Timzhao0205/PhD_Career_Portfolio/02_Startup/07_Frontier_Ideas_Interactive_2026-07/outputs/20_p4/P4_REPORT.md

# P4 scoring report (2026-07-28)

All 65 frozen longlist ideas were scored independently by the main Fable
5/xhigh agent against the 100-point rubric with hard gates G1-G7. Inputs:
frozen longlist records, the EVIDENCE files (facts and cited sources only —
historical analyst gate opinions treated as non-binding), the source atlas,
and the stage-10 refresh (R10-001..R10-079). Every score above 3 carries cited
source IDs. Weighted points equal score x weight / 5 and reconcile to totals
within 0.25 (one authoring slip on P3R2-D-18 was caught by the arithmetic
self-check and corrected to 66.7 before assembly).

## Calibration

Anchors: dual-leg, primary-evidenced demand with genuine whitespace and strong
founder transfer lands ~72-82 (D-02, C-01, D-10, C-05). Real-but-contested or
single-leg theses land ~55-67. Totals below ~55 almost always coincide with a
gate failure. The pilot's three fresh scores (C-09 73.7 / A-16 53.8 / F-15
47.9) were not reused; full-pass rescoring produced 72.0, 52.0, and 47.0 —
within calibration drift of the anchors.

## Distribution

- 65 scored: max 81.9 (D-02), min 44.4 (A-03), median ~62.7.
- Dispositions: 41 advance, 3 advance-with-repair (A-10, C-13, F-01 — G6
  counterparty restructuring off BIS Entity-Listed named buyers), 17
  eliminate on G1, 4 eliminate on G7.

## Gate failures (21 ideas)

G1 (demand) failures: A-03 (its own pre-declared kill condition met — Texas RE
guidance shows model-based PRC-029 compliance), A-11 (no buyer evidence; SEMI
E17 revision absent), A-16 (mid-supply-chain TIM, no buyer instrument), B-06,
B-14, B-22 (each failed its own binding pre-promotion condition after direct
search), D-11 (demand citations mis-typed; incumbent CO2 roadmap negative),
D-20 (leading thermal-battery architecture needs no liquid metal), E-02 (no
OEM agreement; AIM Act anchor litigated and relaxed), F-04 (externalization
thesis untested; CN leg failed its own conditional), F-05 (EPA funds new
equipment, not repowers; CARB tailwind reversing), F-11 (process substitution
with zero product demand), F-15 (bundled EPC procurement; SOE in-house
preference), F-17 (demand contingent on undated regulation; named buyer
Entity-Listed), F-22 (Guoli already occupies the CN second-source position),
G-01 (CEPC excluded from the 15th FYP — anchor trigger negated; binding
multi-tender condition unmet), G-02 (component pain inferred; no CNNC
follow-on tender).

G7 (timing) failures: C-02 (Delta ships the buffer function now — kill trigger
effectively tripped), C-03 (funded SST rivals occupy the window; the named
certification instrument does not cover the problem), D-08 (EtO NESHAP repeal
proposed; incumbents filling capacity before 2030), E-11 (ASE/TSMC in-house
thermal solutions ramp 2026; laser-relocation workarounds).

## Lane comparison

Strongest lanes: L03 (D-02 81.9, D-01 72.9 — conductor volume scales
independently of fusion success), L02/L08 datacenter-DC cluster (C-01 80.5,
E-14 75.5, G-03 67.8, A-02 64.8), L14 metrology/ops slice (C-05 78.3, F-19
64.6) outperforming L14 hardware bets, L12 defense photonics (D-10 78.7, C-13
74.2), L06 instrumentation (A-10 74.2, F-01 73.2). Weakest: CN-only ideas
whose own promotion conditions failed (B-06, B-14, F-15, F-17), and heavy-
capex power hardware without buyer instruments (C-03, C-12 54.9 survives
gates but ranks last-but-one among candidates). The refresh moved real ranks:
CEPC's exclusion eliminated G-01 and deflated F-09's CN leg; the H2Hubs
turbulence (2 hubs terminated, 5 restored ~$5B) reduced but did not eliminate
the hydrogen ideas (C-22 71.4, F-23 63.4, C-07 61.6).

## Survivor cut

Selection rule: exactly 30 — all gate-clean ideas ranked by total_100; G1/G7
eliminations excluded regardless of total. The cut fell at 62.7 (P3R2-F-10 in;
P3R2-C-07 out at 61.6, then C-21 60.4, F-06 59.5, A-13 59.5, F-02 59.4, A-21
58.7, D-07 58.4, F-03 58.3, F-07 58.2, F-20 57.7, C-19 56.0, F-12 56.0, F-09
55.2, C-12 54.9). Near-miss preservation: C-07's electrowinning fallback,
F-20's fold-into-C-09 path, and C-19's pairing with C-08 are recorded for
P5/P7 reconsideration if survivors fail red-team. Three survivors carry a
mandatory P5 repair focus: A-10 and C-13 must re-point CN legs off
Entity-Listed counterparties; F-01 must restructure its HK golden-reference
licensing scheme (strict-liability 50% Affiliates Rule).
