Timzhao0205/PhD_Career_Portfolio/02_Startup/07_Frontier_Ideas_Interactive_2026-07/outputs/70_audit/FINAL/PORTFOLIO/00_EXECUTIVE.md

# Executive synthesis — Folder 06 rerun, final 24 and top 10

## Recommendation

Fund the ten Tier-1 decisive experiments now ($3.47M total, every one
executable by 2028, every one carrying a written kill rule), hold the six
Tier-2 experiments as sequenced follow-ons ($2.08M), and treat the eight
Tier-3 ideas as tracked options ($2.75M) exercised only on their named
triggers. The portfolio's structural bet is consistent across lanes:
**neutral measurement, qualification, protection, and control layers for
infrastructure classes that are being built out faster than their
evidence layers** — REBCO conductors, 800 VDC datacenters, liquid
cooling, directed energy, HVDC transmission, superhot geothermal,
leading-edge etch, pulsed power, and electrolysis. No idea requires a
science breakthrough; every one requires disciplined instrumentation,
integration, and certification — the founder's stack.

## Tiers

**Tier 1 — fund the experiment now (ranks 1-8 plus C-09, C-22; the ten
deep dives).** P3R2-D-02 tape metrology ($120k), P3R2-C-01 800 VDC
protection ($350k), P3R2-C-05 cooling conformance ($150k), P3R2-D-10 CBC
phase control ($250k), P3R2-E-14 DC protection/HIL ($300k), P3R2-A-14
300 °C electronics ($850k, staged with a $250k first gate), P3R2-D-01
quench protection ($250k), P3R2-A-10 ion-energy control ($450k),
P3R2-C-09 pulsed-power modules ($500k, staged), P3R2-C-22 electrolyzer
bankability benches ($250k). Deep dives D01-D10 carry full plans,
scenario analyses, and dated kill gates.

**Tier 2 — sequence second ($2.08M).** C-13 GaN pump drivers ($180k),
F-01 solid-state RF matching ($250k), A-05 NEG coating ($250k), C-08
transient-qualified PCHEs ($600k), G-03 DC acceptance instrumentation
($300k), E-04 cryogenic interconnect ($500k). Each is fundable on its
own evidence; they sit behind Tier 1 for portfolio-concentration
reasons (C-13 overlaps D-10's buyer set; F-01 overlaps A-10's chamber
ecosystem; the rest carry heavier hardware risk per dollar of early
information).

**Tier 3 — tracked options ($2.75M).** D-09 FLASH dosimetry, A-22 PFAS
plasma destruction, C-04 PFAS-free two-phase loop, D-19 flywheel
buffers, F-16 plasma surface treatment (CN-primary), F-19 coolant
health, F-23 electrolyzer envelope controllers, D-16 space Brayton.
Each has a named exercise trigger in 04_ROADMAP.md; none should burn
capital before its trigger fires.

## Uncertainty, stated plainly

- **Repair-verdict ideas.** A-10, C-13, and F-01 carry stage-30 repair
  verdicts: their original CN structures were compliance-blocked
  (Entity List/VEU). All three are carried with restructured, gated CN
  chapters and US-primary base cases. Their cards say so; no repaired
  leg is presented as unconditional.
- **Confidence distribution.** Seven ideas carry high P4 confidence,
  fifteen medium, two low (F-23, D-16 — both Tier 3, both option-priced).
- **Residual risk.** Sixteen ideas sit at medium residual risk, eight at
  high — all eight high-residual ideas are Tier 2/3 except none in
  Tier 1; the deep-dived ten are uniformly medium.
- **Two constraints unsatisfiable by construction** (recorded in
  outputs/40_select/PORTFOLIO_CHECKS.json, restated here rather than
  hidden): no sub-$100k first experiment exists in the frozen pool
  (minimum $120k), and only 14 China beachheads / 13 dual-market
  structures were achievable against an 18-CN-beachhead aspiration,
  because CN-heavy candidates failed their own binding evidence gates
  at P4. The portfolio buys real dual-market exposure where it is
  deliverable and refuses to fabricate it where it is not.
- **Schedule-shaped risks.** D-10's design-win window (2026-2028) runs
  ahead of the 2030 launch convention and is handled as pre-company
  work; C-22 and F-23 are levered to hydrogen FID trajectories; D-01
  and D-02 are levered to the SPARC-to-ARC conversion.

## Resource allocation

Total decisive-experiment exposure across all 24: **$8.30M**, of which
Tier 1 is $3.47M. Recommended sequencing: start the four cheapest
highest-information Tier-1 experiments in 2026-2027 (D-02 $120k, C-05
$150k, C-22 $250k, D-10 $250k — combined $770k buys four kill verdicts),
run the remaining six Tier-1 gates through 2027-2028, and release Tier-2
capital only as Tier-1 verdicts land. Staged experiments (A-14, C-09)
gate internally so worst-case exposure is the first stage, not the
headline. Every experiment's pass and kill thresholds are tabulated in
04_ROADMAP.md; every card in 01_IDEA_CARDS.md names its kill condition.

## What would change this recommendation

A Tier-1 kill-gate failure removes that idea without substitution (the
final 24 and top 10 are frozen identities; any forced change returns to
Stage 40 per the route contract). External events with standing
portfolio effect: an OCP full-methodology release (C-05 scenario B), a
CFS-published protection standard (D-01 scenario B), JBCS awards with no
subsystem carve-out (D-10 scenario B), integrated IEDF-inference
releases (A-10 scenario B), and hydrogen FID collapse (C-22/F-23
scenario D). Each is an observable, dated public event tracked in the
roadmap's monitoring calendar.
