Timzhao0205/PhD_Career_Portfolio/03_Investments_and_Finance/03_Investments_and_Finance_Folder_Info.md

# 03_Investments_and_Finance

Learning track for markets, company analysis, and paper-trading simulation. Strictly
educational: no real transactions, no brokerage connections, no investment execution.

- `01_Market_Learning_Lab_2026-07/` — reading-first curriculum + research lab
  (Huawei 计算 case). Start: its `00_README_START_HERE.md`.
- `02_Ascend_Benchmark_Mission_2026-07/` — autonomous Claude Code mission producing the
  filing-verified ANSWER KEY (reports + Excel + benchmark paper portfolio) for the
  self-test. Run: `RUN_BENCHMARK.ps1`. Do the blind attempt before opening 30_/40_.
