Timzhao0205/PhD_Career_Portfolio/03_Investments_and_Finance/01_Market_Learning_Lab_2026-07/01_Market_Learning_Lab_2026-07_Folder_Info.md

# 01_Market_Learning_Lab_2026-07

Self-contained learning lab: markets curriculum + live research case (Huawei 计算 /
Ascend supply chain) + paper portfolio + calibration tracking. Paper-only, not financial
advice. Start with `00_README_START_HERE.md`. Reading-first for now; Claude Code missions
are pre-specified in `CLAUDE.md` for when compute work begins.
