Timzhao0205/PhD_Career_Portfolio/02_Startup/06_Frontier_Idea_Research_2026-07/30_SCREENING/SELECTION.md

# P5 final selection

All 24 concepts pass the literal hard gates. Conditional experiments, held candidates, and killed replacements receive no quota credit.

| Rank | Idea | Concept | Lane | Role | Archetype | US | China | Score | Experiment |
|---:|---|---|---|---|---|:---:|:---:|---:|---:|
| 1 | `P3R2-D-02` | Reel-to-reel contactless REBCO tape quality metrology (Hall-array critical-current mapping + delamination screening) sold to tape vendors and magnet builders as certified acceptance instrumentation. | L03 | diagnostic_test | industrial | Y | Y | 65.6 | $120,000 |
| 2 | `P3R2-C-22` | Electrolyzer stack degradation-emulation and bankability test systems: programmable ripple/intermittency benches that turn stack warranties into measurable engineering | L11 | diagnostic_test | industrial | Y | Y | 64.6 | $250,000 |
| 3 | `P3R2-D-01` | Merchant quench-detection-and-protection subsystem for REBCO/HTS magnets: co-wound distributed fiber-optic sensing plus sub-millisecond active energy extraction, sold with a qualification dossier to fusion companies and national labs. | L03 | scientific_system | scientific_big_physics | Y | N | 62.8 | $250,000 |
| 4 | `P3R2-F-01` | Solid-state microsecond impedance-matching engines (switched SiC/PIN capacitor arrays replacing motorized vacuum-capacitor matchboxes) for pulsed and tailored-waveform RF plasma tools | L06 | process_output | industrial | Y | Y | 59.8 | $250,000 |
| 5 | `P3R2-C-01` | 800-VDC rack power-path protection: integrated solid-state breaker + precharge/inrush control + insulation monitoring + hot-swap sequencing unit for AI racks and power sidecars | L02 | infrastructure | infrastructure_utility_transport | Y | Y | 59.6 | $48,000 |
| 6 | `P5-USSCI2-S01` | Qualified diamond transmission-dynode membrane and integration cartridge for hybrid MCP-PMTs used in EIC-class photon detectors | L13 | process_output | scientific_big_physics | Y | N | 58.2 | $94,000 |
| 7 | `P3R2-E-14` | Multi-terminal DC fault-discrimination protection relay plus vendor-neutral hardware-in-the-loop qualification platform for MVDC datacenter distribution and HVDC converter stations - the 'SEL of DC grids.' | L08 | infrastructure | infrastructure_utility_transport | Y | N | 56.4 | $300,000 |
| 8 | `P5R2-CN-01` | Retrofit X-ray computed-laminography kit for advanced-packaging failure analysis | L06 | diagnostic_test | industrial | Y | Y | 55.6 | $120,000 |
| 9 | `P3R2-A-14` | 300C-class mixed-signal instrumentation electronics platform (SiC/SOI) for superhot geothermal, downhole, and turbine environments | L15 | process_output | industrial | Y | N | 54.6 | $850,000 |
| 10 | `P3R2-C-13` | Precision GaN pump-driver and laser-power modules: nanosecond-class programmable current drive as a merchant subsystem for industrial and defense-adjacent laser OEMs | L12 | process_output | industrial | Y | Y | 54.2 | $72,000 |
| 11 | `P3R2-C-08` | Thermal-shock-tolerant printed-circuit heat exchangers (PCHE): merchant diffusion-bonded recuperators for sCO2 power, heat pumps, and hydrogen precooling | L04 | process_output | industrial | Y | Y | 51.6 | $65,000 |
| 12 | `P3R2-B-01` | Sealed negative-pressure (subatmospheric) water/low-GWP two-phase cold-plate loop for >2 kW/chip Chinese AI racks - leak-safe by physics (air leaks in, coolant never leaks out), PFAS-free by design | L14 | infrastructure | infrastructure_utility_transport | N | Y | 51.0 | $55,000 |
| 13 | `P3R2-E-04` | High-density cryogenic interconnect loader with co-packaged 4K readout front-end (superconducting flex harness + cryo-CMOS multiplexing + cryo-LNA), breaking the 256-channel-per-loader wall for quantum computers. | L13 | scientific_system | scientific_big_physics | Y | N | 51.0 | $60,000 |
| 14 | `P5R2-CN-03` | Field-deployable industrial high-temperature heat-pump commissioning and measurement-and-verification island | L04 | diagnostic_test | industrial | N | Y | 50.0 | $120,000 |
| 15 | `P3R2-F-02` | Superconducting-magnet electrical balance-of-plant platform: standardized precision drive-and-dump skids (10 ppm-class high-current DC converters + energy-extraction/dump units + current leads + busbars) | L03 | scientific_system | scientific_big_physics | Y | Y | 49.4 | $400,000 |
| 16 | `P3R2-C-04` | PFAS-free pumped two-phase direct-to-chip cooling loop: hermetic, fluid-agnostic evaporator/condenser subsystem co-qualified with low-GWP non-PFAS working fluids | L14 | infrastructure | infrastructure_utility_transport | Y | Y | 49.0 | $400,000 |
| 17 | `P3R2-F-12` | Classification-certified DC power and protection stacks for battery-electric and battery-swap inland/coastal vessels (CCS Rules-native string protection, insulation monitoring, containerized-pack power interface) | L10 | infrastructure | infrastructure_utility_transport | N | Y | 47.6 | $75,000 |
| 18 | `P3R2-G-01` | Closed-loop UHV chamber conditioning and acceptance-certification systems for China's big-science vacuum supply chain: instrumented vacuum-firing/bakeout stations with measured hydrogen-outgassing endpoints, integrated rate-of-rise/leak/RGA acceptance metrology, and tamper-evident per-chamber certification - sold as equipment plus recurring calibration to the China-registered fabricators who alone may bid HEPS/CEPC-class chamber tenders. | L07 | process_output | industrial | N | Y | 47.6 | $300,000 |
| 19 | `P3R2-A-10` | Vendor-neutral ion-energy-distribution metrology + tailored-waveform bias control retrofit for plasma etch chambers | L06 | process_output | industrial | Y | Y | 47.4 | $450,000 |
| 20 | `P3R2-G-03` | DC-conversion acceptance and commissioning instrumentation: a portable measurement island (swept-impedance bus-stability analyzer, IT-network insulation/ground-fault characterization, hot-swap/inrush transient capture) plus standardized acceptance protocols and signed dossiers, for facilities converting legacy UPS power rooms to 240V/336V/+-400V/800VDC and for vendors qualifying DC shelves - the measurement layer of the DC transition, not another in-path power product. | L02 | diagnostic_test | infrastructure_utility_transport | Y | Y | 47.0 | $38,000 |
| 21 | `P3R2-D-12` | Electrohydrodynamically-pumped two-phase cold plates: field-driven, no-moving-parts per-chip flow control for 3-5 kW AI packages, with a non-PFAS working-fluid plan. | L14 | infrastructure | infrastructure_utility_transport | Y | Y | 46.8 | $180,000 |
| 22 | `P3R2-F-23` | PEM electrolyzer 'protective operating envelope' controllers with warranty-grade black-box logging: embedded plant hardware that shapes current/OCV stress and produces bankable degradation evidence | L11 | process_output | industrial | Y | Y | 44.2 | $45,000 |
| 23 | `P3R2-F-06` | Precision wideband DC current/voltage sensing platform (optical and zero-flux hybrid) for HVDC converter stations, electrolyzer plants, and magnet systems | L08 | infrastructure | infrastructure_utility_transport | Y | N | 42.4 | $35,000 |
| 24 | `P3R2-F-03` | High-speed permanent-magnet turbo-generator + power-converter 'electrical cartridge' (0.3-20 MW) for waste-heat sCO2 and geothermal/ORC power blocks | L04 | process_output | industrial | Y | Y | 37.2 | $68,000 |

## Constraint readback

- Lanes: 12 distinct; maximum 3 per lane.
- Archetypes: industrial 12; scientific/big-physics 4; infrastructure/utility/transport 8.
- Geography: US 20; China 18; dual 14.
- Decisive experiments below $100,000: 11.
- Top 10 are the first 10 rows by adjudicated score; score uncertainty is retained in every downstream report.
