Timzhao0205/PhD_Career_Portfolio/02_Startup/06_Frontier_Idea_Research_2026-07/40_DEEP_DIVES/DD_P3R2_C_22.md

# P3R2-C-22 — Electrolyzer degradation-emulation and bankability test systems

<!-- SOURCE_IDS: L11-001 L11-002 L11-003 L11-004 L11-021 L11-032 L11-046 L11-047 L11-048 L11-049 L11-050 L11-051 L11-005 L11-006 P3R2-C-22-S03 P3R2-C-22-S04 P3R2-C-22-S01 P3R2-C-22-S02 L11-007 L11-008 -->

**Frozen portfolio position:** rank 2, score 64.6/100, medium confidence; G1, G4, and G6 remain marginal rather than fully de-risked. The precompany thesis is testable by 2029 and compatible with a 2030 launch, but no signed access agreement, purchase order, or paid evaluation is assumed here.

## Investment thesis

Build the independent instrument that tells an electrolyzer buyer which electrical operating history caused which loss mode—and whether a warranty deserves to be financed. The initial product is a 50–500 kW test system that can synthesize rectifier ripple, renewable-generation profiles, starts, stops, ramps, and open-circuit rest; measure voltage, impedance, temperature, pressure, flow, gas quality, and cell imbalance; and convert those observations into a mechanism-aware degradation dossier. The long-run product is not merely the power cabinet. It is a permissioned, cross-campaign evidence base linking imposed stress, diagnostic signatures, field behavior, and warranty outcomes.

This is attractive because the scientific problem is real while the industry’s demand outlook is contradictory. Peer-reviewed work shows intermittent operation and open-circuit intervals can produce non-monotonic and eventually pronounced degradation, while ripple changes resistance and energy consumption even when mean hydrogen output is similar ([L11-001](https://iopscience.iop.org/article/10.1149/1945-7111/ae1cf1), [L11-021](https://pmc.ncbi.nlm.nih.gov/articles/PMC8877858/)). Long-duration studies can now decompose voltage decay among membrane, catalyst-layer, porous-transport-layer, and contact-resistance contributions ([L11-003](https://iopscience.iop.org/article/10.1149/1945-7111/add184)). Yet a 2024 government laboratory publication still described accelerated-stress methods as proposed protocols and broad stack-qualification guidance, not a settled commercial bankability standard ([P3R2-C-22-S01](https://publications.jrc.ec.europa.eu/repository/handle/JRC133726)).

The investment case is therefore a hedge on sector volatility. Expansion creates more commissioning and acceptance work. Consolidation makes survivors more sensitive to warranty reserves, failed projects, and credible life prediction. That hedge is not perfect: fewer projects also mean fewer budgets. The opportunity is best viewed as a high-value test-and-measurement niche, not as a bet that every announced hydrogen project will be built.

## Exact buyers, job to be done, and current demand proof

The first U.S. buyers are stack-OEM warranty and reliability teams; hydrogen-hub developers and engineering contractors preparing factory- or site-acceptance plans; and lender, insurer, or owner technical advisers who must decide whether a stack’s duty cycle is consistent with its guarantee. The job is specific: translate a proposed power profile into a reproducible stress program, identify the dominant degradation signatures, rank competing stacks under that profile, and document uncertainty before a large asset is commissioned.

Current category demand is substantial but exact product demand is still marginally proven. The U.S. Department of Energy awarded up to $2.2 billion of federal cost share to two named regional hydrogen hubs in late 2024 ([L11-032](https://www.energy.gov/articles/biden-harris-administration-announces-awards-22-billion-two-regional-clean-hydrogen-hubs)). A 2026 funding-status review reported that five of the original seven hubs remained preserved, while two had been cancelled; that reduction is important disconfirming evidence, not a footnote ([P3R2-C-22-S03](https://decarbonfuse.com/posts/doe-restores-1-2b-for-dac-hubs-and-5-hydrogen-projects)). Plug Power reported $187 million of 2025 electrolyzer revenue, an approximately $8 billion sales funnel, more than 300 MW of cumulative shipments, and named multi-megawatt deployments ([L11-046](https://www.ir.plugpower.com/press-releases/news-details/2026/Plug-Power-Reports-Q4-and-Full-Year-2025-Results-with-Strong-Sales-Growth-and-Margin-Expansion/default.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)). These sources prove stacks, projects, and warranty exposure; they do not prove that an independent degradation-emulation bench has already been purchased.

China’s first buyers are large electrolyzer OEM reliability groups, engineering-and-procurement contractors running multi-vendor tenders, project-owner acceptance laboratories, and independent test laboratories serving those actors. The exact job is to compare stacks under the project’s actual curtailment and ramp profile, reproduce poor-load behavior, and turn acceptance criteria into auditable test evidence. A case study of Sinopec’s Kuqa project reported only about 20% of rated electrolyzer capacity in 2023 and attributed underperformance partly to insufficient power and low-load electrolyzer inefficiency ([L11-049](https://www.woodmac.com/news/opinion/hydrogen-case-study-sinopec-kuqa-project/)). A China Energy Construction framework qualified 14 suppliers and contemplated 125 sets; the publicly disclosed Songyuan tender alone covered 64 sets won across six suppliers ([L11-051](https://h2.solarbe.com/news/20241105/4113.html)). Contract reporting also names LONGi Hydrogen, CSSC Peric Hydrogen, and Sungrow Hydrogen in active commercial supply ([L11-050](https://finance.sina.com.cn/roll/2025-03-05/doc-inenqpat1980896.shtml)). A 2026 policy report reaffirmed a national 2030 renewable-hydrogen target of two million tonnes ([P3R2-C-22-S04](https://www.stcn.com/article/detail/3980005.html)). Again, this proves buyer-side testing pain and timing, not a committed order for this product.

## Product boundary

The company should not manufacture electrolyzer stacks, build entire hydrogen plants, certify assets by fiat, or promise that a 90-day test predicts twenty years of life. Version one is a PEM-focused merchant test platform with four tightly bounded layers:

1. A bidirectional or dissipative programmable DC power stage that reproduces specified ripple spectra, ramps, dropouts, rest periods, and renewable profiles while preserving traceable voltage and current measurements.
2. A safety and balance-of-plant module for water, gas separation, cooling, pressure, purge, ventilation, and emergency shutdown, sized initially for commercial short stacks.
3. Synchronized diagnostics: cell-voltage channels, impedance or perturbation measurements, temperatures, pressures, flow, gas purity/crossover, and energy efficiency.
4. A protocol and evidence layer that registers the stress recipe, detects degradation signatures, carries uncertainty forward, and produces a warranty/acceptance dossier.

The boundary matters because Greenlight Innovation already offers general electrolyzer test stations up to 4 MW, 30,000 A, and more than 1,000 V, including standard process measurements and optional electrochemical diagnostics ([P3R2-C-22-S02](https://www.greenlightinnovation.com/products/electrolyser/electrolyser-testing)). Programmable power and data acquisition alone are not whitespace. The defensible wedge must be a validated library of duty-cycle stressors, held-out prediction, project-specific emulation, and a buyer-readable qualification record. Generic laboratory research features should be bought or integrated rather than rebuilt.

## Physics and build path

The underlying physics is tractable enough to instrument but too heterogeneous for a single empirical “aging multiplier.” Ripple changes instantaneous current, thermal load, and electrochemical overpotential; its amplitude and frequency can shift resistance growth and energy loss ([L11-021](https://pmc.ncbi.nlm.nih.gov/articles/PMC8877858/)). Open-circuit intervals and restart transients change electrode potentials and can accelerate catalyst or support damage; the intermittent-operation evidence shows early apparent improvement followed by degradation, warning against extrapolating from a short initial window ([L11-001](https://iopscience.iop.org/article/10.1149/1945-7111/ae1cf1)). Membrane, catalyst, porous transport, and interface losses can all appear as increasing cell voltage, so the system must combine time-series behavior with impedance and post-test inspection rather than fit one degradation slope ([L11-002](https://www.sciencedirect.com/science/article/abs/pii/S0016236125036452), [L11-003](https://iopscience.iop.org/article/10.1149/1945-7111/add184)). A recent review provides a map of intermittency-specific mechanisms and mitigation strategies, but a review does not eliminate the need for stack-specific calibration ([L11-004](https://www.sciencedirect.com/science/article/pii/S1364032125008433)).

The build sequence is: validate waveforms and metrology on a passive/electronic load; commission a 1–5 kW stack loop; reproduce published ripple and open-circuit signatures; move to two 50 kW commercial short stacks; then test whether a model trained on one segment predicts a blinded segment and preserves the stacks’ life ranking. Hardware integration is conventional high-power test engineering. The scientific difficulty is domain transfer across catalyst loading, membrane, compression, water quality, operating pressure, and manufacturing variation.

The platform can later address other electrochemical systems, but that is option value, not beachhead evidence. Peer-reviewed CO and carbon-dioxide electrolysis studies demonstrate rapidly changing catalysts, high current densities, and different product-selectivity failure modes ([L11-005](https://www.nature.com/articles/s41467-024-49095-2), [L11-006](https://www.nature.com/articles/s41467-024-45538-y), [L11-007](https://www.nature.com/articles/s41467-026-69506-w), [L11-008](https://www.nature.com/articles/s41467-019-11599-7)). They show why a programmable electrochemical-test architecture may expand, but they do not validate the initial water-electrolyzer market.

## Named incumbents, bear case, and the explicit 10× test

Greenlight is the direct merchant incumbent. Plug Power, Nel, and thyssenkrupp nucera represent the in-house-lab response: an OEM may prefer to retain qualification data and improve its own benches. Nel’s year-end 2025 backlog was down 18% year on year even though quarterly order intake recovered sharply ([L11-047](https://nelhydrogen.com/press-release/nel-asa-fourth-quarter-2025-financial-results/)). Thyssenkrupp nucera’s backlog fell from €1.1 billion to €0.6 billion and its green-hydrogen order intake was only €26 million for the year ([L11-048](https://www.thyssenkrupp-nucera.com/thyssenkrupp-nucera-returns-to-profit-in-2024-2025-despite-decline-in-sales/)). Contraction may heighten scrutiny per surviving order, but it also gives incumbents fewer reasons to share data and fewer external programs to fund.

The strongest bear case is that the company becomes an expensive custom test integrator. Greenlight can add stress-profile libraries and analytics to installed hardware. OEMs can keep proprietary field failures inside warranty teams. Financiers may accept conventional performance guarantees rather than fund a new prediction method. The cross-OEM dataset—the intended moat—may never form because confidentiality incentives are stronger than pooling benefits. U.S.–China operational separation may further fragment data.

The 10× claim must therefore be tested as predictive decision speed, not waveform speed. **Pass:** a pre-registered 90-day campaign produces at least a tenfold reduction in time to a buyer-useful life-ranking decision relative to the available long-duration baseline; classifies at least 80% of held-out degradation-signature windows correctly; preserves the direction and rank of degradation across both short stacks; and predicts held-out voltage-decay rate within ±20%, with an uncertainty interval that actually covers the observation. **Kill:** rankings reverse, the model learns stack identity rather than stress response, a mechanism appears only under acceleration, or prediction intervals are too wide to change a warranty or acceptance decision. “Twenty years in 90 days” should not be used until multi-year field correlation exists.

## Decisive experiment, budget, and pass/kill rules

The frozen decisive experiment remains a **$250,000, 2027, 90-day campaign** on two commercial 50 kW short stacks. A reasonable planning allocation is $90,000 for stacks and fixtures; $70,000 for programmable power, load, and switching modifications; $35,000 for water, gas, cooling, ventilation, and safety; $25,000 for impedance and synchronized instrumentation; and $30,000 for facility, consumables, calibration, and contingency. These are planning assumptions, not supplier quotations.

Pre-register four regimes: clean steady DC; controlled ripple at multiple frequencies and amplitudes; repeated open-circuit rest/restart; and a representative renewable-profile replay. Randomize or counterbalance regimes where the hardware allows. Retain blinded time windows and at least one stress sequence from model fitting. Measure cell voltages, efficiency, impedance features, pressure/flow, crossover or gas-quality proxies, and post-test physical or chemical evidence through a partner laboratory.

Technical pass requires reproducible imposed waveforms; no safety excursion; statistically separable signatures for at least three stress regimes; the 10× prediction thresholds above; and a credible causal mapping consistent with the published mechanism literature. Commercial pass requires at least two independent buyer classes to review the dossier and one to define a paid next-step scope by the end of 2028. This is a future threshold, not a claim of present access. Kill the company thesis if the technical thresholds fail twice, if users value only generic bench capacity, or if every prospective buyer refuses to provide even anonymized outcome labels under a workable data agreement.

## Bottom-up niche arithmetic

No accepted source provides a reliable market price for this exact product, so the arithmetic must expose assumptions. For the U.S., begin with five preserved hubs. Assume two major electrolyzer packages per hub, two independent qualification points per package—pre-delivery and commissioning—and an average $250,000 campaign. That is **5 × 2 × 2 × $250,000 = $5 million** of potential campaign work across the principal build wave. Add eight OEM, engineering, lender-adviser, or laboratory accounts averaging one $250,000 campaign per year for five years: **8 × 1 × $250,000 × 5 = $10 million**. If six of those accounts buy a $1 million bench and $100,000 annual protocol/software support, hardware contributes $6 million and five-year support contributes $3 million. The directional U.S. 2030–2034 niche is therefore about **$24 million**, before discounting for competition and project cancellations.

For China, anchor unit volume to the 125-set procurement framework and the disclosed 64-set tender, without assuming every set needs a separate campaign. Assume ten multi-vendor project or OEM programs per year, two campaign decisions per program, a lower average campaign value of $175,000, and five years: **10 × 2 × $175,000 × 5 = $17.5 million**. Assume eight locally supported bench sales at $800,000 plus $75,000 annual support for an average of three years: $6.4 million hardware plus $1.8 million support. That yields about **$25.7 million**.

Combined, the explicit scenario is roughly **$50 million over five years**, or approximately $10 million annualized, with a plausible range of $25–80 million as campaign count, pricing, and localization vary. This is a credible specialist-instrument company, not proof of a billion-dollar category. Upside requires the protocol/data layer to become recurring and accepted across many owners; downside is a project-services business with lumpy revenue.

## U.S. route

In 2026–2027, operate through a university or independent electrochemistry laboratory that already has ventilation, water treatment, gas handling, and trained operators. Publish the protocol and negative results while retaining implementation know-how in control, calibration, uncertainty, and reporting. In 2028, seek two separately scoped pilots: one with an OEM or engineering contractor focused on warranty engineering, and one with an owner/lender technical adviser focused on acceptance decisions. Data rights must be negotiated at the feature and anonymization level; “shared dataset” cannot mean exposing a customer’s identifiable failure history.

In 2029, the go/no-go threshold is one paid campaign or formal paid evaluation path, a written test specification from a second buyer class, and evidence that an independent dossier changes an acceptance or warranty decision. A 2030 launch should sell campaigns first and capital equipment second, avoiding a field-service organization before protocols stabilize. The five preserved hub programs and live OEM shipments provide a route to named accounts, but outreach and facility access remain work to earn, not assets already held.

## China route

The China route should be operationally separate: locally incorporated sales and service, a localized bill of materials, local calibration and safety documentation, and customer data stored and governed under the applicable China rules. The first offer is a project-profile qualification campaign delivered with a qualified local laboratory, followed by a domestically supported bench. The target account is not “the hydrogen market” in general; it is the reliability leader at an OEM, the acceptance-test owner inside an engineering contractor, or the laboratory responsible for comparing suppliers in a multi-vendor program.

The 2030 production target, the Kuqa low-utilization evidence, and the 64-set tender demonstrate timing and a concrete comparison problem. They do not establish willingness to accept a foreign evidence model. By 2028 the company must show that a locally produced report can enter an owner’s acceptance workflow. Kill the China route if three well-qualified target organizations insist on fully internal benches and will not purchase an independent campaign, or if data separation destroys the model’s usefulness. Do not make cross-border pooling a prerequisite for the local product to work.

## Safety and compliance

The bench combines high DC power, hydrogen, oxygen, pressure, water, heat, and potentially caustic electrolyte. Safety architecture must include independently wired emergency shutdown, hydrogen detection, forced ventilation, purge sequencing, leak and crossover monitoring, pressure relief, fail-closed valves, isolation and lockout, DC arc-flash analysis, insulation monitoring, overtemperature protection, and a defined safe state after loss of control power. Software interlocks supplement rather than replace hardwired protection. Hazard analysis must cover unintended hydrogen–oxygen mixing, blocked outlets, water starvation, cell reversal, sensor drift, cooling loss, and energization during maintenance.

U.S. deployments require facility-specific electrical and hazardous-location review, pressure-component review, fire-code coordination, calibrated instrumentation traceability, and an independent listing or field evaluation where applicable. China deployments require the corresponding national electrical, pressure, measurement, environmental, and laboratory-accreditation path, with Chinese-language manuals and local emergency procedures. The product must never present its own report as statutory certification. Claims should state the tested configuration, calibration chain, protocol version, uncertainty, deviations, and limits of inference.

## Milestones, 2030 launch, and 2030–2034 triggers

**2026:** reproduce one published ripple result and one intermittent/open-circuit result at 1–5 kW; complete hazard analysis; interview at least 20 named U.S. and China buyer-side roles; define data-rights templates. **2027:** build and run the frozen 50 kW, two-stack, 90-day experiment; publish the pre-registered method and correlation limits. **2028:** conduct two external beta campaigns under separate buyer use cases; demonstrate blinded prediction and produce the first acceptance-style dossier. **2029:** require paid scope from at least one buyer class in each pursued route, plus one repeatable facility deployment and a credible manufacturing/service budget. These are milestones, not claims that engagements already exist.

Launch in 2030 only if three triggers overlap: U.S. hub or industrial projects reach equipment acceptance and commissioning; China’s next build wave creates repeated multi-vendor comparison or underperformance remediation; and warranty pressure makes independent evidence worth paying for. From 2030–2034, expand from PEM short stacks to larger stacks and then other electrolyzer types only after mechanism-specific validation. A weak project market is survivable if the installed base purchases diagnosis and warranty work; it is not survivable if both new builds and installed-base spending disappear.

## Risks, kill rules, and evidence durability

The primary risks are acceleration non-equivalence; stack-to-stack confounding; insufficient field labels; customer refusal to share data; Greenlight feature expansion; OEM internalization; hydrogen-project cancellation; custom-engineering creep; facility and safety cost; and fragmented U.S.–China data governance. Kill by end-2029 if no buyer will pay for a defined evaluation, no independent party will permit a blinded comparison, or the report does not change a real acceptance/warranty decision. Kill by end-2033 if neither route yields bench sales or recurring paid campaigns. Narrow to a laboratory tool if predictive bankability fails but the instrument itself sells; do not describe that fallback as the original thesis succeeding.

The mechanism evidence in peer-reviewed electrochemistry is comparatively durable: ripple, intermittent-operation, and component-level degradation will remain relevant even as vendors change. The proposed-protocol gap is moderately durable but should be refreshed as standards mature. Funding status, OEM backlogs, tender counts, named projects, vendor features, prices, data rules, and the 2030 policy target are refresh-sensitive. Refresh them before each financing decision and again in 2029; do not carry 2026 market figures into launch planning unchanged.

## Verdict

**Advance as a precompany validation program, not yet as an assumed venture.** The idea earns its frozen high rank because it joins controllable high-power instrumentation to a real, scientifically difficult warranty problem in both the U.S. and China. It also has a useful downside product: a rigorous stress-emulation bench. But the score of 64.6 and marginal G1/G4/G6 status are appropriate. Greenlight occupies the hardware layer, category spending is not product-specific purchasing, and the moat depends on held-out predictive validity plus permissioned data that customers may withhold. The 2027 experiment is decisive: if it produces a tenfold faster, accurate decision and buyers define a paid follow-on, proceed toward a 2030 launch. If prediction or paid data access fails, kill the bankability-platform thesis rather than polishing the cabinet.
