Timzhao0205/PhD_Career_Portfolio/02_Startup/06_Frontier_Idea_Research_2026-07/40_DEEP_DIVES/DD_P3R2_F_01.md

# P3R2-F-01 - Solid-state microsecond RF impedance-matching engine

<!-- SOURCE_IDS: L06-001 L06-002 L06-003 L06-009 L01-012 L06-039 L06-042 L06-043 L06-044 L06-048 L06-054 L06-051 L06-004 L06-005 P3R2-F-01-S04 P3R2-F-01-S01 P3R2-F-01-S03 P3R2-F-01-S02 L06-006 L06-007 -->

**Frozen position:** rank 4 of 24; score 59.8/100; confidence medium; TRL 4; US and China beachheads. G2, G3, G4, and G5 pass; G1, G6, and G7 pass only marginally. The frozen concept is a solid-state, pulse-synchronous impedance-matching engine for RF plasma tools. This report does not upgrade that score, infer customer commitments, or broaden the frozen gates.

## Investment thesis

Pulsed plasma tools ask an impedance-matching network to solve a dynamic problem with hardware designed around mechanical motion. As plasma conditions change within and between pulses, the load seen by the RF source changes; a slow match leaves reflected energy, unsettled power delivery, and less control over the waveform delivered to the process. Recent peer-reviewed work still treats matching models and real-time assistance as active problems in semiconductor plasma etch ([L06-001](https://pubs.aip.org/avs/jvb/article/42/2/022212/3277858/Modeling-and-control-of-L-type-network-impedance), [L06-002](https://pubs.aip.org/aip/jap/article/137/3/033301/3331468/Impedance-matching-assistance-based-on-frequency), [L06-003](https://www.mdpi.com/2079-9292/10/17/2074)). Tailored-voltage-waveform research makes the timing problem more important, because the desired process input is itself changing rapidly rather than remaining a steady sinusoid ([L01-012](https://pubs.aip.org/avs/jva/article/37/2/021303/247270/Experimental-demonstration-of-multifrequency), [L06-009](https://pubs.aip.org/aip/pop/article/31/3/033508/3279954/Voltage-waveform-tailoring-for-high-aspect-ratio)).

The proposed wedge is deliberately narrow: a 13.56 MHz, 5 kW switched-capacitor matching module that can move among prequalified impedance states in less than 10 microseconds, synchronize those states to the pulse recipe, and report forward power, reflected power, switch health, and excursions. The nearest primary-source incumbent benchmark in the evidence pack is Comet's Synertia matching network. Comet specifies standard or customized capacitor designs and tuning below 500 milliseconds depending on preset points, at up to 15 kW across a broad frequency range ([P3R2-F-01-S03](https://pct.comet.tech/en/products/synertia_rf_power_delivery_platform/synertia_rf_matching_network)). That is unusually strong evidence that a current commercial product remains capacitor-mechanical rather than a merchant solid-state microsecond matcher.

The opportunity is not established merely by dividing 500 milliseconds by 10 microseconds. Electrical settling speed has value only if it reduces reflected energy, preserves waveform fidelity, and improves or stabilizes a process result without creating arcing, harmonics, or premature failure. The company thesis is therefore conditional: a component supplier can earn a defensible socket if it proves pulse-by-pulse electrical benefit, vacuum-capacitor-class operating integrity at the initial point, and a design-in path through one RF-generator or tool vendor before incumbents internalize the same function.

## Exact buyers, painful job, and demand evidence

The first US buyer is not a fab procurement office buying an anonymous box. It is an RF-generator vendor, matching-network platform owner, or plasma-tool OEM that already controls generator interfaces and qualification. Advanced Energy's Q4 2025 transcript reports a large semiconductor segment and says newer RF/plasma-power platforms had broad customer acceptance while remaining in early pilot or production stages ([L06-039](https://www.fool.com/earnings/call-transcripts/2026/02/10/advanced-energy-aeis-q4-2025-earnings-transcript/)). That proves a current, revenue-bearing category and active platform refresh. It does not say that Advanced Energy, a tool OEM, or a fab has requested this startup's sub-10-microsecond module. G1 stays pass-marginal for exactly that reason.

The exact buyer job is to keep delivered RF power close to the commanded pulse trajectory when chamber impedance moves faster than a motorized network can follow. The buyer must also avoid an integration penalty: the new matcher cannot contaminate the spectrum, destabilize the plasma, increase arc events, impair endpoint repeatability, or require a service model worse than today's matchbox. A generator vendor could value a qualified daughter module or co-developed reference design; a tool OEM could value a recipe-synchronous subsystem; a fab is more likely to influence specifications and validation than to be the first direct buyer.

China has a separate category-demand case. Hengyunchang's IPO-related disclosures describe substantial investment in semiconductor RF-power-system industrialization and very concentrated sales to named domestic equipment companies ([L06-042](https://www.cls.cn/detail/2060122), [L06-043](https://www.cls.cn/detail/2272598)). Injet's 2024 results identify its semiconductor and electronic-materials activity as a growth contributor ([L06-044](https://news.qq.com/rain/a/20250425A0341L00)). AMEC reported approximately RMB 9.065 billion of 2024 revenue, including about RMB 7.277 billion from etch equipment, alongside unusually high R&D spending ([L06-048](https://www.stcn.com/article/detail/1673114.html)). These records establish scaled domestic tool and RF-subsystem activity. They do not establish a purchase order, paid evaluation, or license for the proposed matcher.

The localization backdrop is directionally favorable but must not be mistaken for product demand. A Yicai account describes low domestic share in semiconductor RF power, dominant foreign incumbents, and domestic suppliers entering verification or production ([L06-054](https://www.yicai.com/news/102170278.html)); TrendForce reports rising domestic adoption in semiconductor equipment categories ([L06-051](https://www.trendforce.com/news/2026/01/12/news-chinas-domestic-chip-equipment-adoption-beats-2025-target-at-35-led-by-naura-amec/)). The official 2026-2030 plan identifies integrated circuits and supply-chain self-reliance as priority work ([P3R2-F-01-S04](https://www.news.cn/politics/20260313/085af5de5a4b4268aa7d87d90817df2f/c.html)). These sources support a dated market trigger, not willingness to buy foreign-origin switching IP.

## Product boundary and business model

V1 is a single-frequency, single-power-class module, not the frozen long-term family's full 400 kHz-60 MHz envelope. It contains the switched reactive network, voltage/current and directional-power sensing, isolated gate drive, an FPGA-class state estimator and scheduler, a safe-state controller, thermal management, health telemetry, and a documented generator interface. The module may use SiC and PIN switching elements in different branches according to loss, voltage, and speed. It is sold first as evaluation hardware plus nonrecurring integration engineering, then as a qualified production subsystem with calibration and reliability reporting.

The company does not build the RF generator, chamber, vacuum system, process recipe, or plasma diagnostic. It does not promise wafer-level process improvement before a controlled chamber study. It does not claim that the 13.56 MHz prototype proves 60 MHz voltage handling, Q, or lifetime. It also does not treat a matching model as proprietary physics: control-oriented L-network analysis and dual-frequency circuits are in the peer-reviewed record ([L06-001](https://pubs.aip.org/avs/jvb/article/42/2/022212/3277858/Modeling-and-control-of-L-type-network-impedance), [L06-003](https://www.mdpi.com/2079-9292/10/17/2074)). Defensibility must come from a measured safe operating envelope, switch-stack design, pulse-state compiler, arc-resistant transitions, calibration, reliability data, and qualification history.

The preferred commercial path is component design-in, not a direct fab retrofit. Evaluation units and integration NRE can fund learning, but recurring economics require module shipments. A licensing path may eventually fit a clean China counterparty, yet it cannot depend on routing controlled technology or know-how through an intermediary. Customer concentration is unavoidable: the same platform owner that can provide access can also absorb the function.

## Physics and build path

An L- or pi-type network transforms a changing complex plasma impedance toward the RF source's target load. A motorized vacuum capacitor moves continuously but slowly. A solid-state bank selects among discrete capacitance or inductance states, so the design problem is to cover the required Smith-chart region with enough resolution while limiting conduction loss, switching transient energy, device stress, and parasitic coupling. The controller estimates the present load from calibrated RF measurements, chooses a safe transition sequence, and makes that transition at a permitted point in the pulse recipe. A table-based first product is more credible than unconstrained online optimization.

The laboratory path has five stages. First, characterize individual switch branches under representative RF voltage and current, including off-state capacitance, Q, heating, and fault energy. Second, assemble a low-power network and verify that commanded states reproduce the expected impedance map. Third, raise the system to 13.56 MHz and 5 kW on a programmable plasma-load emulator, measuring rematch time, reflected energy, insertion loss, harmonics, and thermal equilibrium. Fourth, run pulse recipes with deliberate load steps and compare against a motorized benchmark. Fifth, after signed access exists, repeat the test on a chamber and evaluate a declared process metric.

Chamber integration is broader than the match network. Electrostatic-chuck studies document the coupled electrical, thermal, dielectric, and plasma environment around wafer processing ([L06-004](https://www.jos.ac.cn/article/doi/10.1088/1674-4926/36/8/084004), [L06-005](https://pubs.aip.org/aip/jap/article-pdf/doi/10.1063/1.3006441/15032353/094902_1_online.pdf), [L06-006](http://www.jstage.jst.go.jp/article/pfr/2/0/2_0_044/_article), [L06-007](https://doi.org/10.1109/tsm.2023.3301024)). Those papers do not validate solid-state matching. They are reminders that a faster electrical subsystem can still fail commercially if it worsens wafer temperature uniformity, chuck behavior, discharge stability, or chamber qualification.

The hardest scale-up risks are honest. Semiconductor devices and package parasitics may destroy Q or voltage margin; state changes can inject spectral artifacts or produce a temporary dangerous mismatch; arc sensing and shutdown may be too slow; thermal cycling may shift calibration; and a useful impedance range may require so many devices that cost and loss erase the benefit. The 60 MHz family endpoint is a separate physics-and-packaging program, not a milestone that should be inferred from v1.

## Incumbents, bear case, and the explicit 10x test

The closest incumbent benchmark is Comet, while Advanced Energy, MKS, and other RF-platform owners possess the stronger strategic position: installed interfaces, generator knowledge, field service, process data, patents, and qualification relationships. China's Hengyunchang and Injet are moving up the RF-power stack. An incumbent can respond with a hybrid fast-trim branch, a limited solid-state option, tighter frequency control, or an acquisition. It does not need to reproduce the startup's entire vision to close the socket.

The strongest bear case is that motor speed is not the binding process constraint. Existing preset switching, frequency tuning, generator control, and recipe design may already keep reflected energy within an acceptable range. A 10-microsecond matcher could improve a beautiful oscilloscope trace without raising yield, throughput, uniformity, or uptime. Tool OEMs may refuse a standalone module because the match and generator must be co-qualified. Even technical success can therefore end as a small IP sale rather than a durable merchant platform.

The explicit 10x test has two layers. On the bench, pass requires closed-loop rematch in no more than 10 microseconds after a preregistered load step, at least 10,000 times faster than a measured 100-millisecond motorized baseline, while reducing integrated reflected energy by at least 10 times. It must hold across a preregistered impedance envelope, not one favorable point. Total RF insertion loss must remain at or below 2%, no switching event may cross the declared arc or overvoltage limit, and out-of-band energy must remain within the OEM-agreed mask. On the chamber, the startup must show at least a 10x reduction in pulse-to-pulse electrical settling error or a pre-agreed material process benefit. If the electrical advantage does not translate into a buyer-valued endpoint, the commercial 10x claim fails regardless of speed.

## Decisive experiment, budget, and pass/kill rules

The frozen first experiment is a 13.56 MHz, 5 kW switched-capacitor matcher tested against a motorized network, with a $250,000 budget. A planning allocation is $45,000 for high-voltage switching devices and passive components; $32,000 for RF fixtures, shielding, cooling, and enclosure; $38,000 for sensing, FPGA control, and isolation; $45,000 for a programmable load emulator and protection hardware; $30,000 for RF test-instrument access and calibration; $25,000 for independent safety and EMC work; $15,000 for accelerated switching and thermal-cycling fixtures; and $20,000 contingency. These are assumptions, not quotes.

Pass the technical thesis only if the module meets the complete bench 10x test, survives at least 10 million accelerated state transitions without parameter drift outside the preregistered band, and fails safely under open, short, mistimed-pulse, cooling-loss, and sensor-fault injections. Advance to a chamber evaluation only after the arc-energy, harmonic, and safe-state results pass independent review. The later product gate remains the frozen one-billion-switch-event target; the first experiment does not pretend to complete it.

Kill or sharply narrow the idea if insertion loss exceeds 2%; the required impedance coverage cannot be achieved without unsafe device stress; switching creates unacceptable harmonic or arc behavior; repeated calibration cannot hold across temperature; the reflected-energy benefit is below 10x; or a motorized/hybrid incumbent solution performs within 20% of the startup on the buyer's actual recipe. Commercially, kill the merchant-module thesis if no generator or tool vendor will sign a paid, endpoint-defined evaluation by end-2029. No such access, agreement, or order is claimed here.

## Bottom-up niche arithmetic

Use design wins and annual module flow, not a top-down semiconductor-equipment TAM. Assume one US platform program and one or two legally clean China programs reach production by 2034. At 40-150 modules per program per year, that is 80-450 annual modules. At an assumed production selling price of $25,000-$60,000 per module, annual hardware revenue at that stage is roughly $2 million-$27 million. Three evaluation and integration programs at $250,000-$750,000 each add $0.75 million-$2.25 million of nonrecurring revenue before volume production.

A five-year installed base of 300-1,500 modules, with calibration, spares, and software support equal to 6-12% of hardware revenue, could create a focused subsystem company. Gross margin is unknowable until switch losses, cooling, yield, warranty reserves, and channel share are measured. The upper case also assumes a platform owner does not demand most of the economics. These ranges support a high-end niche, not a billion-dollar claim. Expansion to more frequencies, powers, and plasma applications is upside earned after qualification. The frozen $3 million-$8 million v1 capital range is plausible only if paid evaluations offset part of the qualification program; it is not covered by the $250,000 experiment.

## US route

The US route is a co-development sale to one RF-generator or tool platform, with a chamber lab as validation partner. In 2026, freeze the 13.56 MHz/5 kW envelope, obtain incumbent benchmark hardware, complete freedom-to-operate and safety reviews, and secure only interviews and written test requirements. In 2027, run the decisive bench experiment. In 2028, require a paid evaluation with signed access, data rights, process endpoints, and responsibility for arc events. In 2029, deliver cross-recipe reliability evidence and a one-billion-transition test plan, then freeze an OEM-integrable module.

The launch trigger is a design-in agreement or funded qualification program, not general platform growth. The best route may be selling to an incumbent rather than competing with its entire platform. That lowers channel cost but increases customer concentration and bargaining risk. If no platform owner defines a paid endpoint by end-2029, the US route fails even if the prototype is fast.

## China route

The China route must be commercially and legally separate. Current category evidence supports AMEC and domestic RF-supply-chain activity, but two frozen named buyer examples have severe official restrictions. BIS's December 2024 action applies Entity List controls and a presumption-of-denial posture to named semiconductor-equipment organizations ([P3R2-F-01-S01](https://www.govinfo.gov/content/pkg/FR-2024-12-05/html/2024-28267.htm)). A later legal summary describes expansion of ownership-based controls and strict-liability exposure ([P3R2-F-01-S02](https://www.sidley.com/en/insights/newsupdates/2025/10/us-commerce-department-bureau-of-industry-and-security-adopts-50-percent-rule-for-export-controls)). Restricted-party, beneficial-ownership, end-use, technology-classification, and reexport screening must therefore occur before technical disclosure, shipment, evaluation, or license.

No offshore entity, reseller, localization label, or mature-node scope is treated as a safe harbor. The route proceeds only through counsel-cleared counterparties and independently lawful technology. The earliest commercial step is a paid evaluation with a clean domestic RF vendor or tool OEM, local service responsibility, agreed data segregation, and no transfer beyond the licensed evaluation scope. If counsel cannot approve the product, end user, ownership chain, and technical-data package, the China route is killed rather than routed around the constraint. Official self-reliance policy can increase demand for a domestic solution while decreasing demand for a foreign licensor; both possibilities must remain in the model.

## Safety, compliance, and quality

The bench and product combine kilowatt RF power, high RF voltage, stored reactive energy, fast switching, cooling, and a conductive enclosure. Required controls include interlocked covers, bleeder verification, grounded and shielded fixtures, arc and overcurrent detection, safe-state logic independent of the main controller, emergency power removal, cooling-flow and temperature trips, RF exposure surveys, guarded connectors, two-person high-power procedures, and fault-injection records. The module must fail to a documented benign state when sensing, timing, communications, or cooling is lost.

Qualification data must preserve component lots, firmware and table versions, calibration state, thermal history, waveform captures, fault logs, and raw forward/reflected measurements. Each release needs a declared impedance envelope and derating curve. Recipe data remains customer-confidential and segregated. Export-control classifications and restricted-party status are refresh items, not one-time certificates. No safety or compliance approval is inferred from a successful laboratory result.

## 2026-2029 plan, 2030 launch, and 2030-2034 window

**2026:** narrow v1, build switch-branch coupons, benchmark the motorized network, map patents, and obtain a written legal classification before any China engagement. **2027:** complete the $250,000 load-emulator experiment and publish a bounded performance and fault envelope. **2028:** undertake up to two paid evaluations only after counterparties sign access and data terms; one strong program is better than two informal demonstrations. **2029:** complete chamber endpoint testing, accelerated lifetime work, manufacturing design, and the one-billion-transition qualification plan. Require at least one funded design-in route.

**2030 launch:** release only the qualified 13.56 MHz module, integration kit, telemetry interface, and calibration service. Do not launch the full frequency family on the strength of v1. **2030-2034:** add power or frequency variants one at a time, tied to named platform programs. Refresh incumbent roadmaps, Comet specifications, RF-platform revenue, China localization programs, and trade-control status every six months. The company-level deadline remains end-2033: without an OEM design-in or a paid evaluation converting to a production order, stop the merchant-module program.

## Risk register and kill hierarchy

The first kill risk is physics at power: inadequate Q, voltage margin, impedance coverage, or thermal stability. Second is plasma integration: fast transitions cause arcs, spectrum problems, or no process benefit. Third is incumbent absorption: a platform owner ships a good-enough solid-state or hybrid function before qualification. Fourth is buyer structure: no OEM accepts a merchant module or paid evaluation. Fifth is concentration: one design-in captures the company without attractive margins. Sixth is China compliance: a useful counterpart or transaction cannot be cleared. Seventh is schedule: qualification extends beyond the 2030-2034 socket.

The hierarchy matters. A policy tailwind cannot rescue failed RF physics; a fast bench cannot rescue zero process value; and process value cannot rescue an illegal or unreachable transaction. At each stage, capital should be released only after the preceding kill condition is retired.

## Durable evidence versus refresh-sensitive evidence

The durable core is the peer-reviewed record: plasma matching remains a modeled and experimentally investigated control problem; dual-frequency and multifrequency networks are technically real; and tailored waveform work connects rapid RF behavior to advanced etch questions ([L06-001](https://pubs.aip.org/avs/jvb/article/42/2/022212/3277858/Modeling-and-control-of-L-type-network-impedance), [L06-002](https://pubs.aip.org/aip/jap/article/137/3/033301/3331468/Impedance-matching-assistance-based-on-frequency), [L06-003](https://www.mdpi.com/2079-9292/10/17/2074), [L01-012](https://pubs.aip.org/avs/jva/article/37/2/021303/247270/Experimental-demonstration-of-multifrequency), [L06-009](https://pubs.aip.org/aip/pop/article/31/3/033508/3279954/Voltage-waveform-tailoring-for-high-aspect-ratio)). The electrostatic-chuck literature is durable chamber-context evidence, but it does not prove a buyer or the matcher design.

Refresh-sensitive evidence includes Comet's current specification, platform revenues and product ramps, domestic supplier results, equipment-localization rates, policy implementation, buyer lists, restricted-party status, ownership rules, prices, and qualification schedules. Primary company and official records should be archived and rechecked before every gate. Trade reporting is corroboration, not a substitute for a buyer-defined evaluation. No signed access, purchase order, production award, or current legal clearance is claimed.

## Verdict

**Advance the $250,000 precompany experiment; do not yet finance a broad product family.** P3R2-F-01 deserves its top-ten position because it combines an active technical problem, a direct incumbent specification showing slow capacitor-based matching, a bench-measurable edge, and real RF-platform activity in both US and China. It remains a 59.8/100, medium-confidence idea because exact purchase demand is absent, incumbent absorption is plausible, the full frequency envelope is unproved, and the China route is materially narrowed by compliance.

The next decision is crisp: at 13.56 MHz and 5 kW, demonstrate no more than 10-microsecond rematch, at least 10x lower reflected energy, acceptable loss and spectral behavior, safe faults, and repeatable operation across the declared impedance envelope. Then obtain a paid, endpoint-defined OEM evaluation. If the electrical result does not translate into a buyer-valued chamber endpoint, if no platform owner funds qualification by end-2029, or if a lawful China counterparty cannot be cleared, kill the corresponding route rather than preserving the narrative.
