Timzhao0205/PhD_Career_Portfolio/02_Startup/06_Frontier_Idea_Research_2026-07/50_GEOGRAPHY/GEOGRAPHY_BRIEF.md

# Geography brief: United States and China

**Evidence cutoff:** 14 July 2026  
**Portfolio:** frozen P5 final 24  
**Use:** precompany validation from 2026-2029, a conditional 2030 launch, and trigger monitoring through 2034

## Decision frame

The portfolio contains **21 United States beachheads, 18 China beachheads, and 15 dual-market ideas**. The asymmetry is intentional. Six ideas are United States only: `P3R2-D-01`, `P5-USSCI2-S01`, `P3R2-E-14`, `P3R2-A-14`, `P3R2-E-04`, and `P3R2-F-06`. Three are China only: `P3R2-B-01`, `P3R2-F-12`, and `P3R2-G-01`. Every other idea has a separate route in both primary markets; “dual” does not mean one product, entity, data room, or qualification dossier can automatically serve both.

This is a route-to-validation brief, not a forecast of revenue or a claim that access has been secured. No signed pilot, purchase order, tender eligibility, laboratory access, or data right is assumed. Cross-border control and ownership statements are operating hypotheses that require refreshed specialist review before transactions; they are not legal conclusions.

The demand anchors are institutional rather than top-down market estimates. In the United States these include federal laboratories and competitive solicitations, equipment OEMs, power-project developers, industrial operators, hyperscalers, commissioning firms, and regulated infrastructure owners. In China they include ministry programs, public research institutes, industrial OEMs, eligible tendering fabricators, classification bodies, commercial datacenter operators, shipyards, and project integrators. Examples in the accepted ledger include the [U.S. fusion-program selections](https://www.energy.gov/articles/us-department-energy-announces-selectees-107-million-fusion-innovation-research-engine), a [Brookhaven hybrid MCP-PMT request for information](https://sam.gov/opp/c4efe4e23fad4659885b0591235e2714/view), [advanced-packaging X-ray procurement in Guangzhou](https://chinabidding.mofcom.gov.cn/bidDetail/bidding/bulletin/202602/ff8080819a82040b019c98b9dc8a140c.html), and a [HEPS vacuum-chamber tender](https://www.ccnta.cn/article/7832.html).

## United States operating model

The United States route is strongest where a company can enter through an open benchmark, paid evaluation, federal R&D subcontract, or OEM qualification before it must carry full system liability. Scientific hardware should begin with a laboratory or tube/magnet/quantum-system integrator and a narrow interface-controlled deliverable. The BNL dynode RFI, [NIST X-ray system acquisition](https://sam.gov/workspace/contract/opp/96effae327354fae8e9363b8b2a98541/view), [DOE quantum-center continuation](https://www.energy.gov/articles/energy-department-announces-625-million-advance-next-phase-national-quantum-information), and [FORGE geothermal R&D route](https://www.energy.gov/hgeo/geothermal/forge-rd) show distinct procurement paths; they do not prove that a startup will be selected.

For datacenter and industrial power hardware, the first buyer is more likely an OEM, rack/power-sidecar designer, cooling integrator, or commissioning specialist than the hyperscaler itself. Qualification must therefore be packaged as interface specifications, traceable test data, failure-mode evidence, and an installable reference design. The [Project Deschutes CDU specification](https://arpa-e.energy.gov/sites/default/files/2026-01/Day1_06b_Google_Kabbani.pdf) is useful as a buyer-generated performance boundary, while [IEC 62477-1](https://webstore.iec.ch/en/publication/28936) is a baseline safety reference for converter equipment. Product-specific certification plans still need confirmation with the actual integrator and test laboratory.

For grid and hydrogen ideas, project timing and bankability matter more than an impressive isolated prototype. The route runs through developer/OEM test programs, hardware-in-the-loop evidence, protection studies, and warranty-recognized data. The [Southern Spirit HVDC project](https://patternenergy.com/projects/southern-spirit-transmission/) provides a dated project anchor, and the [hydrogen-hub award record](https://www.energy.gov/articles/biden-harris-administration-announces-awards-22-billion-two-regional-clean-hydrogen-hubs) identifies prospective asset networks. Neither source guarantees a merchant sensing, controller, relay, or degradation-bench socket.

## China operating model

China is not a generic direct-sales extension. The credible routes are: sell to a qualified local OEM; license or jointly develop with a thermal, laser, semiconductor-equipment, ship-power, or vacuum-system integrator; or sell calibrated equipment and recurring verification to a China-registered fabricator that can bid. Direct pursuit of sensitive public infrastructure and direct hyperscaler selling are false routes where the P5 record says access is structurally weak.

Qualification is institution-specific. Datacenter thermal and power products need local system integration and evidence aligned with the evolving [GB 40879 datacenter-efficiency standard](https://std.samr.gov.cn/gb/search/gbDetailed?id=2E4DD4D8E2E84A4BE06397BE0A0AE354), [T/CIEP 0263-2025 liquid-cooling specification](https://www.ndls.org.cn/standard/detail/f4af7d31f9d7cfe71b0a742752250077), and the official [AI-energy action plan](https://www.nea.gov.cn/20260508/4dae97ca01d348e4871bb8654be34b3a/c.html). Marine power must enter through shipyard/integrator design and China Classification Society review; the accepted evidence includes the [2025 battery-powered-ship rules](https://www.ccs.org.cn/ccswz/articleDetail?id=202601060114611630&columnId=201900002000000398) and [pure-battery inspection rules](https://www.ccs.org.cn/ccswz/articleDetail?id=202503061077276480&columnId=202007070926126287). Industrial heat-pump metrology should align with the [national heat-pump action plan](https://www.gov.cn/zhengce/zhengceku/202504/P020250402477391648460.pdf) and [2026-2028 actual-load-efficiency program](https://www.miit.gov.cn/xwfb/xwfbh/bxwfbh/art/2026/art_4e9257192fe743ca84c33ffc78e94e0c.html).

Local data control is also a commercial issue: fab recipes, laser waveforms, datacenter power sequences, warranty logs, and facility acceptance records may remain on the customer site. The precompany product should be designed for on-premise analysis, exportable summary metrics, separated model-update packages, and customer-controlled raw data. The China moat cannot rest on a transferable recipe alone; calibration traceability, reference artifacts, sequence libraries, field service, and continuously updated qualification dossiers are safer starting points.

## Idea-by-idea primary-market route matrix

| Rank / idea | United States route | China route | Qualification, 2030 entry, and 2030-2034 trigger |
|---|---|---|---|
| **1 · `P3R2-D-02` REBCO tape metrology** | Tape vendors and fusion/accelerator magnet builders; enter as a neutral acceptance instrument, not a tape producer. | Tape vendors, magnet institutes, and integrators around the demonstrated HTS supply chain; [ASIPP’s 35.1 T result](https://english.cas.cn/newsroom/cas_media/202509/t20250929_1059028.shtml) is an application anchor. | Blind-correlate reel scans with transport critical-current and delamination tests. Launch only with a repeatable cross-vendor dossier. Trigger: serial magnet/tape qualification; kill if vendors’ in-house QC is accepted as sufficient. |
| **2 · `P3R2-C-22` electrolyzer degradation bench** | Electrolyzer OEMs, hub developers, test labs, and warranty/bankability teams. | Electrolyzer OEMs, energy-project integrators, and independent test institutes; tender activity establishes systems demand, not a bench order. | Run accelerated ripple/OCV campaigns on commercial short stacks and require paid campaigns. The technical basis includes documented [ripple-linked degradation](https://pmc.ncbi.nlm.nih.gov/articles/PMC8877858/). Trigger: warranty disputes and intermittent operation; kill by end-2033 if neither market pays. |
| **3 · `P3R2-D-01` HTS quench protection** | Fusion companies, national laboratories, university magnet labs, and magnet builders; co-wound sensing plus qualified energy extraction is the deliverable. | **False beachhead:** no selection-grade China buyer/access and subsystem-qualification path. Do not infer a market from magnet activity alone. | Controlled quenches must demonstrate warning time and false-trigger performance, followed by magnet-builder qualification. Trigger: pilot magnet builds; kill if no-insulation designs remove the need or an open design becomes standard. |
| **4 · `P3R2-F-01` microsecond plasma matcher** | RF generator and chamber OEM design-in, with process-tool labs as validation sites; avoid unsupported direct-fab retrofit assumptions. | Domestic RF-power and etch-tool OEMs are the route; filings from [Injet](https://news.qq.com/rain/a/20250425A0341L00) and [AMEC](https://www.stcn.com/article/detail/1673114.html) show a local equipment base. | Demonstrate sub-10-microsecond rematch, reflected-power reduction, and lifetime. Trigger: pulsed/tailored waveforms; kill if incumbent generators integrate equivalent matching before a merchant design win. |
| **5 · `P3R2-C-01` 800-VDC rack protection** | OCP ecosystem suppliers, rack/power-sidecar OEMs, and lab-qualified module integrators. | Local power OEMs and datacenter integrators; the [Delta-Alibaba power collaboration](https://www.delta-china.com.cn/zh-cn/news/19212) is an integration-route signal. | First falsify the merchant socket through paid evaluation or written interface requirements. Then qualify interruption, precharge, insulation monitoring, hot swap, and thermal limits. Refresh component controls and certification scope in 2029. |
| **6 · `P5-USSCI2-S01` diamond transmission dynode** | BNL detector R&D, tube makers, and qualified thin-film/membrane processors. The public RFI is the direct demand anchor. | **False beachhead:** no China procurement or qualified integration route in P5. Base ePIC procurement is also explicitly not a beachhead. | Require repeatable transmission yield, bake/charge stability, timing, and seal-compatible cartridge integration. Launch only for a funded post-freeze detector or paid tube-maker program; kill at end-2029 without one. |
| **7 · `P3R2-E-14` multi-terminal DC relay/HIL platform** | HVDC developers, converter OEMs, protection labs, and MVDC datacenter demonstrators. | **False beachhead:** observed state-grid awards show demand but not an accessible vendor-neutral relay socket; do not count them. | Publish an open four-terminal HIL benchmark and sub-millisecond relay results. Trigger: genuinely multi-terminal projects; kill/defer if projects remain point-to-point or OEMs refuse third-party protection through 2034. |
| **8 · `P5R2-CN-01` computed-laminography retrofit** | Packaging failure-analysis labs, inspection-system service partners, and public metrology labs; position as a retrofit to existing 2D X-ray cabinets. | Substrate/packaging plants and inspection integrators; exact anchors include [Guangzhou procurement](https://chinabidding.mofcom.gov.cn/bidDetail/bidding/bulletin/202602/ff8080819a82040b019c98b9dc8a140c.html), [Wuxi procurement](https://en.chinabidding.mofcom.gov.cn/bidDetail/bidding/bulletin/202603/ff8080819a82040b019ce651241065d5.html), and [JCET’s Lingang project](https://www.sse.com.cn/disclosure/listedinfo/announcement/c/new/2026-06-25/600584_20260625_27YK.pdf). | Blind seeded-defect trials against sectioning or trusted CT must prove detection and calibration. Enter in the post-install yield-learning cycle, not as a claim to win the original cabinet order. |
| **9 · `P3R2-A-14` 300°C instrumentation** | DOE geothermal programs, tool OEMs, downhole service companies, and high-temperature test facilities; [SUPERHOT](https://arpa-e.energy.gov/programs-and-initiatives/view-all-programs/superhot) and FORGE are precompany channels. | **False beachhead:** no P5 buyer/qualification route. | Independently witness 1,000-hour operation, drift, and package cycling before an OEM field trial. Trigger: superhot wells and harsh turbine/tool deployments; otherwise the product remains program-funded and narrow. |
| **10 · `P3R2-C-13` precision GaN laser driver** | Commercial laser OEM evaluation; any defense-adjacent line must remain operationally and technically separated. | Commercial industrial-laser OEMs only, through a locally supported module and customer-site testing. No defense-adjacent China use is part of the thesis. | A paid make-versus-buy evaluation precedes hardware scale-up. Qualify pulse fidelity, protection, thermal behavior, and lifetime. Trigger: OEM willingness to outsource; kill the standalone module if both sides remain vertically integrated. |
| **11 · `P3R2-C-08` shock-tolerant PCHE** | sCO2, geothermal, industrial-heat, and thermal-storage developers plus qualified diffusion-bonding fabricators. | Steel/waste-heat, heat-pump, hydrogen-precooling, and sCO2 integrators; nuclear-qualified work is not a cross-border route. | Require a buyer-identified incumbent limit, coupon/bond qualification, thermal-cycling evidence, and buyer cost sharing. Trigger: merchant 10-MW-class orders by end-2033; schedule slip or institute verticalization kills the wedge. |
| **12 · `P3R2-B-01` subatmospheric two-phase cooling** | **False beachhead:** the selected thesis is China-specific and has no validated United States merchant wedge. | License or jointly develop with a Chinese thermal vendor or ODM; direct hyperscaler sales are explicitly unrealistic. | First obtain a paid leak-direction/architecture requirement from the integrator, then prove negative-pressure control and serviceability. Trigger: >2 kW/chip rack qualification; kill if local incumbents internalize the architecture. |
| **13 · `P3R2-E-04` cryogenic interconnect loader** | Quantum-system builders, dilution-refrigerator suppliers, national labs, and cryogenic-control integrators; [Fermilab’s control-platform partnership](https://news.fnal.gov/2025/11/energy-department-announces-partnership-with-fermilab-and-qblox-to-manufacture-foundational-quantum-control-platform-for-u-s-research-a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) shows the integrator pattern. | **False beachhead:** no P5 buyer, data-access, or qualification route. | Secure a post-2029 external-I/O architecture slot before building. Qualify heat load, channel density, crosstalk, cycling, and 4 K electronics. Kill if on-chip multiplexing or optical links erase the loader socket. |
| **14 · `P5R2-CN-03` industrial heat-pump M&V island** | **Not countable in this round.** A high-temperature field-validation project is useful technical context, but no current US merchant buyer for this island was established; do not use a future paid engagement to backfill the beachhead. | Industrial park/project owners, heat-pump OEMs, test institutes, and commissioning contractors. A [170°C steam heat-pump acceptance](https://giec.cas.cn/kxyj2016/kyjz2016/202411/t20241127_7447072.html) shows third-party measured parameters are decision-relevant. | Prove traceable heat balance and detection of blinded 5% degradation on a partner loop. Trigger: 2030 industrialization and actual-load evaluation; no facility access is assumed. |
| **15 · `P3R2-F-02` magnet drive-and-dump skid** | Fusion firms, national labs, accelerator/magnet builders, and research-magnet integrators. | Sell to eligible magnet/power-system fabricators and institutes; exact power-system tenders exist at [ASIPP](https://ipp.cas.cn/ztbxx/zhbxx/202508/P020250822374368143234.pdf). | Validate stability and clean extraction on an HTS coil, then qualify interfaces and fault cases with a builder. Trigger: serial magnet systems; research magnets hedge fusion delay beyond 2034. |
| **16 · `P3R2-C-04` PFAS-free pumped two-phase loop** | Hyperscaler/OEM thermal labs, CDU and cold-plate integrators, and fluid suppliers. The [AIM Act HFC guidance](https://www.epa.gov/climate-hfcs-reduction/frequent-questions-phasedown-hydrofluorocarbons) is a refresh point, not a product approval. | Thermal OEMs and commercial datacenter integrators, with localized hardware and qualification against current efficiency/liquid-cooling requirements. | Run 1,000-hour sealed-loop tests with at least two candidate fluids. Trigger: qualified non-PFAS fluid availability; kill in 2031 if no fluid reaches datacenter-scale qualification. No “100% liquid-cooling mandate” is assumed. |
| **17 · `P3R2-F-12` class-certified vessel DC stack** | **False beachhead:** no United States vessel buyer/class route supports this selected configuration. | Shipyards, non-bundled integrators, battery-swap operators, and China Classification Society are the route; the [Jining 6006 vessel](https://www.catl.com/en/news/6592.html) is an operating-system anchor. | Before a build, obtain a standalone RFQ and written classification boundary for string protection, insulation monitoring, and pack interface. Kill if the battery supplier bundles the full stack or class offers no merchant boundary. |
| **18 · `P3R2-G-01` UHV conditioning/certification** | **False beachhead:** the product is deliberately China supply-chain specific and no United States tender cadence was validated. | Sell stations and recurring calibration to China-registered chamber fabricators eligible for HEPS/CEPC-class work, not directly as an ineligible tender bidder. | Demonstrate endpoint-controlled bakeout, rate-of-rise agreement, and cycle-time reduction. Before promotion require two additional chamber-class tenders beyond the anchor; kill/defer on facility schedule slip or local absorption of the full bench. |
| **19 · `P3R2-A-10` IEDF metrology/bias retrofit** | RF-power OEMs, chamber OEMs, and process-development labs; customer-site recipe data should remain segregated. | Domestic etch-tool and RF-power OEMs, using on-premise calibration and limited exported metrics. | Hold programmed ion-energy peaks through pressure/chemistry drift and correlate with etch profile. Trigger: tailored-waveform adoption; kill/narrow if OEM interfaces stay closed or generator vendors integrate good-enough inference by 2030. |
| **20 · `P3R2-G-03` DC commissioning island** | Commercial datacenter operators, electrical integrators, commissioning firms, and DC-shelf vendors; sell a method/dossier layer, not another in-path converter. | Licensed commercial operator/integrator route only. State-grid-facing work is a **false beachhead**; localize sequence libraries and on-site data handling. | The binding 2029 gate is a paid commissioning or frame-agreement socket. Qualify bus impedance, insulation, inrush, hot swap, and the signed customer dossier format. Vendor self-certification is the kill risk. |
| **21 · `P3R2-D-12` EHD two-phase cold plate** | Cooling OEM labs, hyperscaler thermal teams, and DOE-backed test environments; DOE’s [COOLERCHIPS awards](https://www.energy.gov/articles/doe-announces-40-million-more-efficient-cooling-data-centers) show a validation channel. | Datacenter thermal integrators and component OEMs, aligned with current liquid-cooling and efficiency requirements. | Demonstrate flow modulation, 1,000-hour electrode stability, and superiority to mechanical pumping. The fluid must be dielectric, non-PFAS, and low-GWP; parity or no qualifying fluid kills the idea. |
| **22 · `P3R2-F-23` electrolyzer protective-envelope controller** | Electrolyzer OEMs, plant owners, hub developers, warranty teams, and project finance reviewers. | Electrolyzer OEMs, energy-project integrators, and plant owners; local raw logs may need to remain on site. | Before hardware, secure three-party agreement on command authority, warranty recognition, and data rights. Trigger: financed intermittent plants; kill/retarget if hydrogen project decisions remain depressed or warranty parties reject external logs. |
| **23 · `P3R2-F-06` wideband DC sensing** | HVDC developers, converter-station OEMs, electrolyzer rectifier integrators, and magnet-power builders. Southern Spirit is the timing anchor; FERC/NERC’s [protection-setting rule](https://www.federalregister.gov/documents/2025/07/29/2025-14304/reliability-standards-for-frequency-and-voltage-protection-settings-and-ride-through-for) is a compliance refresh point. | **False beachhead:** observed domestic grid awards do not establish an unbundled merchant sensor socket. | Obtain an unbundled evaluation interface before a high-current prototype. Trigger: wideband fault/protection requirements; kill/narrow if converter OEMs retain vertically bundled sensors. |
| **24 · `P3R2-F-03` turbo-generator electrical cartridge** | Geothermal, waste-heat, and sCO2 developers plus turbine/ORC OEMs; [Fervo project financing](https://fervoenergy.com/fervo-energy-secures-421-million-in-non-recourse-project-financing-for-cape-station/) and the [STEP pilot](https://www.swri.org/newsroom/press-releases/step-demo-pilot-plant-achieves-full-operational-conditions-phase-1-of-testing) are timing anchors. | Commercial waste-heat/sCO2 project integrators and turbomachinery OEMs; the [Guizhou commercial unit](https://news.cctv.cn/2025/12/21/ARTIOIKxHHqUSt3APo8IVLjd251221.shtml) anchors a real installation, not an available cartridge socket. | First obtain an OEM RFQ/interface and evidence that in-house generators are a bottleneck. Launch only with a merchant socket; kill if integrators keep the electrical train internal. |

## 2026-2034 engagement and launch sequence

**Second half 2026:** build institution maps by idea, identify the actual qualification owner, and request only non-confidential interface and acceptance information. Track open solicitations, public test plans, standards revisions, and named commissioning providers. For each dual-market idea, maintain separate U.S. and China buyer hypotheses, bills of material, raw-data rules, and claims matrices.

**2027:** run the bounded technical tests already frozen in P5. The low-cost commercial-gate ideas should lead with RFQs, paid evaluations, make-versus-buy interviews, or dossier requirements. Scientific and industrial hardware should use university, national-lab, OEM, rental-equipment, or integrator benches only after written test scope and data ownership are established. A test result is not procurement engagement unless a buyer or integrator participates in a defined evaluation.

**2028:** convert surviving prototypes into qualification artifacts: calibration chains, environmental and lifetime data, fault trees, interface-control documents, service procedures, and customer-specific acceptance templates. In China, verify local tender eligibility and decide whether the route is equipment sale, license, joint development, or recurring calibration. In the United States, identify whether the buyer is a federal prime/subcontract route, an OEM design-in, a project developer, or an independent commissioning firm.

**2029 hard gates:** eleven ideas already have a credible procurement-engagement path in P5, but none may be treated as secured. Require documentary evidence appropriate to the idea: paid evaluation, funded qualification task, buyer-approved interface, class boundary, frame-agreement pathway, or named project inclusion. Re-run incumbent, schedule, standards, ownership, export-control, and component-availability checks. Kill or narrow any false merchant socket rather than carrying it into the 2030 portfolio.

**2030 launch:** launch only the surviving narrow product and only in the market where qualification is complete. A dual-market label does not require simultaneous launch. Serviceable early configurations are calibration equipment, test benches, retrofit kits, qualified modules, and documented subsystems—not full plants, fabs, vessels, grids, or datacenters.

**2030-2034:** monitor the triggers recorded in the matrix: serial HTS magnet builds; post-freeze detector funding; multi-terminal DC projects; advanced-packaging yield learning; industrial heat-pump acceptance; qualified non-PFAS fluids; marine class boundaries; recurring chamber tenders; paid third-party DC commissioning; financed hydrogen plants; and merchant sCO2/geothermal OEM sockets. A slip is not automatically failure, but repeated absence of the named buyer action is.

## Optional secondary routes supported by the selection

Secondary treatment is deliberately compact and follows only the frozen `secondary_markets` fields.

- **Japan:** optional follow-on for REBCO metrology and magnet power systems, electrolyzer testing/controllers, laser drivers, cooling loops, marine DC stacks, UHV conditioning, plasma metrology, DC commissioning, and turbo-generator cartridges. The accepted record includes a [Furukawa–fusion magnet partnership](https://www.furukawaelectric.com/en/release/2023/kenkai_20230112.html), but no idea should be promoted without a Japan-specific buyer and qualification owner.
- **South Korea:** optional follow-on for REBCO/magnet systems, electrolyzer benches, plasma matching/metrology, cooling, marine power, UHV conditioning, DC commissioning/sensing, and turbo-generator cartridges. A [KEPCO superconducting-cable operating route](https://www.electimes.com/news/articleView.html?idxno=212735) supports adjacency, not a procurement claim for this portfolio.
- **Taiwan:** optional follow-on only for subatmospheric/pumped/EHD cooling, plasma metrology, and DC commissioning. The route should be through the relevant ODM, semiconductor-tool, thermal, or power-integration supply chain; no direct operator access is assumed.

## Refresh-sensitive risks

1. **Public-program and project dates:** re-check fusion, detector, HVDC, geothermal, heat-pump, hydrogen, CEPC/HEPS, advanced-packaging, and sCO2 schedules at least quarterly from 2028.
2. **Standards and acceptance ownership:** refresh IEC, GB, liquid-cooling, ship-class, environmental-fluid, and grid-protection requirements before design freeze; determine which document is mandatory, contractual, or merely informative for the named buyer.
3. **Incumbent integration:** repeat make-versus-buy work for plasma matching, laser drivers, PCHEs, cooling, DC protection, wideband sensing, and turbo-generator cartridges. The merchant socket can disappear faster than the physics changes.
4. **Data and site access:** obtain written scope for fab recipes, detector interfaces, magnet faults, heat balances, warranty logs, and commissioning records. Until then, all proposed partner tests remain uncommitted.
5. **Cross-border separation:** re-screen ownership, end use, components, technical-data movement, and customer restrictions before every China/U.S. transfer. Commercial laser, semiconductor, grid, and ship-power lines need especially conservative separation.
6. **False beachheads:** do not silently convert adjacent activity into market entry. U.S. activity does not validate the three China-only ideas; China projects do not validate the six U.S.-only ideas; state-grid awards, base-ePIC procurement, direct Chinese hyperscaler sales, and ineligible direct big-science tendering remain explicitly excluded routes.
