Timzhao0205/PhD_Career_Portfolio/03_Investments_and_Finance/01_Market_Learning_Lab_2026-07/01_CURRICULUM/_about.md

# 01_CURRICULUM

The study track. `LEARNING_ROADMAP.md` = staged plan with deliverables.
`RESOURCES.md` = vetted reading/data list. `AI_PLAYBOOK.md` = how to use Claude/ChatGPT
here without getting burned by hallucinated numbers.
