Timzhao0205/PhD_Career_Portfolio/03_Investments_and_Finance/01_Market_Learning_Lab_2026-07/05_STATE/_about.md

# 05_STATE

Session state. Append one line to `PROGRESS_LOG.md` per work session
([ISO date] stage= files_touched= predictions_open=). Park unresolved research
questions in `OPEN_QUESTIONS.md` instead of chasing them mid-session.
