Timzhao0205/PhD_Career_Portfolio/03_Investments_and_Finance/01_Market_Learning_Lab_2026-07/05_STATE/OPEN_QUESTIONS.md

# OPEN_QUESTIONS

- Q1: Exact origin of the "70B RMB computing this year / 200B next year" claim — which
  outlet/analyst first published it, and what scope (chips only? servers? ecosystem)?
- Q2: Which supply-chain names disclose Huawei-linked revenue in their OWN filings
  (customer concentration tables, 互动易 replies)? Needed to upgrade tier C→B→A.
- Q3: Huawei in-house HBM on Ascend 950PR — who supplies what (CXMT? in-house fab?),
  and what does that do to prior HBM-supplier theses?
- Q4: SMIC advanced-node capacity allocated to Ascend in 2026 — any load-bearing number
  from Tier ≤2 sources, or is everything estimate-grade?
