Timzhao0205/PhD_Career_Portfolio/03_Investments_and_Finance/01_Market_Learning_Lab_2026-07/90_SOURCES/_about.md

# 90_SOURCES

`SOURCE_STANDARDS.md` = binding tier definitions (finance flavor).
`sources.json` = ledger; cite as [S###] everywhere. Seeded S001-S016 on 2026-07-05.
