Timzhao0205/PhD_Career_Portfolio/01_PhD_Research/09_PAP06_Career_Portfolio_Synthesis_2026-07/pilot/B12_lit_search/attempt-1/PAPER_LEDGER.csv

# PILOT SAMPLE — NOT FINAL — B12_lit_search PILOT attempt-1 — PAPER_LEDGER.csv (8 rows | 2 per topic stream)
paper_id | doi | title | authors | year | venue | publisher | publication_type | peer_review_status | publisher_url | topic_stream | relevance | evidence_status | access_status | correction_status | retraction_status | notes
P0001 | 10.1088/1741-4326/ac8aad | Long term operation of the radiation-hard Hall probes system and the path toward a high performance hybrid magnetic field sensor | A. Quercia; A. Pironti; I. Bolshakova; R. Holyaka; I. Duran; A. Murari; JET Contributors | 2022 | Nuclear Fusion, vol. 62, no. 10, art. 106032 | IOP Publishing (on behalf of IAEA) | journal_article | verified | https://iopscience.iop.org/article/10.1088/1741-4326/ac8aad | hybrid_diagnostics | Reports long-term radiation-hard Hall-probe operation and a proposed Hall+coil hybrid sensor architecture; topically relevant to B10's hybrid-diagnostic framing (context only, no B10 inference adopted) | accepted_core | publisher landing page opened directly (open access) | none found — no correction notice on IOPscience landing page at access time | none found — no retraction/expression-of-concern banner on landing page at access time | Peer review verified via IOP Publishing Nuclear Fusion standard editorial process (received/revised/accepted dates shown on landing page); JET Contributors co-authorship consistent with a JET collaboration research article. Accessed 2026-07-28.
P0002 | 10.1088/1361-6668/ae26d7 | Physics-guided quench detection framework for HTS coils based on augmentation of artificial quench data: a comprehensive benchmarking investigation on 75 different machine learning and dimensionality reduction techniques | Yahao Wu; Wenjuan Song; Mohammad Yazdani-Asrami | 2025 | Superconductor Science and Technology, vol. 38, no. 12, art. 125023 | IOP Publishing Ltd | journal_article | verified | https://iopscience.iop.org/article/10.1088/1361-6668/ae26d7 | hts_quench_current | Machine-learning-based quench-detection benchmarking for HTS coils; relevant background for the hts_quench_current stream (context only) | accepted_core | publisher landing page opened directly (open access) | none found — no correction notice visible | none found — no retraction/expression-of-concern banner visible | Landing page states single-anonymous peer review with one revision. Accessed 2026-07-28.
P0003 | 10.1088/1741-4326/adb599 | Sensor fusion and magnetic drift estimation in magnetic measurements using Kalman filter for long-duration plasma operations | Jaewook Kim; Jayhyun Kim; Y.-c. Ghim; Jun-Gyo Bak | 2025 | Nuclear Fusion, vol. 65, no. 4, art. 046008 | IOP Publishing Ltd on behalf of the IAEA | journal_article | verified | https://iopscience.iop.org/article/10.1088/1741-4326/adb599 | hybrid_diagnostics | Kalman-filter based Hall+coil sensor fusion and drift estimation for long-duration plasma operations; directly topical to hybrid_diagnostics bandwidth/drift-fusion questions framed (not adopted) from B10 | accepted_core | publisher landing page opened directly (open access) | none found | none found | Landing page lists received 24 Oct 2024, revised 13 Jan 2025, accepted 13 Feb 2025 — standard Nuclear Fusion peer-review timeline. Accessed 2026-07-28.
P0004 | 10.1088/1361-6587/ae6c59 | Antimony Hall sensors with W-Ti diffusion barriers for long-pulse operations in ITER and DEMO | I. Duran; S. Entler; M. Vilemova; M. Ivanek; P. Sladek; J. Reboun; P. Turjanica; M. Simonovsky; L. Stepan; O. Bares; Y. Ma | 2026 | Plasma Physics and Controlled Fusion, vol. 68, no. 6 (ECPD 2025 themed issue) | IOP Publishing | journal_article | verified | https://iopscience.iop.org/article/10.1088/1361-6587/ae6c59 | hall_metrology | Hall-sensor material/diffusion-barrier engineering for long-pulse radiation environments; relevant to hall_metrology radiation-effects/traceability sub-topics (context only) | accepted_core | publisher landing page opened directly (open access) | none found | none found | Published as a regular peer-reviewed journal paper (single-anonymous review, 1 revision, per landing page) within a themed issue tied to the ECPD 2025 conference; this is a journal article, not conference proceedings — classified journal_article accordingly. Accessed 2026-07-28.
P0005 | 10.3390/mi14112045 | Power Electronics Revolutionized: A Comprehensive Analysis of Emerging Wide and Ultrawide Bandgap Devices | S. M. Sajjad Hossain Rafin; Roni Ahmed; Md Asadul Haque; Md Kamal Hossain; Md Asikul Haque; Osama A. Mohammed | 2023 | Micromachines, vol. 14, issue 11, art. 2045 | MDPI | review_article | verified | https://doi.org/10.3390/mi14112045 (resolves to https://www.mdpi.com/2072-666X/14/11/2045) | power_conversion | Comprehensive review of WBG (SiC/GaN/ultrawide-bandgap) power device technology; directly topical to power_conversion stream (context only) | accepted_core | verified via PubMed Central open-access mirror PMC10673564; direct mdpi.com publisher page returned HTTP 403 on repeated WebFetch attempts this session — noted as a limitation, not concealed | none found — no correction notice visible on PMC record | none found — no retraction/expression-of-concern banner visible on PMC record | Micromachines is an MDPI peer-reviewed journal (named editors, standard review process); PMC record shows matching DOI/journal/publisher under CC-BY open-access license. mdpi.com direct access blocked by HTTP 403 for this WebFetch tool/session. Accessed 2026-07-28.
P0006 | 10.3390/mi12010065 | Review on Driving Circuits for Wide-Bandgap Semiconductor Switching Devices for Mid- to High-Power Applications | Chao-Tsung Ma; Zhen-Huang Gu | 2021 | Micromachines, vol. 12, issue 1, art. 65 | MDPI | review_article | verified | https://doi.org/10.3390/mi12010065 (resolves to https://www.mdpi.com/2072-666X/12/1/65) | power_conversion | Review of gate-drive circuit techniques for SiC/GaN WBG switching devices; directly topical to power_conversion stream (context only) | accepted_core | verified via PubMed Central open-access mirror PMC7826992; direct mdpi.com publisher page returned HTTP 403 on repeated WebFetch attempts this session — noted as a limitation, not concealed | none found | none found | Same access-limitation pattern as P0005 (mdpi.com blocked, PMC mirror used); PMC record matches DOI/journal/publisher. Accessed 2026-07-28.
P0007 | 10.1088/0953-2048/29/4/045007 | Self-protection mechanisms in no-insulation (RE)Ba2Cu3Ox high temperature superconductor pancake coils | Y. Wang; Wan Kan Chan; Justin Schwartz | 2016 | Superconductor Science and Technology, vol. 29, no. 4, art. 045007 | IOP Publishing Ltd | journal_article | verified | https://iopscience.iop.org/article/10.1088/0953-2048/29/4/045007 | hts_quench_current | Foundational/seminal study of no-insulation HTS coil self-protection and current redistribution during quench; seminal reference for hts_quench_current stream | accepted_core | publisher landing page opened directly | none found | none found | Landing page states single-anonymous review with 1 revision. Provides a seminal (2016) counterweight to the 2025 SST paper (P0002), matching the full-run diversity goal of pairing seminal and recent work, applied here at pilot scale. Accessed 2026-07-28.
P0008 | 10.5194/jsss-9-391-2020 | Traceably calibrated scanning Hall probe microscopy at room temperature | Manuela Gerken; Aurelie Solignac; Davood Momeni Pakdehi; Alessandra Manzin; Thomas Weimann; Klaus Pierz; Sibylle Sievers; Hans Werner Schumacher | 2020 | Journal of Sensors and Sensor Systems (JSSS), vol. 9, issue 2, pp. 391-399 | Copernicus Publications | journal_article | verified | https://jsss.copernicus.org/articles/9/391/2020/ | hall_metrology | Traceable Hall-probe calibration methodology and uncertainty budget (sensitivity, offset, temperature dependence, noise); directly topical to hall_metrology traceability/uncertainty sub-topics (context only, not adopted from B10) | accepted_core | publisher landing page opened directly (open access) | none found | none found | Article explicitly labeled 'Regular research article' with a published 'Review statement': edited by Michael Kraft, reviewed by two anonymous referees — direct page-level evidence of peer review beyond DOI/brand alone. Accessed 2026-07-28.
