Timzhao0205/PhD_Career_Portfolio/01_PhD_Research/09_PAP06_Career_Portfolio_Synthesis_2026-07/pilot/B30_skills/attempt-1/SKILLS.csv

# PILOT SAMPLE — NOT FINAL — B30_skills PILOT attempt-1. Exactly FIVE skills spanning sensing and power domains (S1/S2 clearly sensing-side; S3/S4 clearly power-side; S5 shared). current_level vocabulary is exactly: current_demonstrated / literature_backed_near_transfer / missing / collaborator_or_vendor. Grounding rule: current skill levels rest ONLY on B10's demonstrated ledger (PHD_FACTS.json C01-C50) as corrected by B20's five founder-fit corrections (ALIGNMENT.md §9) and B25's sixth (POWER_SKILLS.md §3.6); literature prevalence is NEVER proof the user has a skill. Cxx = B10 claims; EVxx/Pxxxx/G-M-BT = B15 rows/papers/gaps/bridge tests; PB-x = B25 bridge ladder; FT-x = B10-cited corpus falsification tests; W1/W2 = B25 POWER.md §9 wedges; BR-A/BR-B = this pilot's BRIDGES.json. All time/cost figures are EST order-of-magnitude planning labels carried from cited records | not quotes.
skill | category | current_level | evidence | target_level | needed_for | acquisition_path | validation_artifact | time | cost | priority | owner
Hall readout-chain design and EMI-disciplined weak-signal bench measurement (current-spinning demodulation, instrumentation-amp chain design, bench DAQ, analysis scripting) | sensing | current_demonstrated | B10 C03 (686 mV raw offset collapsed to <=5 mV, >=130x suppression — on a resistor-ring EMULATOR, not the real die); C13 (bench-verified boards, firmware, analysis scripts, DMM-confirmed as-builts); C01 (in-plasma campaign execution, qualitative/voltage-domain only). Honest bounds: the ~109x anomaly (C04) is OPEN and by the project's own rule blocks all calibration work; C15 flags the 'absolute calibration' language in SPECS.md as aspirational, not achieved | current_demonstrated (extended scope: same discipline exercised under converter switching EMI via BR-B, and multi-channel synchronization — the C14 three-board vector-probe architecture is proposed-only today) | Opt2 Elements 1-2; P3R2-D-02 (core Hall-array sensing head); P3R2-A-10 (EMI-robust readout leg); BR-A Phase 1 and BR-B execution; W2 measurement-chain lane; G5 PhD gate context (C38) | Maintain and extend, no new training: (1) close C04 root-cause on the bench (PhD-critical, blocks S2); (2) exercise the discipline under switching EMI by executing BR-B; (3) multi-channel extension rides the PhD's own project-03 plan (C14), not a separate acquisition | C04 root-cause closure note in the lab notebook (NOTES.md-class dated entry); BR-B raw dataset with zero-current pickup-floor runs; the three-board injected delta-V gain/polarity/linearity/phase release test that C04's own checklist names (C04 refinement) | C04 closure: honestly not estimable until root-caused (open anomaly); BR-B exercise 3-6 bench-weeks EST (B25 PB-1) | $0 beyond the existing bench for C04 work; BR-B costs are carried on BR-B's own line ($8-25K EST) | 1 | founder
Traceable absolute calibration with GUM/Monte-Carlo uncertainty budgets and drift characterization (WP-C class: coil-constant triangulation, bipolar DC calibration, Allan-variance drift) | sensing | literature_backed_near_transfer | NOT demonstrated: B10 C06 is proposed-only; C15 records that no calibration run, coefficient, or report exists anywhere; no calibration of the real device has ever been attempted. Transfer path (this is what 'near transfer' means here, not possession): B15 EV01/P0008 supply the corpus's single traceable-budget method template; C06 supplies a fully specified corpus plan gated on C04; the adjacent bench base (C03/C13) IS demonstrated. Literature prevalence of calibration methodology is not proof of this user's skill — the level claims only that the documented path from the demonstrated base is short | current_demonstrated | Opt2 Element 1 (the credential every B25 wedge bets on — POWER_SKILLS §5); P3R2-D-02's decisive calibrated-Ic leg; W1 family (G-03 dossiers, C-05 method authority, D-09 NIST-traceability core, F-06 qualification layer); BR-B dossier phase; G5 PhD gate ('real-die absolute calibration achieved') | Execute WP-C after C04 closes (record EST ~19-29 bench-days to a submittable Tier-1 package, zero cleanroom steps — C06 refinement); first locate the deployed 2025 module (C45 gate I-4); then generalize the budget discipline to a current measurand via BR-B's PB-2-class dossier phase | WP-C Tier-1 calibration report with full GUM/Monte-Carlo budget and Allan drift record; BR-B acceptance dossier complete enough that a third party could re-execute the protocol (PB-2 success gate) | ~19-29 bench-days record EST (C06) once C04 closes, plus 2-3 bench-weeks EST for the BR-B dossier phase (B25 PB-2); calendar start gated by C04 and C45 | WP-C bench field-source build per the corpus plan (C06; no cleanroom); BR-B dossier increment $3-10K EST (B25 PB-2) | 1 | founder
Bench-scale WBG power-electronics test-bed operation and safe HV bench practice (double-pulse and continuous-PWM operation of SiC/GaN evaluation cells, interlocks, capacitor-discharge discipline, staged bus escalation) | power | missing | B10's demonstrated ledger contains no converter, gate-drive, magnetics, HV, or protection entry of any kind (B25 POWER_SKILLS §1 finding across all 31 rows); B25 PB-1's safety note states safe practice at elevated DC bus is itself a competence NOT evidenced in B10; B25 §3.6 explicitly refuses the startup corpus's contrary founder-profile assertions ('high-power-density power electronics') as unverified against ground truth; B20 correction 1 (no power-electronics in the ledger) applies | current_demonstrated at bench/low-voltage scale ONLY (48-100 V; 400 V-class only under qualified supervision) — explicitly NOT converter design competence and NOT OEM qualification; the B25 governing rule stands: magnetic-sensor expertise plus this skill still does not make the founder a converter designer | BR-B test bed (and any full-run PB-3/PB-4/PB-5 successor); bench-tier credibility for the W2 lane; enabling skill for every power-domain personal-evidence path in B25 §4(f) | TRAIN under supervision: partner power-electronics lab or supervised evaluation-board practice starting at 48-100 V (B25 §4(a) EST 1-2 years dedicated practice for bench converter COMPETENCE; the narrower test-bed-operation subset targeted here is the front slice of that path, not the whole of it); supervision is part of the design, not optional | Supervising engineer's sign-off on safe operation; BR-B commissioning log (interlock checklist, capacitor-discharge verification records, staged-escalation record, zero-current pickup runs) | First supervised test-bed competence: months-scale EST (front slice of B25 §4(a)); placed on PREP_PLAN days 31-180 | WBG evaluation cell and gate drive ~$1-3K EST plus fixtures/isolation ~$1-2K EST (B25 PB-1 cost breakdown); supervision obtained by partnership, not purchase | 3 | founder, under qualified supervision
Power-product safety certification and converter/protection product engineering (IEC 62477-1-class campaigns, NRTL UL 61010-class, fault-interruption/dump engineering, DFM) | power | collaborator_or_vendor | B25 §4(b)-(c): protection/interruption engineering is HIRE-only at company scale (EST 2-4 senior engineers, 12-24 months, multi-$M per corpus-dated venture records) and certification competence is organizational — acquired by building or joining an organization that has it, never an individual add-on; record-cited $150-300K and 6-9 months for a first NRTL family (ST01-C10 record via B25); not founder-trainable inside the PhD horizon (C38/C42); B20 corrections 1 and 5 bar any 'founder's core stack' assumption | collaborator_or_vendor (engaged): a named partner/design-house/hire relationship IF any W1/W2 productization step is ever taken — never a personal-skill target in this plan | Any full-product row (P3R2-C-01, ST01-C10, ST03-ID_10 class); eventual product-grade W1 dossier credibility; explicitly NOT needed for BR-A, BR-B, or any PhD outcome | PARTNER/HIRE at company scale only, and only if a B40-ranked direction justifies it; the pilot-horizon action is zero engagement spending plus the PB-6-class desk mapping of which certification regime binds which row (deferred to the full run) | No personal artifact exists or is claimed; the artifact would be a signed partner engagement or a hire — out of scope for the 365-day plan except as a day-181-365 decision memo | Record-cited 6-9 months for a first NRTL family once an organization exists (via B25 §4(c)); $0 time in this plan beyond the decision memo | Record-cited $150-300K for a first family (via B25 §4(c)); $0 committed in this plan | 5 | partner organization / future hire (not founder)
Estimator/identifiability methodology with pre-registered honesty tests (FT-02 discipline: freeze states and inflate covariance on non-identifiable scenarios; detection-statistics variants) | shared (sensing + power) | literature_backed_near_transfer | NOT demonstrated: no estimator code exists (C10 — the T0 package is a specification, not a deliverable); the corpus's formal basis (C23 Theorem-1, Fisher rank tests) is folder-08 pre-redteam (C40) and was produced by commissioned AI missions (C50 provenance caveat — it is not evidence of the researcher's personal skill). Transfer path: B15 EV10/P0003 Kalman-fusion literature class plus the corpus's own formal spec (C23/C31) plus the demonstrated analysis-scripting base (C13). The skill becomes personal only when BR-A Phase 0 is personally executed | current_demonstrated | Opt2 Element 3 (T0 package; FT-02 'gates every dollar after it' per C31/C48); BR-A both phases; W2 detection-statistics lane (P3R2-D-01, ST01-C11 false-trigger methodology); full-run PB-3-class successors; OPT3 reconstruction fallback (C47); CN-01's record shows the method class has merchant value in far domains | Execute BR-A Phase 0 (B15 BT-1 = B10 FT-02, verbatim, zero hardware) personally; then BR-A Phase 1 (bench coil-referenced gain recovery against the Fisher-predicted interval, FT-05/BT-3/PB-5 lineage); any publication-facing novelty claim additionally requires the FT-01 kill search first (B15 honesty rule) | FT-02 pass record (frozen states + inflated covariance on Theorem-1 scenarios, wrong-prior cross-check rerun); BR-A Phase 1 pre-registered analysis and gain-recovery report | Phase 0 desk-days-to-weeks EST; Phase 1 2-4 bench-weeks EST (B25 PB-5) | $0 desk (BR-A Phase 0); $1-5K EST bench increment (BR-A Phase 1, B25 PB-5) | 2 | founder
