Timzhao0205/PhD_Career_Portfolio/01_PhD_Research/09_PAP06_Career_Portfolio_Synthesis_2026-07/pilot/A30_verify/attempt-1/SOURCES.csv

# PILOT SAMPLE — NOT FINAL — A30_verify pilot attempt-1 web sources (opened unless limitation says otherwise)
claim_id | url | title | publisher | published_date | accessed_date | source_type | stage_file | confidence | limitation
C05-DIS-01 | https://cloud.google.com/blog/topics/systems/agile-data-centers-and-systems-to-enable-ai-innovations | Agile data centers and systems to enable AI innovations | Google Cloud Blog | 2025-10-13 | 2026-07-28 | official_company_blog_primary | COMPARE.md;COMPARE.json;VERDICT.md | high | Opened in full. Confirms Deschutes contribution to OCP, published spec + design collateral (links ocp-specification-deschutes-final-2025-09-05), and 7 named vendors demoing; does not itself state 2MW/3C/80PSI figures.
C05-DIS-02 | https://www.nidec.com/en/product/news/2025/news1203-01/ | Nidec Accelerates Liquid-Cooling Adoption for AI Generation Data Centers: Prototypes Project Deschutes CDU Based on Google OCP Specification | Nidec Corporation | 2025 (page date ambiguous; extraction displayed 2025-03-12 but URL pattern and SC25 content imply on/after 2025-11) | 2026-07-28 | manufacturer_press_release_primary | COMPARE.md;COMPARE.json;VERDICT.md | high | Opened in full. Confirms OCP-spec-compliant prototype, 2MW-class, 80 PSI, IEEE-519 ULHD VFD, low approach temperature, SC25 exhibit. Published date recorded as uncertain.
C05-DIS-03 | https://www.opencompute.org/documents/ocp-specification-deschutes-final-2025-09-05-pdf | Project Deschutes: Data Center Facilities Specification (final 2025-09-05) | Open Compute Project | 2025-09-05 | 2026-07-28 | standards_body_specification_primary | COMPARE.md;COMPARE.json | existence-only | NOT OPENED: opencompute.org returned HTTP 403 to fetch. Existence and identity verified via the direct hyperlink inside opened source C05-DIS-01 and search listing; content not read.
C05-DIS-04 | https://www.opencompute.org/wiki/Cooling_Environments/Cold_Plate | Cooling Environments / Cold Plate (OCP wiki; guideline and white-paper document listing) | Open Compute Project | unknown | 2026-07-28 | standards_body_wiki_primary | COMPARE.md;COMPARE.json | discovery-only | NOT OPENED: HTTP 403. Search-level listing showed guideline/requirements/white-paper titles (incl. Cold Plate Development and Qualification white paper; L2L CDU Test Methodology performance rating white paper). Used only as discovery evidence for the partially-verified OCP-standardization-status claim.
C05-DIS-05 | https://www.datacenterdynamics.com/en/news/companies-show-off-google-inspired-project-deschutes-cdus/ | Companies show off Google-inspired Project Deschutes CDUs | Data Center Dynamics | 2025 | 2026-07-28 | trade_press | COMPARE.md;COMPARE.json | discovery-only | NOT OPENED: HTTP 403. This is new06's own cited source P3R2-C-05-S02; only its headline/search summary (naming 8 vendors incl. Stulz) was visible. The 8th-vendor claim therefore remains trade/discovery-level.
