Timzhao0205/PhD_Career_Portfolio/01_PhD_Research/10_HSX_IP_and_arXiv_Screen_2026-08/state/MODEL_LOG.csv

run_id | stage | agent | requested_model | requested_effort | observed_model | observed_effort | status | start_utc | end_utc | duration_s | turns | input_tokens | output_tokens | web_queries | cost_usd | evidence | notes
HSXIP-20260805T071311Z | 00_scope | s00-scope | claude-sonnet-5 | medium | not_exposed | not_exposed | accepted |  | 2026-08-05T07:17:39Z | 179.9 | not_exposed | not_exposed | not_exposed | not_exposed | not_exposed | agent frontmatter + task-notification usage metadata | Gate PASS. Notification exposed subagent_tokens_total=68960 (no input/output split), tool_uses=25, duration_ms=179863. end_utc is acceptance time.
HSXIP-20260805T071311Z | 10_disclosure | s10-disclosure | claude-sonnet-5 | high | not_exposed | not_exposed | accepted |  | 2026-08-05T07:28:08Z | 565.5 | not_exposed | not_exposed | not_exposed | not_exposed | not_exposed | agent frontmatter + task-notification usage metadata | Gate PASS. Notification exposed subagent_tokens_total=68798 (no split), tool_uses=9, duration_ms=565529. end_utc is acceptance time.
HSXIP-20260805T071311Z | 20_prior_art | s20-prior-art | claude-sonnet-5 | xhigh | not_exposed | not_exposed | accepted |  | 2026-08-05T08:03:17Z | 2018.5 | not_exposed | not_exposed | not_exposed | not_exposed | not_exposed | agent frontmatter + task-notification usage metadata | Gate PASS. Notification exposed subagent_tokens_total=228381 (no split), tool_uses=72, duration_ms=2018507. Stage used six research forks; two compaction deviations documented in 20_SEARCH_LOG.md section 0. end_utc is acceptance time.
HSXIP-20260805T071311Z | 30_ip_screen | s30-ip-screen | fable | xhigh | not_exposed | not_exposed | accepted |  | 2026-08-05T08:13:38Z | 521.6 | not_exposed | not_exposed | not_exposed | not_exposed | not_exposed | agent frontmatter (model: fable) + task-notification usage metadata; no fallback notice observed | Official alias resolves to Claude Fable 5. Gate PASS. No Fable flag/refusal/substitution event; flag count 0. Notification exposed subagent_tokens_total=136124, tool_uses=13, duration_ms=521615. end_utc is acceptance time.
HSXIP-20260805T071311Z | 40_uhv | s40-uhv | fable | xhigh | not_exposed | not_exposed | accepted |  | 2026-08-05T08:24:48Z | 593.9 | not_exposed | not_exposed | not_exposed | not_exposed | not_exposed | agent frontmatter (model: fable) + task-notification usage metadata; output self-reports claude-fable-5 but self-report is not accepted as observed evidence | Official alias resolves to Claude Fable 5. Gate PASS. No Fable flag/refusal/substitution; flag count 0. Notification exposed subagent_tokens_total=151868, tool_uses=26, duration_ms=593887. Added verified source V40-A (OSTI 5515925). end_utc is acceptance time.
HSXIP-20260805T071311Z | 50_arxiv | s50-arxiv | claude-sonnet-5 | high | not_exposed | not_exposed | accepted |  | 2026-08-05T08:35:37Z | 554.7 | not_exposed | not_exposed | not_exposed | not_exposed | not_exposed | agent frontmatter + task-notification usage metadata | Gate PASS. Label HOLD_ARXIV_FOR_OTL (C3-scoped) with 3 release conditions. Notification exposed subagent_tokens_total=143718, tool_uses=38, duration_ms=554721. end_utc is acceptance time.
HSXIP-20260805T071311Z | 60_red_team | s60-red-team | fable | xhigh | not_exposed | not_exposed | accepted |  | 2026-08-05T08:44:22Z | 443.4 | not_exposed | not_exposed | not_exposed | not_exposed | not_exposed | agent frontmatter (model: fable) + task-notification usage metadata; output self-reports claude-fable-5 but self-report is not accepted as observed evidence | Official alias resolves to Claude Fable 5. Gate PASS. No Fable flag/refusal/substitution; flag count 0. Notification exposed subagent_tokens_total=153903, tool_uses=13, duration_ms=443424. end_utc is acceptance time.
HSXIP-20260805T071311Z | 70_final | s70-final | fable | xhigh | not_exposed | not_exposed | accepted |  | 2026-08-05T08:53:55Z | 484.6 | not_exposed | not_exposed | not_exposed | not_exposed | not_exposed | agent frontmatter (model: fable) + task-notification usage metadata; no fallback notice observed at any point | Official alias resolves to Claude Fable 5. Gate PASS. Decision label NO_PUBLICATION_SPECIFIC_FILING_CASE_IDENTIFIED. No Fable flag/refusal/substitution; cumulative run flag count 0. Notification exposed subagent_tokens_total=196279, tool_uses=25, duration_ms=484648. end_utc is acceptance time.
