Timzhao0205/PhD_Career_Portfolio/03_Investments_and_Finance/02_Ascend_Benchmark_Mission_2026-07/40_PHASE4_PORTFOLIO/BENCHMARK_PORTFOLIO_v2.csv

Educational benchmark for a paper-trading learning exercise. Simulated allocations | not investment advice or recommendations. | v2 (accuracy patch | 2026-07-07): constructed from SCORES_v2.csv after 19/19 critical reviews + 5 re-red-teams; v1 file unchanged for comparison.
name | ticker | amount_cny | weight_pct | thesis_1line | exit_trigger | review_date
华丰科技 Huafeng Technology | 688629 | 12000 | 12.0 | Rank-1 (2.70, unchanged and re-earned cell-by-cell): still the only filing-anchored high-materiality Huawei-linked exposure in the 19-name universe (top-1 customer 60.52% now filing-explicit at 152,973.27万) — held small because W6=0 (single-customer + customer-owned IP) and 216x ttm pricing | H1-2026 report (due 2026-08-31) shows OCF still negative OR top-1 customer >=65% OR a second source (002897/002025) discloses a filing-grade Huawei supernode connector mass order (REDTEAM_688629 C1/C2/C4) | 2026-09-01
神州数码 Digital China | 000034 | 8000 | 8.0 | Rank-2 (2.00, up from v1 rank 3 as 600839 fell): cleanest tier-A evidence in the set (神州鲲泰 Kunpeng+Ascend own-brand, 5.18% ceiling of revenue, +62% YoY) at the cheapest P/S (0.18x) among verified-link names; razor margins and erratic OCF cap it (W3=1) | H1-2026 神州鲲泰/own-brand line growth <20% YoY OR FY2026 consolidated OCF negative again OR own-brand segment share still <5% at FY2026 report | 2026-09-01
中际旭创 Innolight | 300308 | 8000 | 8.0 | Rank-3 (2.00): held NOT as an Ascend name (sleeve <=9.42% and falling) but as the book's only anti-correlated hedge — a policy detente that hurts every other position plausibly helps it; strongest W3 in the set; ceiling logic re-earned by FR with an independent top-5 bound | 1260H follow-through: any named top-5 customer re-sourcing action by 2026-12-31 OR inventory grows faster than revenue again in Q3-2026 report OR CPO-generation deployment with 300308 absent from disclosed engine supply (REDTEAM_300308 checks 2/3/4) | 2026-09-01
深南电路 Shennan Circuits | 002916 | 8000 | 8.0 | Rank-4 (2.00, up from v1 rank 7 — the patch's one durable upgrade): diversified genuinely-growing AI-server board business (W3=4, W6=4, top-5 only 18.42%) whose W4 was re-read under R0.5 — the priced narrative is its OWN tier-1 AI-server demand, not the tier-C Ascend rumor (REDTEAM_RESPONSES_v2 R0.5a); the Ascend-specific link itself stays tier C | FY2026 data-center segment growth turns negative OR a named non-domestic customer loss >5% of revenue OR the anonymized #1 customer (7.46% ceiling) is disclosed as non-AI-related (V_002916 §trail) | 2026-09-01
中芯国际 SMIC | 688981 | 6000 | 6.0 | Rank-5 (1.90): the structural bottleneck (tier-B: named 910C/7nm and 950PR/N+3 attributions) — smallest weight because exposure is NOT-ESTIMABLE by design, capex ~3x OCF, 247x ttm prices the scarcity, and the Hua Hong/Huali second-source buildout trims forward exclusivity (FR_688981) | FY2026 capex guidance cut >20% from the ~USD 8.1bn level OR utilization <80% for two consecutive quarters OR any tier<=2 report that Ascend fabrication is moving to Huawei-dedicated (SiCarrier-equipped) non-SMIC fabs | 2026-09-01
CASH 现金 (simulated) | CASH | 58000 | 58.0 | Per SCORING_RUBRIC construction rule: zero of 19 names clears the 3.0 bar after the patch's adversarial pass (max 2.70); 17 of 19 valuation flags are PRICED-FOR-PERFECTION; the patch DEMOTED more names than it upgraded (SCORING_NOTES_v2 §2), so the honest benchmark holds slightly MORE powder than v1 (58% vs 56%) | Redeploy only if a name's total crosses 3.0 on new tier<=B evidence (e.g., a company-confirmed Ascend order book) or the pricing regime breaks (chain-median P/E ttm halves) | 2026-09-01
