Timzhao0205/PhD_Career_Portfolio/01_PhD_Research/09/sources/phd/P/01/05_HSX_ChatGPT_Windows_App/outputs/cad/50B_SERVICE_KEEPOUTS_NFF.step

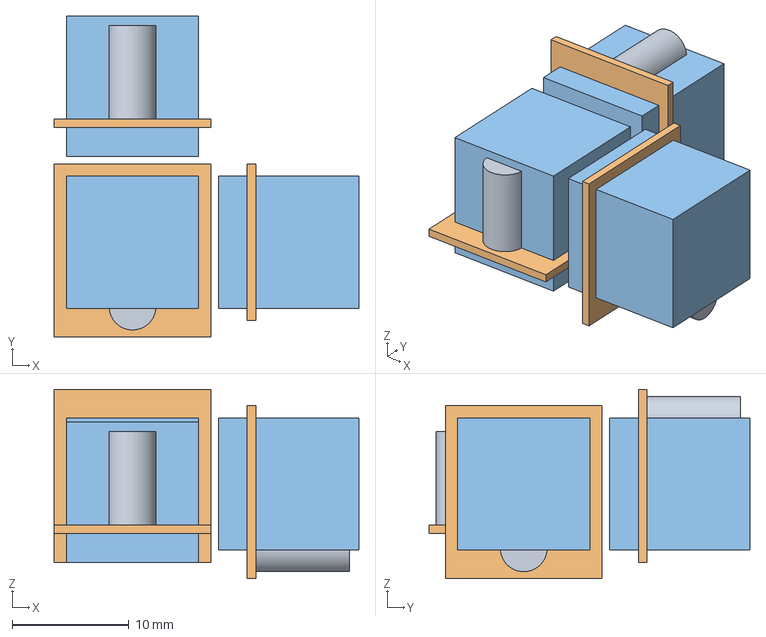
[picture p20: CAD file, 2026-07-13, last stored version]
01_PhD_Research/09/sources/phd/P/01/05_HSX_ChatGPT_Windows_App/outputs/cad/50B_SERVICE_KEEPOUTS_NFF.step
26.1 x 27.5 x 16.2 mm
