Timzhao0205/PhD_Career_Portfolio/01_PhD_Research/09/sources/phd/P/01/05_HSX_ChatGPT_Windows_App/outputs/cad/30D_KEEP_NFF.step

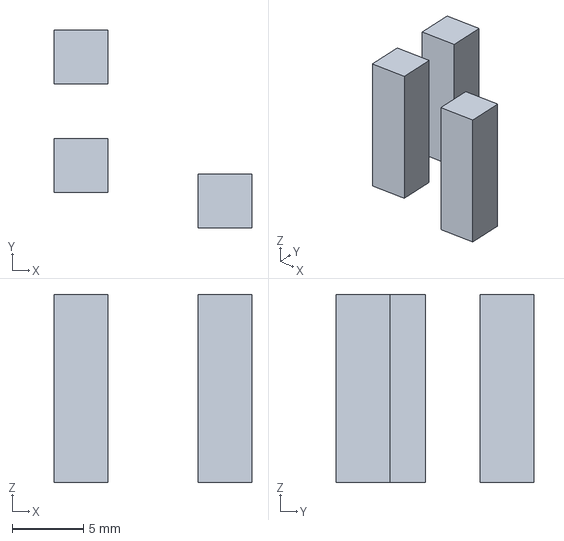
[picture p24: CAD file, 2026-07-13, last stored version]
01_PhD_Research/09/sources/phd/P/01/05_HSX_ChatGPT_Windows_App/outputs/cad/30D_KEEP_NFF.step
13.9 x 13.9 x 13.2 mm
