Timzhao0205/PhD_Career_Portfolio/01_PhD_Research/09/sources/phd/P/01/05_HSX_ChatGPT_Windows_App/outputs/cad/50B_COST_DOWN_NFF.step

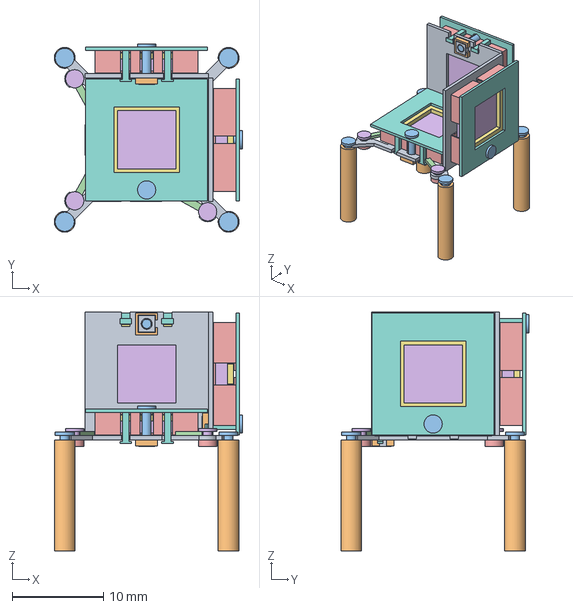
[picture p25: CAD file, 2026-07-13, last stored version]
01_PhD_Research/09/sources/phd/P/01/05_HSX_ChatGPT_Windows_App/outputs/cad/50B_COST_DOWN_NFF.step
20.7 x 20.7 x 26.2 mm
