Timzhao0205/PhD_Career_Portfolio/01_PhD_Research/09/sources/phd/P/01/05_HSX_ChatGPT_Windows_App/outputs/cad/30B_monolithic_core_ceramic_NOT_FOR_FABRICATION.stl

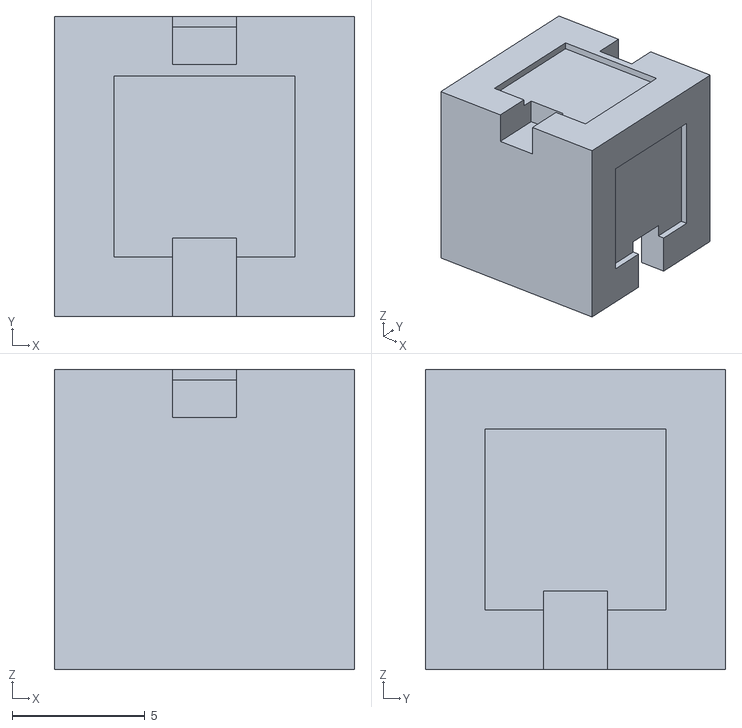
[picture p29: CAD file, 2026-07-13, last stored version]
01_PhD_Research/09/sources/phd/P/01/05_HSX_ChatGPT_Windows_App/outputs/cad/30B_monolithic_core_ceramic_NOT_FOR_FABRICATION.stl
11.3 x 11.3 x 11.3
