Timzhao0205/PhD_Career_Portfolio/03_Investments_and_Finance/01_Market_Learning_Lab_2026-07/20_JOURNAL/2026-07-05_W00_setup.md

# 2026-07-05 (W00) — Lab setup

Lab scaffolded from portfolio conventions. Seed case chosen: Huawei 计算 rumor
(70B this year / 200B next year) → traced in RB_01; supplier map drafted in RB_02
with evidence tiers. First calibration prediction opened (P001).

Next session: Stage 0 of LEARNING_ROADMAP.md — read "how a stock price forms" material,
then verify one tier-C watchlist row against the company's own filing (upgrade or drop it).
