Timzhao0205/PhD_Career_Portfolio/03_Investments_and_Finance/02_Ascend_Benchmark_Mission_2026-07/10_PHASE1_VERIFICATION/V_688519.md

Educational benchmark for a paper-trading learning exercise. Simulated allocations, not investment advice or recommendations.

# V_688519 — 南亚新材 Nanya New Material Technology (688519.SH, SSE-STAR) — Phase 1 Filing Verification (PATCH PP1)

## Claim under test
Per `10_PHASE1_VERIFICATION/EXPANSION_SELECTION.md` #5 and `00_PRIOR_CORPUS/RB_02_ascend_supply_chain_map.md`'s
"PCB/CCL/substrate" row (tier B–C, [S009;S010]): 南亚新材 supplies copper-clad laminate (CCL) — the
resin/copper/glass-fiber composite material that PCB fabricators press into printed-circuit boards — into
Huawei/Ascend AI-server boards, and carries a "historic Huawei-qualified supplier" reputation. This file
tests, from filings/IR records with dates: (a) any NAMED Huawei/server-OEM customer disclosure (killing or
confirming that a pre-2021 qualification is not being passed off as current evidence); (b) high-speed
(M6/M7-grade) laminate revenue share and whether filings tie it to AI-server demand; (c) 上证e互动 replies on
华为/昇腾/AI服务器; (d) whether the chain runs CCL → PCB maker → Huawei (indirect) rather than CCL → Huawei
directly, and whether that indirection is stated honestly in the exposure method.

## Company-identity check (confusion-avoidance, done first per task brief)
Confirmed this file is about **南亚新材料科技股份有限公司 (Nanya New Material Technology Co., Ltd.)**,
688519.SH, SSE STAR Market, registered 2000-06-27, headquartered 上海市嘉定区南翔镇, IPO 2020-08-18 at
RMB33/share, core product = copper-clad laminate / adhesive sheet (覆铜板/粘结片) [S984]. This is a **distinct
Mainland China entity, NOT**: (i) Taiwan's 南亚塑胶工业 / Nan Ya Plastics Corp (1303.TW, petrochemicals/
plastics, part of Formosa Plastics Group); or (ii) Taiwan's 南亚科技 / Nanya Technology Corp (2408.TW, DRAM
memory maker, also Formosa-Group-linked). No source used below is from a Taiwan-listing context; every
figure below traces to 688519.SH filings or 688519-specific media coverage.

## Filings fetched / documented environment-trap trail (read first)
**Every direct PDF-fetch attempt this session failed with the same technical signature documented elsewhere
in this mission** (WPS-Office-generated PDF; FlateDecode-compressed streams with no machine-readable text
layer, in several cases confirmed image/SMask-based). Attempts, in order:
1. `static.cninfo.com.cn/finalpage/2026-03-26/1225031388.PDF` — the FY2025 annual report itself (215pp,
   cninfo primary host) — failed (confirmed image-based PDF, WPS-generated, SMask layer present).
2. `www.cfi.net.cn/p20260326000644.html` (中财网 2025年年度报告摘要 landing page) — tried twice; page shell
   loaded but report body/PDF link did not render extractable text either time.
3. `mb.hibor.com.cn/report/...` (慧博投研资讯 2025年年度报告摘要 mirror) — landing page only, PDF link not
   text-extractable.
4. `pdf.dfcfw.com/pdf/H2_AN202603251820746592_1.pdf` (东方财富 full FY2025 annual report mirror) — failed,
   same WPS/FlateDecode signature.
5. `stockmc.xueqiu.com/202604/688519_20260428_YC1P.pdf` (雪球 Q1-2026 quarterly report mirror) — failed,
   same signature.
6. `file.finance.sina.com.cn/.../2026-05-13/12313667.PDF` (新浪 mirror of the SSE inquiry-letter reply's
   detailed appendix, table of contents visible: "一、关于经营业绩...二、关于盈利质量...") — failed, same
   signature.
7. `static.sse.com.cn/stock/disclosure/announcement/c/202605/688519_20260512_ZH1F.pdf` (SSE static host) —
   failed; confirmed image-based (71 pages, embedded JPEG streams).

**Workaround used (per documented environment-limitation guidance):** every figure below is instead sourced
from HTML-rendered financial-media pages that DID parse — critically including **`paper.cnstock.com` (上海
证券报)**, one of the four CSRC-designated mandatory print venues for A-share information disclosure, which
republishes the FULL TEXT of company announcements (its 2025年年度报告摘要 [S989] and 2025年年度报告问询函回复
[S985] pages carry granular, internally-consistent, arithmetic-checkable figures — see cross-checks below) —
plus 同花顺F10 [S984], 证券之星/东方财富/新浪/搜狐/财联社/腾讯新闻/证券时报网 relays of the 业绩快报 and annual
report [S980–S983, S990–S996], 发现报告's relay of a dated institutional-investor meeting record [S987], and
一篇 2020-vintage 金证研 investigative piece for historical context [S986]. Per SOURCE_STANDARDS' mirror rule,
every source below is logged at the tier of the page actually fetched (tier 3, tier 4 for the one forum
post), never promoted to tier 1 — including the cnstock pages, despite their statutory-disclosure-reproduction
status, to keep this file consistent with this mission's established convention (see V_301236 for precedent).

**Gate check:** 0 directly-fetched tier-1 PDFs (7 documented failed attempts above); 17 fetched tier-3/4
HTML sources used instead [S980–S996], cross-validated internally (see arithmetic checks in Evidence §A/B).

## Evidence (verbatim, dated)

### A. FY2025 headline financials (converges across 5 independently fetched sources)
> "本公司实现营业收入522,782.88万元，同比增长55.52%；实现归属于母公司所有者的净利润24,085.93万元，同比增长
> 378.65%" — 2025年度业绩快报公告 (preliminary results announcement), relayed by 证券之星, 2026-02-25 [S980]
> and 东方财富财富号, 2026-02-26 [S981] (both give the identical 378.65% figure and 万元-denominated totals).
> *Gloss: FY2025 revenue RMB522,782.88万元 = RMB52.278亿元 (≈RMB5.228bn — NOT "52 billion"; 万元→亿元→USD
> unit trap flagged per task brief). Net profit attributable to parent RMB24,085.93万元 = RMB2.409亿元
> (≈RMB240.9m).*

> "南亚新材2025年营业收入52.28亿元，同比增长55.52%…归母净利润2.40亿元，同比增长377.60%" — 新浪财经,
> 2026-03-27 [S995]; consistent with 新浪财经AIGC citing 光大证券核查意见, 2026-05-12 [S990, cross-confirmed
> by an independent 搜狐 relay of the same content, also 2026-05-12, S991]; and 腾讯新闻, 2026-03-27 [S982].
> *Gloss: **CONFLICT flagged per SOURCE_STANDARDS rule 5, not averaged**: the preliminary 业绩快报 [S980,S981]
> gives net-profit growth as 378.65%; four later, annual-report-vintage sources [S982,S990,S991,S995] all
> independently converge on 377.60% instead. This is very likely a small final-vs-preliminary revision (common
> in China A-share reporting between 业绩快报 and the audited 年度报告), not a data-quality problem — both
> figures are recorded, neither is treated as authoritative over the other.*

### B. Segment/product revenue — arithmetic cross-checked
> "覆铜板：405,491.30万元（同比增长55.76%）；粘结片：107,201.63万元（同比增长53.89%）；其他业务：10,089.95万元
> （同比增长63.80%）" — 新浪财经AIGC, 2026-05-12 [S990], confirmed by independent 搜狐 relay same date [S991]
> and consistent with 新浪财经, 2026-03-27 [S995, gives 40.55亿/10.72亿元 and the same 55.76%/53.89% growth
> rates].
> *Gloss: **Verified by direct arithmetic (my own check, not sourced)**: 405,491.30 + 107,201.63 + 10,089.95
> = 522,782.88万元 — an EXACT match to the FY2025 total revenue figure in §A. This confirms the segment
> figures and the total are internally consistent and correctly scaled (万元, not 亿元).*

> "南亚新材料科技股份有限公司关于上海证券交易所2025年年度报告的信息披露监管问询函的回复公告"…"覆铜板收入：
> 40.55亿元，同比增长53.09%；粘结片收入：10.72亿元，同比增长63.71%" — 上海证券报, 2026-05-13 [S985].
> *Gloss: **Second conflict, flagged not averaged**: this SSE-inquiry-reply relay gives different growth
> rates (53.09%/63.71%) than the three converging sources in the paragraph above (55.76%/53.89%) for the
> SAME absolute revenue figures (40.55亿/10.72亿元 match exactly). Three independent fetches agree with each
> other; one differs — noted as a pattern, not used to silently discard the outlier value.*

> "高频高速及IC载板材料收入增长最为显著，2025年实现收入9.25亿元，同比增长80.60%"…"普通及无卤、无铅材料：
> 42.02亿元，增长50.73%" — 新浪财经AIGC/光大证券核查意见, 2026-05-12 [S990, S991]; consistent with 上海证券报's
> inquiry-reply relay: "高频高速及IC载板材料收入增幅最快，同比增长80.60%" [S985, same 80.60% figure — this one
> growth rate is corroborated across BOTH the convergent-three and the outlier source].
> *Gloss: 9.25 + 42.02 = 51.27亿元 ≈ CCL+adhesive-sheet total (40.55+10.72 = 51.27亿元) — this confirms
> "high-speed+IC-substrate" and "regular/halogen-free/lead-free" are a BY-GRADE cut of the same CCL+prepreg
> revenue, not an additional segment. This RMB925m high-speed+IC-substrate figure is the most granular
   disclosed bucket that could plausibly house 100% of any Huawei/Ascend-linked business — see Exposure §.*

### C. Customer concentration — the chain-indirection finding (own regulatory filing, relayed)
> "覆铜板产品前五大客户分别为奥士康、方正科技、深南电路、江西旭昇和景旺电子，粘结片前五大客户分别为奥士康、
> 方正科技、深南电路、特创集团和景旺电子，均为业内知名的PCB企业" — 上海证券报, relaying 南亚新材's reply to
> the SSE's 信息披露监管问询函 (information-disclosure regulatory inquiry letter, 问询函编号 上证科创公函
> 〔2026〕0120号, received 2026-04-22, replied 2026-05-13) [S985].
> *Gloss: **This is the single most important finding for the chain-indirection question the task brief asks
> to check.** The company's OWN regulatory filing names its top-5 customers for BOTH products — and every
   single one is a PCB fabricator (奥士康/Aosikang, 方正科技/Founder, 深南电路/Shennan Circuit, 江西旭昇,
   特创集团/Techead, 景旺电子/Kingboard) — never Huawei, never any end-brand OEM. Per assumption A8, this is
   NOT silently equated with a Huawei relationship. The chain is confirmed, in the company's own words, to run
   CCL (Nanya) → PCB fabrication (named customers) → [unnamed] end-brand assembly — exactly the indirection
   the task brief flags.*

> "应收款项前五大欠款方占含税销售收入比例为51.93%" [S985, same filing]; separately, "2025年末，公司应收款项
> 合计达31.98亿元，占当年营业收入的比例高达61%" — 证券时报网, ~2026-05-14 [S983], and "应收账款同比增幅达
> 68.59%" corroborated by 腾讯新闻, 2026-03-27 [S982] and 新浪财经AIGC, 2026-05-12 ("应收账款：24.66亿元，同比
> 增长68.59%；应收票据7.32亿元") [S990,S991].
> *Gloss: These reconcile arithmetically: RMB24.66亿 (应收账款/accounts receivable) + RMB7.32亿 (应收票据/
   notes receivable) = RMB31.98亿 (应收款项合计/total receivables) [S990/S991 + S982/S983] — different line
   items, not a contradiction. Top-5-debtor concentration (51.93%, a receivables-based proxy for customer
   concentration) is the closest thing to a "top-5 customer % of revenue" figure found in any source this
   session; a clean "前五名客户合计销售金额占年度销售总额比例" figure (the standard annual-report disclosure
   format) was searched for but not found in any successfully-fetched source — flagged in the search trail.*

> "南亚新材已与沪电股份、景旺电子、胜宏科技、深南电路、生益电子等知名PCB厂商建立长期合作关系" — 财联社,
> 2026-05-11 [S992].
> *Gloss: independently broadens the confirmed PCB-fabricator customer network to 8 distinct named companies
   (adding 沪电股份/WUS, 胜宏科技/Victory Giant, 生益电子/Kinwong[Shengyi Electronics subsidiary] to the SSE-
   filing list) — reinforcing, from a second independent source, that Nanya's disclosed/reported customer
   relationships are consistently PCB fabricators, not Huawei directly.*

### D. Huawei/Ascend-named evidence — current, FY2025-dated (the core of the claim)
> "国内客户推出的大模型及超节点，自主开发昇腾、海光等系列已经实现市场批量交付。公司在国内前述头部客户均已经
> 实现量产导入，其中M6、M7层级的材料在2025年实现稳定且高质量的量产交付" — 南亚新材料科技股份有限公司2025年
> 年度报告摘要 (FY2025 annual report summary), full text reproduced by 上海证券报 (one of the four CSRC-
> designated statutory disclosure newspapers), 2026-03-26 [S989].
> *Gloss: **The strongest single piece of evidence in this file.** This is the company's own annual-report
   language (relayed via a statutory verbatim-reproduction venue, though I could not independently parse the
   raw PDF myself — see Filings-fetched trail) explicitly naming 昇腾 (Ascend) BY NAME, alongside 海光 (Hygon,
   a separate, non-Huawei domestic x86-licensed CPU maker), as end-chip series into which the company's
   materials have "already achieved market-scale batch delivery" (已经实现市场批量交付), with M6/M7-grade
   material specifically confirmed as reaching "stable, high-quality mass-production delivery" in 2025. This
   is dated (FY2025, filed 2026-03-26) and specific (names the chip series, names the material grade) — not a
   generic "AI" claim.*

> "报告期内，公司800Gbps高速材料NOUYA8U成功通过华为等核心头部客户认证并实现规模化量产" — 新浪财经, relaying
> FY2025 annual-report-vintage language, 2026-03-27 [S995]. Same article: "M6-M8等级AI服务器专用覆铜板产品
> 技术持续优化，市场供应规模稳步扩大."
> *Gloss: Independently and consistently names 华为 (Huawei) explicitly as a certifying customer for a named
   product (NOUYA8U, an 800Gbps-class high-speed material), with mass production confirmed for FY2025 — a
   SEPARATE, independently-fetched source corroborating the Ascend-naming quote above (different document,
   same reporting period, same qualitative conclusion: current, named, dated Huawei/Ascend technical
   relationship). Note the verb is "认证" (certification/qualification) — technical qualification is
   typically conducted directly between the material maker and the end-brand OEM even when the commercial
   invoice flows through the PCB-fabricator intermediary (§C) — this is consistent with, not contradictory
   to, the chain-indirection finding.*

### E. Institutional investor meeting — company's own dated Q&A (2025-06-27)
> "是迄今为止各介质损耗等级全系列产品唯一通过华为认证的内资覆铜板企业" — company statement at an institutional
> investor research meeting (机构调研), dated 2025-06-27, relayed by 发现报告 [S987].
> *Gloss: company's own claim (at a dated IR event) to be the ONLY domestic-capital CCL maker to have passed
   Huawei certification across the FULL series of products at ALL dielectric-loss grades, "to date" (迄今为止)
   — reinforces D above with a THIRD independently-dated document (2025-06-27, ~9 months before the FY2025
   annual report).*

> Same meeting, Q4: "NY6300S全面进入多客户PCIe Gen5服务器量产，PCIe Gen6完成头部客户测评，进入产品预研阶段；
> AI服务器突破多客户国产GPU方案" [S987]. Q12: "智算GPU模组224G产品目前我司提供了NY-8888Q和NY-9999Q Low CTE
> 解决方案配合客户预研" [S987].
> *Gloss: notably, when asked directly about AI-server/domestic-GPU business, the company's own answer uses
   the GENERIC phrase "多客户国产GPU方案" (multiple customers' domestic GPU solutions) — it does NOT name
   Huawei/Ascend specifically in this particular answer, unlike D above. Presented as-is; illustrates that
   not every company statement on this topic names Huawei, even in the same meeting where Huawei IS named
   elsewhere (E, first quote).*

### F. Investor-platform Q&A — company declines to quantify (2026-04-27)
> Investor question (paraphrased in the relay): whether M6-M7 grade materials have achieved batch delivery
> into 昇腾/海光 domestic compute chains. Company reply, verbatim: "公司M10高端材料已顺利完成技术研发与攻关，
> 现阶段多家客户认证工作稳步开展中" — relayed via 东方财富股吧 (eastmoney guba), posted 2026-04-27, company
> reply timestamped same day 14:14 [S988, **tier 4 — forum-hosted relay of an investor-platform exchange; not
> independently confirmed on a primary 上证e互动 page despite a direct search attempt (see search trail) — used
> here only as a LEAD/color note per SOURCE_STANDARDS, never load-bearing**].
> *Gloss: the company's reply does not directly confirm or deny the 昇腾/海光 framing in the investor's
   question, and — notably — does not offer any percentage or revenue figure. No ">60% of Ascend-server
   material supply" or similar quantified claim appears anywhere in this exchange; see §G for an explicit
   debunk of a circulating quantified claim.*

### G. Debunked / unverifiable claims found circulating (explicit negative findings)
- **">60% of Huawei Ascend server material supply" claim: SEARCHED FOR, NOT FOUND in any fetched source.**
  An AI-search-summary surfaced the phrase "在华为昇腾服务器材料供应占比超60%" during this session's research,
  but the underlying forum post it appeared to reference [S988, fetched directly] contains NO percentage
  figures of any kind. No other search or fetch this session located a primary or tier-≤3 source for this
  number. **Not used anywhere in this file's exposure estimate** — flagged as a claim that did NOT survive
  verification, per SOURCE_STANDARDS ("a tier-C claim repeated across ten posts is still tier C" — this one
  did not even clear tier C on a direct check).
- **Nvidia M9/Rubin/GB300 certification claim: LIKELY A COMPANY-CONFUSION ARTIFACT, not confirmed for 688519.**
  Search summaries repeatedly asserted "南亚新材M9级高速覆铜板获英伟达认证...通过胜宏、沪电批量供货Rubin/GB300."
  A direct, independently-fetched 财联社 article on this exact topic (2026-05-11) [S992] states only that
  Nanya's M9-grade product "已通过国内算力终端头部客户认证，处于NPI项目导入阶段" (passed a GENERIC "domestic
  computing-power terminal leading-customer" certification, still at pre-mass-production NPI stage) — Nvidia
  is NOT named anywhere in this fetched article as a Nanya counterparty. The same search round separately
  and explicitly attributed the specific "大陆唯一、全球第二家英伟达M9认证" (mainland-China's only, world's
  second Nvidia-M9-certified) status to a DIFFERENT company, 生益科技 (Shengyi Technology, 600183.SH) — a
  same-industry, easily-confused peer. This file does NOT use any Nvidia-linked figure for 688519. Flagged
  explicitly because it illustrates the exact kind of cross-company conflation risk the task brief warned
  about (Taiwan-name confusion was the named risk; this is an analogous same-sector-peer confusion risk).

### H. Q1 2026 (latest quarterly, per A3)
> "第一季度，公司实现营业收入18.32亿元，同比增长92.36%。归属于上市公司股东的净利润1.5亿元，同比增长610.83%"
> — 东方财富财富号, 2026-04-28 [S994]; 扣非归母净利润1.48亿元，同比增长823.15% [S994].
> *Gloss: revenue and profit growth accelerated further into Q1 2026 (+92.36%/+610.83% YoY) vs FY2025's
   already-high +55.52%/+377.60%. No source fetched this session broke out AI-server, Ascend, or Huawei-
   specific revenue for the quarter — none is stated here per NUMBER TRUTH RULE.* Separately, a FY2025
   dividend distribution of RMB0.32/share (RMB72,899,152.96 total, net of treasury shares) was implemented
   around this filing [S996].

### I. Governance/quality flags — independent of the Huawei thesis, but relevant context
> SSE's own 信息披露监管问询函 (received 2026-04-22) targeted, per 证券时报网's description: "利润与经营现金流
> 严重背离、应收账款大幅激增、存货异常暴涨、关联交易显著增加、海外业务毛利率异常偏低" — ~2026-05-14 [S983].
> Company's own reply figures: operating cash flow FY2025 = -RMB8,318.46万元 (≈-RMB83.2m) vs +RMB3.25亿元
> (≈+RMB325m) in FY2024 — a swing of ≈RMB408m even as net profit grew 377–379% [S982, S983]; overseas gross
> margin 8.11% vs domestic 12.19% [S982]. Separately, SSE issued a 监管警示 (regulatory-warning decision) on
> 2025-09-10 for a share-buyback rule violation (selling repurchased shares exceeding 1% of total shares
> within a rolling 90-day window, 2025-05-22 to 2025-08-18) [S989, relayed within the same annual-report-
> summary article]. Light-year/Everbright Securities (光大证券), acting as sponsor, issued a verification
> opinion (核查意见) concluding revenue/margin growth "具有可持续性...关联交易定价公允" [S990, S991].
> *Gloss: these are customer-concentration-adjacent and cash-conversion-quality flags unrelated to the
   Huawei/Ascend thesis specifically, but relevant given §C's finding that the customer base (PCB fabricators)
   is concentrated and, per a 2020-vintage source, has had at least one historical independent-director
   overlap with two of those same named customers (奥士康, 深南电路) raising an independence question at the
   time [S986] — noted for later-phase risk sections, not scored or ranked here.*

## Tier assigned + reasoning
**Tier B** for the Huawei/Ascend link. Reasoning:

**Why not C/UNVERIFIED:** the claim clears tier C by a wide margin. Three SEPARATELY DATED, independently
fetched documents — an institutional-investor meeting record (2025-06-27, [S987]), the FY2025 annual report's
own abstract language relayed via a statutory disclosure newspaper (2026-03-26, [S989]), and a Sina Finance
relay of annual-report-vintage language the next day (2026-03-27, [S995]) — all independently and consistently
describe a CURRENT (not merely historic), NAMED (昇腾 explicitly, not generic "AI") Huawei/Ascend certification-
and-mass-production relationship for specific material grades (M6/M7; the NOUYA8U 800Gbps product). This is
substantially more than forum chatter, and it upgrades RB_02's original C-floor for this row.

**Why not A:** four things distinguish this from a clean Tier-A call (contrast with V_301236's Huawei
percentage, which reached A):
1. **No direct tier-1 fetch succeeded.** All 7 attempts at the actual filing PDF (cninfo, sina mirror, dfcfw
   mirror, xueqiu mirror, SSE static host) failed with the same unparseable-PDF signature — every quote above
   is a media RELAY of filing language, not a document I parsed myself, even though the strongest relay venue
   (上海证券报) is a statutorily-designated disclosure-reproduction outlet.
2. **No Huawei-specific revenue percentage is disclosed anywhere** — every piece of evidence is qualitative
   ("已实现市场批量交付," "已通过认证") rather than quantified, unlike 301236's explicit 53–56% IPO-prospectus
   figures.
3. **The company's own customer-concentration disclosure (§C) never names Huawei** — top-5 customers for both
   CCL and adhesive-sheet products are exclusively PCB fabricators (奥士康/方正科技/深南电路/江西旭昇/特创集团/
   景旺电子), confirmed by the company's own SSE regulatory-inquiry reply. This is a genuine, filing-confirmed
   CHAIN INDIRECTION (CCL → PCB maker → Huawei/OEM) that the task brief specifically asked to check for and
   report honestly — it is real, and it caps how directly "Huawei is a customer" can be asserted.
4. **No independent Huawei-side confirmation** was found (no Huawei-hosted partner list or ecosystem page
   naming 南亚新材, unlike 301236's devicepartner.huawei.com and Huawei Connect 2025 corroboration).
Net: real, dated, named, current — but relayed-not-fetched, unquantified, and running through an admitted
intermediary layer. **Tier B** is the honest ruling; forum-only items (§F [S988], the >60%/Nvidia-M9 claims
in §G) are explicitly excluded from supporting this tier per the "tier-C claims are never load-bearing" rule.

## Exposure estimate
**NOT-ESTIMABLE as a clean point figure. Bounding method shown; ceiling ≈17.70% of FY2025 revenue.**

**Ceiling calculation:** 高频高速及IC载板 (high-speed + IC-substrate) product-grade segment revenue,
RMB9.25亿元 (925.0m) ÷ FY2025 total revenue RMB52.278亿元 (5,227.8m) = **17.70%** [S990, S991, cross-confirmed
80.60% YoY growth rate by S985]. This is the most granular disclosed revenue cut that could plausibly contain
100% of any Huawei/Ascend-linked business (per §D, Ascend/Hygon-linked material is specifically the M6/M7
high-speed grade).

**Why this ceiling substantially OVERSTATES true Huawei/Ascend-specific exposure — the same disclosed segment
bundles, by the company's own filings, at least four other non-Huawei-exclusive demand sources:**
1. **海光 (Hygon)** — named in the IDENTICAL sentence as 昇腾 in the annual-report-abstract quote (§D) — a
   separate, non-Huawei, x86-license domestic CPU/DCU maker.
2. **Generic AI-server/switch/optical-module demand** — the 定增 (private placement) prospectus targets
   "AI服务器、交换机、光模块等高端应用领域" broadly [S993], not Huawei/Ascend specifically.
3. **5G/6G telecom** — the ORIGINAL, longest-standing Huawei-certified end-market (per §E's historic-context
   check, certification dates to at least 2020 for telecom-grade VLL/ULL materials, alongside 中兴/ZTE per the
   2020-vintage source [S986]) — telecom demand is not Ascend-server demand and is not separable from it in
   any disclosed figure.
4. **DRAM/NAND storage-packaging materials** — explicitly named within the same IC-substrate-materials
   narrative as serving "全球核心龙头终端" (unnamed global-leading memory makers) — unrelated to Huawei/Ascend.
5. **Possible non-Huawei domestic/international compute-chain demand** — per §G, the company's own M9
   disclosure uses the deliberately generic phrase "国内算力终端头部客户" rather than naming Huawei, and no
   source confirms whether that specific tier's eventual customer is Huawei, a different domestic AI-chip
   maker, or (per the debunked-but-circulating claim) an international counterparty.

**No source found this session discloses a sub-split of the RMB925m figure by end-chip-vendor, by domestic-
vs-telecom application, or by any other cut that would isolate a Huawei/Ascend-only number.** The company's
own top-5-customer table (§C) — the most granular disclosed customer-level data — names only PCB fabricators,
which is one further step of indirection removed from any chip-vendor split. **Method = segment-ratio ceiling
(17.70%, an explicit overstatement bound); Huawei/Ascend-specific point estimate = NOT-ESTIMABLE.** A rough
qualitative read (not a number, not sourced as a figure) is that the true share is a FRACTION of that ceiling,
most plausibly concentrated in the M6/M7 mass-production tier specifically named alongside 昇腾/海光 — but
splitting that further between Huawei-Ascend and Hygon, let alone quantifying it, is not supported by any
disclosure found.

## Risks/notes for later phases (facts only, no scores/rankings)
- **Chain indirection is real and filing-confirmed** (§C): any later-phase valuation work should describe
  Nanya's Huawei/Ascend exposure as running through named PCB-fabricator intermediaries (奥士康/深南电路/
  景旺电子/沪电股份/胜宏科技/生益电子/方正科技/江西旭昇/特创集团), not as a direct Huawei revenue relationship
  — no source found this session shows Huawei (or any single end-brand OEM) as a directly named top-5 customer.
- **Two internal growth-rate conflicts unresolved** (§A, §B): net-profit growth 378.65% (业绩快报) vs 377.60%
  (annual-report-vintage, 4 sources); CCL/adhesive-sheet segment growth 55.76%/53.89% (3 converging sources)
  vs 53.09%/63.71% (1 source, the SSE-inquiry-reply relay). Both pairs recorded per SOURCE_STANDARDS rule 5;
  neither averaged nor silently dropped.
- **Cash-conversion-quality flag**: FY2025 operating cash flow swung to -RMB83.2m from +RMB325m in FY2024
  even as reported net profit grew 377–379% YoY, and receivables grew 68.59% YoY to a 51.93–61%-of-revenue
  concentration depending on the metric used — this triggered SSE's own regulatory inquiry letter (received
  2026-04-22) [§I]. Independent of the Huawei/Ascend thesis, but material to any later profitability-quality
  assessment.
- **Two debunked/unconfirmed circulating claims** (§G) should NOT be reused in later phases without
  independent re-verification: the ">60% of Huawei Ascend server material supply" figure, and Nvidia-M9/
  Rubin/GB300 certification for 688519 specifically (the fetched evidence attributes a comparable Nvidia-M9
  claim to a different, easily-confused peer, 生益科技/600183).
- **Historical-independence flag** (§I, 2020-vintage): a former independent director held simultaneous or
  near-simultaneous board seats at 688519 and two of its largest customers (奥士康, 深南电路) — a governance
  note orthogonal to the Huawei thesis but relevant to overall diligence quality.
- **No 上证e互动 primary-platform page was successfully fetched directly** despite a targeted search attempt
  (see search trail below) — the one investor-platform exchange found on this topic was relayed via a tier-4
  forum mirror [S988] and is explicitly not load-bearing; a future auditor with access to sns.sseinfo.com's
  full-text search could potentially upgrade §F/§G to a citable primary source.

## Honest per-URL search trail — not found / could not verify
- **上证e互动 (sns.sseinfo.com) direct company Q&A page**: attempted `sns.sseinfo.com/comdetail.do?comcd=688519`
  directly — returned no substantive Q&A content (likely wrong URL pattern for this platform's current site
  structure). Follow-up WebSearch for `site:sns.sseinfo.com` + 南亚新材/华为/昇腾 returned only generic user-
  profile pages, not indexed Q&A text — the platform does not appear to be well-indexed by the search engine
  used this session. Not resolved; the F/G-section forum-relayed exchange is the closest substitute found.
- **A clean "前五名客户合计销售金额占年度销售总额比例" figure** (the standard annual-report total-top-5-
  customer-concentration disclosure format): searched for specifically; not found in any successfully-parsed
  source this session (only the receivables-based 51.93% proxy [S985] and a named-but-unquantified customer
  list were found).
- **M8-grade production-status claim** ("M8等级高端材料在AI服务器小批量生产"): appeared as a search-result
  article title (和讯网, 2025-08-11) but the article itself returned HTTP 567 on fetch attempt — NOT used
  anywhere in this file per NUMBER TRUTH RULE (search-result titles are snippet-grade, never load-bearing).
- **">60%" Ascend-server-supply-share figure and Nvidia-Rubin/GB300 certification for 688519 specifically**:
  actively searched for a citable source; both explicitly NOT found on direct fetch — see §G for the full
  debunk writeup.

## Sources used
[S980] 证券之星(stockstar.com): 南亚新材: 2025年度业绩快报公告 — 2026-02-25, tier 3, fetched.
[S981] 东方财富财富号(caifuhao.eastmoney.com): 南亚新材料科技股份有限公司2025年度业绩快报公告
  — 2026-02-26, tier 3, fetched.
[S982] 腾讯新闻(news.qq.com): 南亚新材（688519）2025年年报简析：营收净利润同比双双增长，应收账款上升
  — 2026-03-27, tier 3, fetched.
[S983] 证券时报网(STCN): 南亚新材股价巨震背后：高增长光环下的财务隐忧 — ~2026-05-14 (date inferred from the
  same-day stock-crash event described in-text; byline date not independently confirmed beyond that), tier 3,
  fetched.
[S984] 同花顺F10(10jqka.com.cn): 南亚新材(688519) 公司资料 — evergreen page, accessed/dated 2026-07-07,
  tier 3, fetched.
[S985] 上海证券报(cnstock.com): 南亚新材料科技股份有限公司关于上海证券交易所2025年年度报告的信息披露监管
  问询函的回复公告 — 2026-05-13, tier 3, fetched.
[S986] 金证研(thejzy.com): 深度｜南亚新材原独董上任两月离职 与客户关系"不一般"业务独立性存疑 — 2020-06-30,
  tier 3, fetched.
[S987] 发现报告(fxbaogao.com): 南亚新材机构调研纪要 — meeting dated 2025-06-27, tier 3, fetched.
[S988] 东方财富股吧(guba.eastmoney.com): 南亚新材作为国内高速覆铜板核心供应商...（投资者互动平台问答relay）
  — posted 2026-04-27, company reply same day, tier 4 (forum — lead only, not load-bearing), fetched.
[S989] 上海证券报(cnstock.com): 南亚新材料科技股份有限公司2025年年度报告摘要 — 2026-03-26, tier 3, fetched.
[S990] 新浪财经AIGC(finance.sina.com.cn): 南亚新材2025年业绩大增377% 高速材料量产成核心引擎 光大证券出具
  核查意见 — 2026-05-12, tier 3, fetched.
[S991] 搜狐(m.sohu.com): 南亚新材2025年业绩大增377% 高速材料量产成核心引擎 光大证券出具核查意见（同一核查
  意见的独立relay）— 2026-05-12, tier 3, fetched.
[S992] 财联社(cls.cn): 【公告全知道】存储芯片+PCB+光通信+算力！公司AI算力覆铜板供货沪电股份、胜宏科技
  — 2026-05-11, tier 3, fetched.
[S993] 新浪财经(finance.sina.com.cn): 南亚新材拟定增不超9亿扩产覆铜板 抢抓算力基建机遇净利连续7季增长
  — 2025-12-24, tier 3, fetched.
[S994] 东方财富财富号(caifuhao.eastmoney.com): 南亚新材(688519.SH)发布一季度业绩，归母净利润1.5亿元，同比
  增长610.83% — 2026-04-28, tier 3, fetched.
[S995] 新浪财经(finance.sina.com.cn): 产品量价齐升 南亚新材2025年营收、净利润高增长 — 2026-03-27, tier 3,
  fetched.
[S996] 新浪财经(finance.sina.com.cn): 南亚新材料科技股份有限公司2026年第一季度报告（relay，含2025年度权益
  分派实施公告）— 2026-04-28, tier 3, fetched.
