Timzhao0205/PhD_Career_Portfolio/03_Investments_and_Finance/02_Ascend_Benchmark_Mission_2026-07/30_PHASE3_VALUATION_SCORING/FR_002916.md

Educational benchmark for a paper-trading learning exercise. Simulated allocations, not investment advice or recommendations.

# FR_002916 — 深南电路 Shennan Circuits — Final Review (critical-reviewer, 2026-07-07)

Inputs: V_002916.md, F_002916.md, VAL_002916.md, SCORES.csv row (total_v1=1.80, W 1/0/4/0/4/4),
SCORING_RUBRIC.md, SOURCE_STANDARDS.md. No REDTEAM_ file exists for this name. Fetch budget
used: 2/2 ([S1194] FY2025 annual-report HTML preview; [S1195] re-fetch of the S191 F10 page).

## 1. Evidence adjudication — RULING: CONFIRM tier C (headline Ascend-specific claim)

V_002916's two-tier split is correct and well-evidenced: generic-Huawei relationship = tier A
but historic and non-AI (2011 own-website award [S199]; 2020 base-station-PCB reply [S200];
IPO-era 16.5–29.1% Huawei share is snippet-only, correctly non-load-bearing [S203]); the
operative "current AI/Ascend systems" claim = tier C, resting solely on forum/self-media
repetition, with the one fetched specimen [S201] confirmed uncited on inspection. This review's
independent hunt for a W1-moving FY2025/2026 company statement found none: two zh-language
searches surfaced only Tier-4 echoes (a search-synthesis line "为昇腾芯片提供封装基板" traces to
caifuhao/zhihu columns, not to any filing or reply — classic echo-chain, correctly NOT counted
as independent corroboration in V), and a direct fetch of the FY2025 annual report (HTML preview,
[S1194]) shows no occurrence of 华为 or 昇腾 in the visible text — AI-server demand appears only
generically ("AI服务器及相关配套产品需求加速释放，订单同比显著增加，成为PCB业务增长的关键动力"),
unquantified, customer-anonymous. The company's own IR pattern (declines to confirm Nvidia/AMD,
declines an AI-share number, 2026-01/02/06 [S192]) is non-disclosure, not substantiation — V
treated it exactly that way. The exposure method does NOT assume the rumor: the 7.46% figure is
a customer-agnostic arithmetic ceiling on ANY single customer [S191], explicitly labeled "not a
Huawei-specific estimate." Cross-group consistency (read-only check): 002436 got the identical
anonymized-rank ceiling → NOT-ESTIMABLE treatment; 688519's filing names its top-5 (all PCB
fabs, 深南电路 itself among them, no Huawei) → segment-ratio ceiling, NOT-ESTIMABLE. No tiering
inconsistency across the A20 boards/substrate/laminate group. Not 0/UNVERIFIED: tier-C
assertions exist and the historic tier-A generic link is real; rubric "1 = tier C only" fits.

## 2. Figure verification (3 score-driving figures; 2 fetches spent)

| Figure | File | Source | Result |
|---|---|---|---|
| FY2025 top-5 customers = 18.42% (CNY 4.356bn); #1 = 7.46% (17.65亿); #2–5 = 3.08/2.93/2.52/2.43%; anonymized by rank; top-5 suppliers 30.08% | V/F/VAL (drives W2 ceiling, W6, PFP narrative) | [S191] basic.10jqka.com.cn/002916/operate.html, re-fetched 2026-07-07 [S1195] | CONFIRMED — all six percentages + 43.56亿/17.65亿 amounts match exactly; components sum to 18.42; 18.42%×23,647M=4,356M and 7.46%×23,647M=1,764M check. (Fetch summarizer mislabeled prior-year rows; FY2025 row unambiguous.) |
| FY2025 revenue CNY 23,646.98M / NP attrib. CNY 3,275.74M (+74.47%) | F/VAL (P/E, P/S denominators, W3) | [S475]+[S190] | CONFIRMED in-file — F's 8-point cross-validation matches AR-summary mirror to the yuan; [S1194] preview consistent (no contradiction); no fetch spent. |
| Price 412.10 / mktcap CNY 280,708.75M, 2026-07-07 close | VAL (W4 multiples) | [S642]+[S643] | CONFIRMED by arithmetic identity — 412.10×681,166,595 = 280,708,753,799.5 recomputed here; two independent vendors agree to the yuan; same-day quote, re-fetch not warranted within budget. |

## 3. Implied-expectations re-derivation

Independent re-derivation from VAL inputs: TTM NP = 3,275.7382 − 491 + 850 = CNY 3,634.74M →
P/E = 280,708.75/3,634.74 = **77.23x** (matches vendor rolling-P/E field independently); TTM
rev = 23,646.9771 − 4,783 + 6,596 = CNY 25,459.98M → P/S = **11.03x**; static P/E 85.69x —
all reproduce VAL exactly. Reverse check: at flat price, de-rating to even a premium-hardware
25x in 5 years needs ~25%/yr NP CAGR ((77.23/25)^(1/5)=1.253); to a market-ish 15x, ~39%/yr —
on a capital-intensive, net-debt name whose Q1-2026 FCF was deeply negative (OCF 247M vs capex
1,989M [S482]). **PFP flag: AGREE.** One dispute, scored in W4 below: VAL's clause "on tier-C
evidence" conflates the Ascend-specific attribution (tier C) with evidence of growth per se —
delivered growth is tier-1-verified and the FY2025 AR itself (tier-1 text, [S1194]) names
AI-server demand as the key PCB growth driver. The perfection priced is only PARTLY rumor-grade.

## 4. Rescore (v1 → v2)

| Cell | v1 | v2 | Justification (one line) |
|---|---|---|---|
| W1 | 1 | 1 | Confirmed: Ascend link tier C only (V_002916 §Tier; this review's hunt [S1194] + 2 searches found no 2025/26 filing/reply naming 华为/昇腾). |
| W2 | 0 | 0 | Confirmed NOT-ESTIMABLE (V_002916 §Exposure): 7.46% is a customer-agnostic direct-sales ceiling, not an estimate; indirect/EMS channels unbounded; rubric scores unsupported cells 0. |
| W3 | 4 | 4 | Confirmed (F_002916): rev +32%/+32%, GM 23.4→28.3%, OCF up 3 yrs = 5-anchor traits, but net DEBT all 3 yrs (widening, [S472]) and thin/negative FCF in capex cycle bar a 5. |
| W4 | 0 | 1 | UPGRADED: PFP confirmed (77.23x/11.03x re-derived, VAL_002916) but not "on tier-C evidence" — growth evidence is tier-1 (delivered +74.47% NP [S475]; AR names AI-server orders as key driver [S1194]); only Ascend attribution is tier C, already zero-scored in W1/W2 — 0 double-counts; rubric 1 = PFP. |
| W5 | 4 | 4 | Confirmed (F segment table; RB_02 read #2 "component makers (optics/PCB/cooling) get technical moats + content growth"): FC-BGA substrate ramp [S196] + 35.5%-GM AI-grade PCB earn >3; 13% commoditized PCBA leg + crowded domestic PCB field bar the 5-anchor. |
| W6 | 4 | 4 | Confirmed: diversification is disclosed-data-verified, now re-fetched (top-5 18.42%, #1 7.46% [S191, S1195]) and cuts FOR this cell even while cutting against W1/W2; policy common-mode with the China-AI complex is not low (Thailand hedge [S196]) → not 5; no concentration, no internalization precedent → not 3. |

**total_v2 = 1(.20)+0+4(.60)+1(.20)+4(.60)+4(.40) = 0.20+0+0.60+0.20+0.60+0.40 = 2.00** (v1 1.80).

## 5. Verdict

total_v2 = **2.00** (Δ = +0.20). Already in top 8 at v1 (rank 7), so no new top-8 entry.
**RE-REDTEAM: NO** (|2.00 − 1.80| = 0.20 < 0.5).

## New sources this review (ledgered in 90_BIBLIOGRAPHY/frags/fr_002916.json)

- [S1194] fxbaogao.com HTML preview of 深南电路 2025年年度报告 (full-AR text, preview scope),
  fetched 2026-07-07 — no 华为/昇腾 in visible text; AI-server-as-key-driver quote.
- [S1195] basic.10jqka.com.cn/002916/operate.html re-fetch 2026-07-07 — verification event for
  [S191]'s FY2025 customer/supplier concentration figures (exact match).
