Timzhao0205/PhD_Career_Portfolio/03_Investments_and_Finance/02_Ascend_Benchmark_Mission_2026-07/30_PHASE3_VALUATION_SCORING/FR_301236.md

Educational benchmark for a paper-trading learning exercise. Simulated allocations, not investment advice or recommendations.

# FR_301236 — 软通动力 iSoftStone (301236.SZ) — Critical Review (patch backstop), 2026-07-07

Inputs: V_301236.md, F_301236.md, VAL_301236.md, SCORES.csv row (post-redteam 4,1,1,1,1,1 = 1.60),
REDTEAM_301236.md + REDTEAM_RESPONSES.md R4 (settled cells re-adjudicated on merits, not deferred to),
SCORING_RUBRIC.md, SOURCE_STANDARDS.md, R0.1/R0.2 adjudicated standards, FR_688519 (patch precedent).
Fetch budget 2/2 used: [S1202] cninfo full-text-search API (located the abstract on the tier-1 platform);
[S1203] FY2025 年度报告摘要 parsed DIRECTLY from static.cninfo.com.cn via r.jina.ai render — the first
successful tier-1 parse of ANY 301236 filing this mission (Phase 1 went 0/10 on this filer's WPS PDFs).
New sources: 90_BIBLIOGRAPHY/frags/fr_301236.json (S1202–S1203, verified:"fetched"); S1204–S1205 unused.

## 1. Evidence adjudication — ruling: CONFIRM (Tier A; relay fidelity now tier-1-proven; W1 cap at 4 affirmed)

V_301236's Tier A was the mission's riskiest A — reached with zero direct tier-1 parses, i.e. maximally
exposed to the echo-chain failure mode. This review's direct parse of the FY2025 abstract [S1203]
retroactively validates the relay chain rather than impeaching it: revenue 35,089,898,380.66 (+12.05%),
归母NP 206,113,321.54 (+14.27%), 扣非 41,926,345.76 (−42.14%), OCF −242,025,480.33, and the segment split
all match the [S295;S301;S303;S509;S515]-carried figures to the yuan, and 昇腾/鲲鹏/鸿蒙 appear in the
company's own abstract text — the v1 relays were faithful carriers of DISTINCT underlying documents
(IPO prospectus, SZSE inquiry reply, dated 互动易 replies, Huawei's own partner page), not one story
re-echoed. The other two checklist failure modes are present in the record and were correctly contained:
(i) the company's own post-IPO language names a customer CATEGORY, never Huawei ("通讯设备行业主要客户
（客户A）" [S304]), and the FY2025 25.42% top customer is unnamed — grep-verified that every citation
(V §F + Exposure §2, REDTEAM B4/C6, R4.6, SCORING_NOTES W6 line) treats identity as A8-unconfirmed;
no file equates 25.42% with Huawei; (ii) the exposure method does not assume the rumor under test — v1
explicitly REFUSED to count the 45.05% segment as Ascend exposure (it bundles the non-Huawei x86 机械革命
ODM) and disclaimed its own 19% floor as a 2022-mix extrapolation. Tier A stands. The W1=4 cap also
stands: the residuals are now identical in kind to post-upgrade 688519 (direct tier-1 platform-word
naming, but Huawei-as-current-customer unconfirmed and the 双优选/HC2025 partner-grade items still
relay-carried [S301;S012]) — a 5 would break the adjudicated ladder (verbatim direct-business filing = 5;
relay-capped or identity-gapped A-substance = 4; brand-word-absent = 3; per R4.1 and FR_688519 §4).

## 2. Figure verification (3 load-bearing figures + 2 free arithmetic checks; both fetches spent on #1–#2)

| Figure | File | Cited source | Verdict |
|---|---|---|---|
| FY2025 revenue 350.90亿/+12.05%; 归母NP 206.11M/+14.27%; 扣非 41.93M/−42.14%; OCF −242.03M | V §A; F table; VAL | [S295;S301;S303;S509;S515] | **CONFIRMED at tier 1 to the yuan** [S1203]: 35,089,898,380.66 / 206,113,321.54 / 41,926,345.76 / −242,025,480.33, growth rates exact |
| 计算产品与智能电子 158.09亿 = 45.05% of revenue, +22.36% YoY (exposure ceiling; margin-mix driver) | V Exposure §1; F segment table | [S295;S301;S303] | **CONFIRMED at tier 1** [S1203]. Minor: software share renders 54.03% vs relays' 54.02% — sub-rounding variance on a non-load-bearing line; tier-1 figure preferred (SOURCE_STANDARDS rule 5) |
| Largest customer 25.42% (FY2025, unnamed) | V §F; W6 cell | [S296] | **CONFIRMED at relay grade only** — not in the abstract's rendered text [S1203]; rests on one clean P1 fetch + [S728]'s adjacent-year 25.38% (FY2024) pattern; tier-1 check UNREACHABLE within budget (table lives in the full AR, unparseable filer) |
| Price 37.58 / mktcap 38,902.41M (2026-07-07 close) | VAL §Quote | [S663;S664] | **CONFIRMED by re-arithmetic** — 37.58 × 1,035,189,280 = 38,902,413,142.40 exact, dual-vendor match; no fetch needed |
| W2 proven-minimum inputs: 4.27亿 中国移动 推理型 中标 + 千万级 矿鸿 | REDTEAM §0.6; R4.2 | [S729;S300] | **CONFIRMED as ledgered** — both fetched 2026-07-07 this mission; Ascend attribution corroborated by [S726] ("AI服务器核心芯片采用华为昇腾…Atlas加速卡") and the company's own 互动易 [S300]; no re-fetch spent |

## 3. Implied-expectations re-derivation (independent arithmetic)

Mktcap 37.58 × 1,035,189,280 = 38,902.41M ✓. P/E FY2025 = 38,902.41 ÷ 206.113 = 188.74× ✓. TTM NP =
206.113 − 350.00 + 198.00 = +54.11M → P/E ttm = 718.9× ✓ (gtimg's own 721.61 field within 0.4%); VAL's
order-of-magnitude-only fragility caveat is correct and material. P/S ttm = 38,902.41 ÷ (35,089.90 +
8,117.00 − 7,010.70 = 36,196.20) = 1.075× ✓. Red-team extensions also reproduce: core (扣非) TTM = 41.93
− 360.0 + 216.0 = **−102.07M, a trailing core loss** [S303;S724]; FY2025-core P/E = 38,902.41 ÷ 41.93 =
927.8×; bull-consensus forward = 38,902.41 ÷ (206.11 × 1.5057 = 310.34) = 125.4× [S731]. No arithmetic or
assumption disputed. **Flag re-derived: PRICED-FOR-PERFECTION — AGREE.** Patch W4-anchor-note ruling
(tier binds to the growth NARRATIVE the price embeds): the only narrative a 719×-headline/negative-core
multiple at 1.07× sales can be pricing is Huawei-ecosystem hardware/AI-to-PROFIT conversion — nothing
else in the mix could carry it (services = repricing-squeezed IT outsourcing, GM 21.97→16.5% [S726;S304];
the x86 ODM leg is commodity consumer hardware). That narrative's carriers are the company's own filing
(segment +22.36%, AI-related revenue 52.6%, 昇腾/鲲鹏/鸿蒙 named — tier A substance, now tier-1-direct
[S1203]) and 7-house named sell-side consensus (tier B [S731]) — tier ≤B, not C → PFP maps to W4=1, not
0. The profit CONVERSION itself has zero reported evidence in any period (margins, core profit, OCF all
worsened through Q1-2026) — that gap is exactly what the PFP flag prices; it does not re-tier the carrier.

## 4. Rescore (v1 = post-redteam SCORES.csv row; weights .20/.20/.15/.20/.15/.10)

| Cell | v1 | v2 | Justification (one line) |
|---|---|---|---|
| W1 | 4 | 4 | Confirmed EARNED, basis strengthened: tier-1 parse [S1203] cures the relay-only defect on figures and platform naming, but the A8 customer-identity gap and relay-carried 双优选/HC2025 grade hold it below 5, mirroring post-upgrade 688519=4 (V_301236; R4.1; FR_688519) |
| W2 | 1 | 1 | Confirmed under R0.1 bullet 2: attributed component sum 4.27亿 + 千万级 ≈1.2–1.5% of tier-1-confirmed revenue is a proven minimum and scores its band (<10%) [S729;S300;S726;S1203]; the disclaimed 19–45% band spans two bands and selects nothing — alone it would force 0 exactly as 688519's band-spanning 17.70% ceiling did (FR_688519) — so the 1 is earned by the component sum ONLY, and v1's "NOT-ESTIMABLE clean point" verdict (about the segment-ratio method) is not in conflict with it |
| W3 | 1 | 1 | Confirmed: both anchor-1 prongs literal (GM 19.26→12.46→11.20% [F_301236]; OCF −242.03M tier-1-confirmed [S1203], then −34.42亿 in Q1-2026 alone [S724]); C3 aggravators verified folded (R4.3 logs OCF, first 存货跌价 writedowns [S727], goodwill 3.85× the ttm residual); not 0 — completed 33.48亿 raise [S730], +15.79% revenue, positive headline NP ≠ distress signs |
| W4 | 1 | 1 | Confirmed via the patch anchor note (§3): PFP independently re-derived; the priced narrative (Huawei-ecosystem profit conversion) is carried at tier A/B (own filing [S1203] + named sell-side [S731]) → 1 not 0 per R0.2-as-refined; C4 aggravators (core TTM −102.07M, core-FY 927.8×, forward 125×) verified folded (R4.4) |
| W5 | 1 | 1 | Confirmed: both legs sit at the anchor-1 text (services "IT外包……技术壁垒并不高", GM 21.97→16.5% [S726]; whole-machine integration at 4.82% GM and falling [S303;S304]); the 鸿蒙/ISV overlay still shows zero disclosed revenue [S729]; consistent with the 002261 W5=1 cell (R4.5) |
| W6 | 1 | 1 | Confirmed: material concentration (top-5 47.32%; #1 25.42% A8-unnamed [S296]) AND verticalization exposure (超聚变 whole-machine re-tiering precedent [S721 via REDTEAM]; mid-grade 双优选 [S301]) = both → 1; not 0 because the 0-anchor's single-customer prong fails at 25.42% (cf. 688629's 60.52%→0); C6 aggravators verified logged (R4.6) |

Total_v2 = .20(4) + .20(1) + .15(1) + .20(1) + .15(1) + .10(1) = 0.80 + 0.20 + 0.15 + 0.20 + 0.15 + 0.10 = **1.60**.

## 5. Verdict

**total_v2 = 1.60** (v1 1.60 → v2 1.60; Δ = 0.00). **RE-REDTEAM: NO** (|Δ| < 0.5; no new top-8 entry).
The settled row survives adversarial re-check intact; the one material addition is that this name's
evidence base is no longer 100% relay — [S1203] is its first direct tier-1 artifact this mission, and it
CONFIRMED rather than corrected every figure it touched (a favorable echo-chain audit outcome, and the
reason the Tier-A/W1=4 call is now on firmer ground than when v1 made it).

Sources this review: [S1202] cninfo full-text-search API announcement index (2026-04-25 item); [S1203]
https://static.cninfo.com.cn/finalpage/2026-04-25/1225192661.PDF (软通动力2025年年度报告摘要, parsed via
r.jina.ai render) — both tier 1, accessed 2026-07-07, verified:"fetched", ledgered in frags/fr_301236.json.
