Timzhao0205/PhD_Career_Portfolio/03_Investments_and_Finance/02_Ascend_Benchmark_Mission_2026-07/30_PHASE3_VALUATION_SCORING/FR_688141.md

Educational benchmark for a paper-trading learning exercise. Simulated allocations, not investment advice or recommendations.

# FR_688141 — 杰华特 Joulwatt (688141.SH) — critical review, PP2 accuracy patch

Reviewed 2026-07-07. Inputs: V_688141.md, F_688141.md, VAL_688141.md, SCORING_NOTES_v2.md §1
(baseline 1.70 = v1 column), SCORING_RUBRIC.md, SOURCE_STANDARDS.md; no REDTEAM_ file exists.
Fetch budget: 2/2 WebFetches spent (§2 trail). New sources S1154 (fetched) + S1155 (snippet) in
90_BIBLIOGRAPHY/frags/fr_688141.json. Orchestrator cr_flags (a)/(b) adjudicated in §1.

## §1 Evidence adjudication — ruling: CONFIRM tier B (caveat materially strengthened)

The B rests on one source: 国盛证券 named-analyst 昇腾产业链 deep-dive (2025-05-06) placing
杰华特's DrMOS/multiphase ramp inside its Ascend-chain power section, with V_688141's caveat
(placement, not a stated supply contract) honestly recorded [S924, fetched 2026-07-07 this
mission]. That is source-class tier 3 / evidence tier B by SOURCE_STANDARDS construction, and
chain-membership-by-named-tier-3 is the established B pattern in SCORING_NOTES_v2 §1. Not A
(own FY2025 AR full text is Huawei/Ascend-silent [S920]; no official IR reply names the link);
far above C (named, dated, non-forum). The tier-4 "绑定华为昇腾" blogger claim stays rejected
[S930]. **Flag (b) — substantiated in substance, one fetch spent:** a named-media relay of the
company's own investor-platform replies dated 2025-05-21 — 15 days AFTER S924 — contains zero
mention of 华为/昇腾/Atlas/鲲鹏/海思 and frames the same product family as Intel-platform work
("2024年推出Intel VR14及Intel IMVP9.3平台多相控制器与DrMOS产品，应用覆盖PC/服务器/AI/自动驾驶",
no customer named) [S1154, fetched]. The flag's three cited documents themselves (业绩快报
2026-02-28; IR records 2025-08-12/2025-11-10) stay unverified: the QQ-hosted IR-record PDF is
password-protected (§2 trail). Effect: company voice attributes the server-power ramp to Intel
platforms and never to Ascend, so S924's placement carries no company-side corroboration that
the ramp is Ascend-driven — but silence + Intel framing is not a denial (Intel and Ascend boards
are not mutually exclusive; NDA-silence about Huawei is normal practice, and the 3-year
anonymized ~26–31% #1 customer [S925] is consistent with it). Source class, hence tier B, hence
W1=3, stands; the answer-key narrative must carry the Intel-framing counterweight. **Flag (a) —
discounted, no fetch spent:** the possible 云通大业 rename of the Hubble stake in the 2026-03-31
register is an unverified lead; the ledgered Hubble figure is FY2023-AR-dated [S922] and
V_688141 already weights equity affinity at zero for the tier call ("investment link, not a
customer link"), so register identity, either way, moves no cell. Zero weight applied.

## §2 Figure verification (3 score-driving figures; 2 fetches spent as shown)

| Figure | File | Source | Status |
|---|---|---|---|
| Mktcap CNY 73,366.40M / price 162.92 (2026-07-07 close) → P/S inputs (W4) | VAL_688141 | S1110+S1111 | CONFIRMED — dual-vendor, price×shares=f116 to the yuan; both fetched this mission; no re-fetch needed |
| FY2025 revenue 2,655.02M / 归母净利润 −717.12M (W3, W4 denominators) | F_688141 | S920/S1026/S923 | CONFIRMED — AR-text vs two aggregators reconcile within ¥100 (F_688141 §A); all fetched this mission |
| S924 anchor quote "杰华特DrMOS和多相控制器产品已量产爬坡" in Ascend power section (W1) | V_688141 | S924 | CONFIRMED as ledgered (fetched 2026-07-07 PP1, verbatim quote + no-contract caveat); not independently re-fetched — budget deliberately spent on the S1154 counter-evidence, which tests the same W1 cell harder |

Fetch trail: (1) file.finance.qq.com IR-record PDF (uploaded 2025-09-09) → WebFetch returned
encrypted stream; local Read: "PDF is password-protected" — same signature as V_688141's
cninfo/sina PDF failures; no source id per mission convention. (2) stock.stockstar.com
RB2025052100032041 → fetched OK = S1154. Net-debt −1,814.50M (W3) not re-fetched: component
build from S1023 with F_688141's arithmetic shown line-by-line; accepted on internal check.

## §3 Implied-expectations re-derivation — AGREE: PRICED-FOR-PERFECTION

Independent arithmetic from VAL_ inputs: P/S static = 73,366.40 ÷ 2,655.02 = **27.63x** (matches
VAL_). TTM revenue = 2,655.02 + 765.00 − 528.15 = 2,891.87 → **25.37x** (matches). P/E: FY2025
归母 −717.12M → n/a; static 73,366.40 ÷ (−717.12) = −102.31, matching the vendor field exactly;
TTM NP = −993.12 − Q1-2025NP can only turn positive if Q1-2025 alone lost >993M — vs full-year
FY2023 −531.41M / FY2024 −603.37M, sound reasoning, no dispute. EV = 73,366.40 + 1,814.50 =
75,180.90M ✓. Verdict test: 25–28x sales with no profitable period anywhere in the record, OCF
negative 3 straight FYs (−291.43/−360.44/−323.50M), net cash +632.25M→−1,814.50M, and Q1-2026 NM
−36.08% breaking the 3-year margin-improvement trend — nothing about this is NEUTRAL or
SKEPTICALLY-PRICED; the price underwrites a profitability inflection the Phase-2 record has not
begun to show. I additionally endorse VAL_'s sharpest point: the growth being capitalized is not
attributably Ascend-linked (tier B only, NOT-ESTIMABLE exposure), and S1154 (company voice,
Intel-platform framing) strengthens that doubt. Flag PFP on tier-B evidence → W4 anchor 1.

## §4 Rescore (baseline v1 = SCORING_NOTES_v2 §1 → v2)

| Cell | v1 | v2 | Justification (one line) |
|---|---|---|---|
| W1 | 3 | 3 | CONFIRM earned: S924 named-sell-side Ascend-chain placement is genuine tier B (V_688141); new company-voice Intel-framing [S1154] weakens the implication, not the source class; Hubble affinity zero-weighted (stale FY2023 stake [S922]; register lead unverified) |
| W2 | 0 | 0 | CONFIRM earned: NOT-ESTIMABLE → rubric 0 (V_688141: #1 customer 30.04% not equatable per A8; DC-DC 53.29% not server-specific); S1154 reinforces — even a server slice cannot be Ascend-attributed when company voice frames it Intel |
| W3 | 1 | 1 | CONFIRM earned: persistent cash burn re-verified (OCF < 0 all 3 FYs, net debt −1,814.50M, Q1-26 NM −36.08% trend break; F_688141); not 0 — no going-concern/default evidence on file, +58.15% revenue, H-share raise pending [S928 color] |
| W4 | 1 | 1 | CONFIRM earned: PFP independently re-derived in §3 (27.63x/25.37x sales, P/E n/a) on tier-B W1 → anchor 1, not the tier-C 0 (VAL_688141) |
| W5 | 3 | 3 | CONFIRM earned: defensible-but-competitive — real analog/DrMOS barriers with AI content-per-board growth, Intel-platform qualification [S1154] evidences capability, but not on RB_02's premium-layer list and crowded (1.9% global DC-DC share, S928 color) |
| W6 | 3 | 3 | CONFIRM earned: exactly one material concentration (anonymous #1 = 26–31% for 3 straight FYs [S925]); no documented power-stage verticalization/internalization precedent → anchor 3, not 1/0 (F_688141; V_688141) |

total_v2 = 3(.20) + 0(.20) + 1(.15) + 1(.20) + 3(.15) + 3(.10) = 0.60+0+0.15+0.20+0.45+0.30 = **1.70**.

## §5 Verdict

**total_v2 = 1.70** (v1 1.70, Δ = 0.00 < 0.5). **RE-REDTEAM: NO.**

Sources: existing S920–S931, S1020–S1028, S1110–S1111 as cited; new S1154 (fetched), S1155
(snippet, color) in 90_BIBLIOGRAPHY/frags/fr_688141.json.
