Timzhao0205/PhD_Career_Portfolio/03_Investments_and_Finance/02_Ascend_Benchmark_Mission_2026-07/30_PHASE3_VALUATION_SCORING/FR_688519.md

Educational benchmark for a paper-trading learning exercise. Simulated allocations, not investment advice or recommendations.

# FR_688519 — 南亚新材 Nanya New Material (688519.SH) — Critical Review (patch backstop), 2026-07-07

Inputs: V_688519.md, F_688519.md, VAL_688519.md, SCORING_NOTES_v2.md §1 baseline (2.20), SCORING_RUBRIC.md,
SOURCE_STANDARDS.md, REDTEAM_RESPONSES.md R0.1/R0.2 (adjudicated standards). No REDTEAM_ file exists for this name.
Fetch budget: 2/2 used — [S1166] cninfo full-text-search API (located the AR-abstract announcement on the tier-1
platform itself), [S1167] the FY2025 年度报告摘要 PDF parsed DIRECTLY from static.cninfo.com.cn via r.jina.ai render
(13pp; the proven proxy path — this succeeds where all 7 of Phase 1's direct PDF attempts failed). New sources in
90_BIBLIOGRAPHY/frags/fr_688519.json (S1166–S1167, verified:"fetched"); S1168–S1169 unused.

## 1. Evidence adjudication — ruling: UPGRADE (tier B → A on the Ascend-naming claim; W1 3→4 by documented interpolation)

Orchestrator flag (relay-only tier B, 0 direct tier-1 fetches) adjudicated in two parts. (a) The relay-based B was
correct as filed: 上海证券报 is one of the four CSRC-designated statutory disclosure venues and reproduces announcement
full text, so [S989] was the company's own words at one remove; V_688519 rightly logged the fetched PAGE at tier 3
(mirror rule) and capped the evidence letter at B — the same discipline the mission enforced when it capped relay-
carried A-content at W1=4 for 301236 (REDTEAM_RESPONSES C1). (b) The question is now MOOT for the load-bearing quote:
this review parsed the abstract directly from cninfo [S1167] and the 昇腾/海光 sentence is there VERBATIM ("国内客户
推出的大模型及超节点，自主开发昇腾、海光等系列已经实现市场批量交付。公司在国内前述头部客户均已经实现量产导入，其中
M6、M7层级的材料在2025年实现稳定且高质量的量产交付") — character-for-character identical to the [S989] reproduction,
proving the statutory-relay chain faithful. The three dated anchors (IR meeting 2025-06-27 [S987]; AR abstract
2026-03-26, now tier-1-verified [S1167]; Sina AR-vintage relay 2026-03-27 [S995]) are distinct documents, not an echo
chain. Residuals that keep W1 at 4, not 5: the 华为-word itself (NOUYA8U 800G "通过华为等核心头部客户认证" [S995])
is NOT in the 13pp abstract's rendered text and remains relay-carried B-grade (corroborated by the separately-dated
company claim "唯一通过华为认证的内资覆铜板企业" [S987]); and the company's own concurrent inquiry-reply filing shows
the COMMERCIAL chain is one hop indirect — top-5 customers for both products are exclusively PCB fabricators, never
Huawei [S985]. V's negative-finding hygiene is exemplary and re-endorsed: the ">60% of Ascend server material supply"
figure was hunted and debunked, the Nvidia-M9 claim was traced to peer 生益科技 (cross-company conflation), the forum
relay [S988] was quarantined at tier 4, and the exposure method (§3 below) explicitly overstates rather than assuming
the rumor. No failure mode on the checklist (echo chain / category-not-Huawei IR reply / rumor-assuming estimate) fired.

## 2. Figure verification (3 load-bearing figures + 1 arithmetic check; re-fetch budget spent on #1–#2)

| Figure | File | Cited source | Verdict |
|---|---|---|---|
| Own-AR 昇腾/海光 + M6/M7 mass-production sentence (drives W1) | V_688519 §D | [S989] statutory relay | **CONFIRMED verbatim at tier 1** — re-fetched [S1167], exact match; also confirms M6~M8 批量应用于国内头部算力客户, M9 at NPI, M10 launched Q4-2025 |
| FY2025 revenue 5,227.83M / NP attrib 240.33M (+55.52%/+377.60%) (drives W3, P/E, P/S) | F_688519 table | [S1080] Sina statements | **CONFIRMED to the yuan** — [S1167] states 5,227,828,810.43元 / 240,327,620.48元; settles V §A's 378.65%(快报)-vs-377.60%(年报) conflict at tier 1 in favor of 377.60% |
| 高频高速及IC载板 revenue 9.25亿, +80.60% (numerator of the 17.70% W2 ceiling) | V_688519 Exposure; VAL §3 | [S990;S991]+[S985] | **CONFIRMED at relay-convergence only** — not disclosed in the 13pp abstract [S1167], budget exhausted for the full AR; stands on 2 independent relays + statutory-relay growth-rate match + exact internal arithmetic (9.25+42.02=51.27=40.55+10.72亿) |
| Price 338.00 / mktcap 79,490,989,396 (2026-07-07 close) | VAL_688519 §1 | [S1140;S1141] | **CONFIRMED by re-arithmetic** — 338.00 × 235,180,442 = 79,490,989,396 exact, dual-vendor cross-match; no re-fetch needed |

## 3. Implied-expectations re-derivation (independent arithmetic)

TTM NP = 240.3276 − 21.12 + 150.00 = 369.2076M [S1080;S1142;S994] → P/E ttm = 79,490.989 ÷ 369.2076 = **215.30×** ✓;
static FY25 P/E = 79,490.989 ÷ 240.3276 = **330.76×** ✓ (matches gtimg's own field to 2dp — independent corroboration);
P/S = 79,490.989 ÷ 5,227.8288 = **15.21×**, ttm basis 79,490.989 ÷ 6,107.8288 = **13.01×** ✓. All VAL arithmetic
reproduces exactly; no assumption disputed. Against that: GM 11.80%, NM 4.60%, OCF negative in FY2025 (−83.18M) AND
Q1-2026 (−66.13M), first net-debt year, an ACTIVE SSE inquiry into profit/cash divergence, and the only Ascend-plausible
segment capped at ≤17.70% of revenue while bundling Hygon/telecom/memory/generic-AI demand with no disclosed split.
A 215–331× earnings multiple on that base leaves no disappointment room. **Flag re-derived: PRICED-FOR-PERFECTION —
AGREE.** W4 mapping per R0.2: PFP on tier A/B evidence → 1 (tier letter now A/B either way; not C).

## 4. Rescore (baseline v1 = SCORING_NOTES_v2.md §1; weights .20/.20/.15/.20/.15/.10)

| Cell | v1 | v2 | Justification (one line) |
|---|---|---|---|
| W1 | 3 | **4** | UPGRADE earned by this review's direct tier-1 parse of the 昇腾-naming own filing [S1167]; held at 4 not 5 because the commercial chain is one-hop-indirect (top-5 all PCB fabs, own filing [S985]) and the 华为-word NOUYA8U certification stays relay-carried [S995] — consistent with the adjudicated ladder (002261 direct-business verbatim-昇腾 filing = 5; relay-capped 301236 = 4; brand-word-absent 688629 = 3) |
| W2 | 1 | **0** | R0.1 literally applied: the 17.70% ceiling [S990;S991] spans TWO bands (<10% and 10–30%) → "bounds that span multiple bands select no band → NOT-ESTIMABLE → 0"; baseline's "plausibly <10%" is a guess, not a known bound — 300308's W2=1 required a ceiling (9.42%) confining the WHOLE feasible set under 10%, and 688629's W2=5 was a filing-anchored POINT (60.52% triangulated-Huawei customer), not a mapped ceiling; A12's "ceiling/floor mapped to the matching band" requires a unique matching band, absent here; consistent with the 688141/002436/688535 NOT-ESTIMABLE=0 class (V_688519's own bottom line: "point estimate = NOT-ESTIMABLE") |
| W3 | 3 | 3 | Mixed confirmed: GM 4.16→8.65→11.80% rising with revenue +55.5% vs ONE negative-OCF FY (−83.18M) + Q1-26 still −66.13M + receivables +68.59% + SSE inquiry — worse than clean-5, but short of 688629's two-consecutive-negative-FY interpolation to 2 (F_688519; VAL [S1143]) |
| W4 | 1 | 1 | PFP flag independently re-derived (§3: 215.30×/330.76×/15.21× all reproduce); tier A/B → 1 per R0.2, not 0 (VAL_688519) |
| W5 | 3 | 3 | M6/M7-grade qualification is a real barrier (company claims sole full-series domestic 华为-certified CCL maker [S987]) but CCL is a competitive, 生益科技-dominated layer not on RB_02's premium list (V_688519; RB_02) |
| W6 | 3 | 3 | One material concentration: top-5 = 34.96% (max 14.17%), all PCB-fab pass-throughs [S1090], plus China-AI policy common-mode; Huawei verticalizing into laminates implausible (F_688519; V_688519 §C) |

Total_v2 = .20(4) + .20(0) + .15(3) + .20(1) + .15(3) + .10(3) = 0.80 + 0 + 0.45 + 0.20 + 0.45 + 0.30 = **2.20**
(W1 +0.20 and W2 −0.20 exactly offset; each ruling stands on its own evidence, the offset is coincidental).

## 5. Verdict

**total_v2 = 2.20** (v1 2.20 → v2 2.20; Δ = 0.00). **RE-REDTEAM: NO** (|Δ| < 0.5; top-8 entry is the orchestrator's
call — this review's inputs to that call are unchanged totals with a changed cell mix W1 4 / W2 0).

Sources this review: [S1166] http://www.cninfo.com.cn/new/fulltextSearch/full?searchkey=... (cninfo announcement
index, 2026-03-26 item); [S1167] https://static.cninfo.com.cn/finalpage/2026-03-26/1225031377.PDF (2025年年度报告摘要,
parsed via r.jina.ai render) — both tier 1, accessed 2026-07-07, verified:"fetched", ledgered in frags/fr_688519.json.
