Timzhao0205/PhD_Career_Portfolio/03_Investments_and_Finance/02_Ascend_Benchmark_Mission_2026-07/30_PHASE3_VALUATION_SCORING/REDTEAM_688519_v2.md

Educational benchmark for a paper-trading learning exercise. Simulated allocations, not investment advice or recommendations.

# REDTEAM_688519_v2 — 南亚新材 Nanya New Material (688519.SH) — re-red-team, accuracy patch, 2026-07-07

Red-team brief: attack, do not balance. Row under attack (SCORES_v2.csv, cells "final at Gate PG2" pending this
wave): **W1=4, W2=0, W3=3, W4=1, W5=3, W6=3, total 2.20** — a patch addition never previously red-teamed, whose
W1=4 rests on FR_688519's tier-B→A upgrade of the company's own AR-abstract prose, and whose W2 already sits at 0
(NOT-ESTIMABLE). Inputs: V_688519.md, F_688519.md, VAL_688519.md, FR_688519.md, SCORES_v2.csv, SCORING_NOTES_v2.md
§1, 01_MISSION/SCORING_RUBRIC.md, REDTEAM_RESPONSES.md (R0.1/R0.2/R0.3 standards; R1.1/R1.3 precedents). New
sources this session: [S1266]–[S1268], ledgered in 90_BIBLIOGRAPHY/frags/rt2_688519.json (zh-language searches +
fetches, accessed 2026-07-07; S1269–S1273 unused). WebFetch budget 4/4 used; one fetch (10jqka 金安国纪 piece)
returned headline-only and is cited below as snippet, never load-bearing, not ledgered. Headline: **the W1=4 pays
a filing-language premium to marketing grammar — the tier-1-parsed sentence names the customers' customers' chips
(昇腾、海光) in scene-setting prose while the company's own concurrent regulatory filing shows zero end-brand
customers; and the 215–331x price sits on a revenue mix whose FY2025 growth was ~76% commodity-grade CCL in the
middle of an industry-wide price-hike wave the company itself joined with 调价函.** Six challenges below (5 cell
challenges + 1 citation defect); all-accepted delta −0.60.

---

## 1. Strongest bear case (5 bullets)

- **B1 — The tier-1 artifact evidences marketing grammar, not a Huawei business.** Parse the upgraded sentence
  [S1167; verbatim also S989]: "国内客户推出的大模型及超节点，自主开发昇腾、海光等系列已经实现市场批量交付" — the
  subject of 已经实现市场批量交付 is the CUSTOMERS' self-developed chip series (Huawei's Ascend, Hygon's line),
  i.e., scene-setting about the end-market's success, not a Nanya delivery. Nanya's own clauses are "量产导入"
  (design-in/AVL introduction at "前述头部客户" — entities its own SSE-inquiry reply proves are NOT its customers:
  top-5 for BOTH products are exclusively PCB fabricators [S985]) and a grade-level delivery claim ("M6、M7层级的
  材料...量产交付") with no counterparty named in the clause. The word 华为 appears NOWHERE in the 13pp tier-1
  abstract (FR_688519's own finding; frag S1167 title: "未见NOUYA8U/华为字样于渲染文本") — every 华为-naming
  artifact is relay-carried B ([S995] NOUYA8U 认证; [S987] IR superlative), 认证 is a qualification verb carrying
  zero revenue, and V_688519's "Why not A" §4 stands unrepaired: no Huawei-side corroboration of any kind exists
  (contrast 301236's devicepartner page). Naming 昇腾 next to 海光 in AR prose is costless sector marketing in
  2026; it is not evidence of a Huawei business.
- **B2 — ~76% of the growth being paid 215–331x for is commodity-cycle, not AI.** Decomposition from the company's
  own by-grade cut [S990;S991; my arithmetic]: FY2025 revenue increment = 522,782.88 − 336,154.10 = 186,628.78万元;
  普通及无卤、无铅 (ordinary/halogen-free) at 42.02亿, +50.73% → increment ≈141,424万 = **75.8% of all growth**;
  高频高速及IC载板 at 9.25亿, +80.60% → increment ≈41,282万 = **22.1%** (residual ≈2% 其他业务 — buckets sum to
  the exact total, cross-check passes). That 75.8% landed during an industry-wide price wave: "自2025年12月起，
  建滔、南亚新材等主流厂商密集发布调价函，覆铜板价格单周最大涨幅达10%-20%," driven by "铜箔、树脂、电子布等
  原材料成本上行," with "低端的产品涨幅高一些" — the LOW-end grades took the LARGER hikes [S1267, 财联社
  2026-04-12]. The company's own headline framing is 量价齐升 (volume AND price) [S995]. Peer prints confirm
  sector beta, not Nanya alpha: 华正新材 swung from loss to NP 2.77亿 in the same FY2025 [S1268]; pure-commodity
  金安国纪's Q1-2026 profit "+超7倍...覆铜板涨价推动" (headline-grade snippet only, fetch body failed — color).
  Price-driven commodity revenue mean-reverts; a 215.30x ttm / 330.76x static P/E [VAL_688519] does not.
- **B3 — The cash side of the P&L story is regulator-flagged and still deteriorating.** NP +377.60% against OCF
  −83.18M (FY2025) and −66.13M (Q1-2026) — the two most recent reported periods are BOTH cash-negative [S1084;
  S1143]; FCF negative in 2 of 3 FYs (FY2023 −255.1M, FY2025 −316.6M, from OCF−capex [S1084–S1086]); receivables
  +68.59% YoY to 31.98亿 = 61% of revenue [S982;S983;S990]; first net-debt year (−49.50M) with cash down every
  year 536→304M [S1087–S1089]. The SSE's inquiry letter (received 2026-04-22) names five abnormal patterns — 利润
  与经营现金流严重背离、应收账款大幅激增、存货异常暴涨、关联交易显著增加、海外业务毛利率异常偏低 [S983] — two of
  which (inventory surge, related-party growth) appear in NO phase file's scoring narrative. Separately, SSE issued
  a 监管警示 on 2025-09-10 for a buyback-rule violation [S989]. The company is financing its own "boom" by
  extending its balance sheet into a 34.96%-concentrated PCB-fab customer set [S1090].
- **B4 — The moat superlative is contradicted in-channel, and a synchronized capacity wave is aimed at the exact
  segment the re-rating needs.** Company IR claim, 2025-06-27: "唯一通过华为认证的内资覆铜板企业" across all
  dielectric-loss grades [S987] — an unverified self-superlative. Against it: 华正新材's own disclosed full
  "Very low-loss至Extreme low-loss等级的全系列产品布局" targeting AI服务器 [S1268, tier 3], and an unnamed-
  institution channel note (2026-01-20) claiming 华正 "2025年华为相关AI业务占总收入50%," batch-producing M7 for
  昇腾910C AND 950 while "昇腾950:华正新材已批量生产，南亚和翼科技处于测试阶段," with 2026 share expected split
  华正/生益 [S1266, **tier 4 — never load-bearing; used strictly as a same-or-better-grade contradiction probe**].
  Either reading of "南亚" in that note (南亚新材, or Taiwan 南亚塑胶 — the exact confusion V flagged) excludes
  688519 from current 950-generation batch production. 生益科技 holds M6–M10 plus the mainland's only Nvidia-M9
  certification (the mission's own debunk finding [V_688519 §G; S992]); meanwhile 华正 is raising 12亿 for 1,200万
  张/yr high-grade CCL, 金安国纪 13亿 for 4,000万㎡/yr, and Nanya itself 9亿 [S1267;S1268;S993] — three concurrent
  placements building high-grade capacity into the same sockets is the standard setup for the next CCL price war.
- **B5 — Every load-bearing AI attribution beyond "M-grade materials exist and grew" is bundled, relay-carried, or
  absent.** Huawei/Ascend share: NOT-ESTIMABLE, ceiling 17.70% spanning two bands [V_688519] — and that ceiling's
  own numerator (9.25亿) was never tier-1-verified (FR_688519 §2: "CONFIRMED at relay-convergence only"; the 13pp
  abstract does not carry the segment split). The ">60% of Ascend server material supply" rumor was hunted and
  debunked by the mission itself; the Nvidia-M9 claim belongs to peer 生益科技 [V_688519 §G]. Q1-2026's +92.36%
  revenue print has zero AI/Ascend breakout in any fetched source [V_688519 §H]. The M10 flagship is "在海外认证
  过程中" — in OVERSEAS certification [S1267], i.e., the company's own top-grade roadmap points away from the
  Huawei chain. The thesis's quantitative core is one unverified relay number inside an unsplittable bundle
  (昇腾+海光+telecom+DRAM/NAND+generic AI [V_688519 Exposure]).

---

## 2. Score audit — every cell, supported or corrected

Weights .20/.20/.15/.20/.15/.10. Current row 4,0,3,1,3,3 = 2.20 (arithmetic verified).

| Cell | Current | Supported by cited files? | Red-team proposal | Δ |
|---|---|---|---|---|
| W1 | 4 | **NO** — the tier-1 parse cures 1 of V's 4 stated reasons for tier B; ladder inversion vs 688629/301236 | **3** | −0.20 |
| W2 | 0 | **YES** — R0.1 correctly applied; ceiling spans <10% and 10–30% bands | 0 (hold; verification gap noted) | 0 |
| W3 | 3 | **WEAK** — R1.3 precedent stack met or exceeded; FR ignored the regulator axis | **2** | −0.15 |
| W4 | 1 | **CONTESTED basis** — cycle priced as AI; aggravator unlogged | 1 (conditional 0; aggravator log demanded) | 0 |
| W5 | 3 | **WEAK** — 82% of mix at anchor-1 economics; superlative contradicted; capacity wave incoming | **2** | −0.15 |
| W6 | 3 | **WEAK** — single-ecosystem concentration + receivables amplifier + live AVL substitution = both-adjacent | **2** | −0.10 |

All-accepted total: **1.60**. W1-only concession: 2.00. Every challenge requires a written response per
SCORING_RUBRIC ("Red-team concessions change scores only with a written response in REDTEAM_RESPONSES").

**W1 4→3.** (i) V_688519 ruled tier B for FOUR reasons; FR's tier-1 parse [S1167] repairs only reason 1
(relay-not-fetched). Reasons 2–4 survive intact: no quantification anywhere; the company's own customer table
names zero Huawei entity (top-5 both products all PCB fabs [S985]); no Huawei-side confirmation exists. R1.1's
adjudicated principle — "interpolating above the verifying file's own tier was inconsistent" — applies: the
surviving substance is B, and B maps to 3. (ii) What the tier-1 sentence evidences is category-different from the
5-anchor's "names the business": 002261's filing named ITS OWN Huawei business (direct commercial relationship,
quantified segment); 688519's abstract names OTHER companies' chips (昇腾 bundled with non-Huawei 海光 in the same
breath) plus its own counterparty-unnamed, grade-level delivery — a design-in claim, not a business. (iii) Ladder
inversion: 688629 holds W1=3 with a triangulated 60.52% DIRECT Huawei-corroborated customer but brand-word-absent
filings; 301236 holds 4 with relay-carried A-substance PLUS Huawei-side partner-list corroboration. 688519 has
neither the commercial relationship nor the Huawei-side corroboration — only the brand word in promotional prose.
If prose-without-relationship (688519) outranks relationship-without-prose (688629), W1 is measuring marketing,
not evidence. (iv) The residual 华为-naming legs are relay-B [S995] and a self-superlative [S987] now contradicted
by same-or-lower-tier channel data [S1266] — under SOURCE_STANDARDS neither leg can carry the extra notch. Propose
**3**.

**W2 0 — CONFIRMED.** R0.1 literally applied; consistent with the 688141/002436/688535 NOT-ESTIMABLE class and
V's own bottom line. One audit note for the record: the 17.70% ceiling's numerator (9.25亿) remains sub-tier-1
(FR §2 row 3) — any FUTURE W2 upgrade must first tier-1-verify that figure from the full AR, and the new [S1267]
datum that M10 is in overseas certification argues the bundle's Huawei-specific fraction shrinks at the top grade.

**W3 3→2.** R1.3 (688629, ACCEPTED 3→2) is the controlling precedent: "persistent cash burn element genuinely
present alongside rising margins → interpolation 2," on facts of two negative-OCF FYs + receivables 45.13% of
revenue + one in-window core-loss year. 688519 meets or exceeds that stack on four of five axes: OCF negative in
the two most recent REPORTED periods (FY2025 −83.18M + Q1-2026 −66.13M [S1084;S1143]) and FCF negative 2 of 3 FYs
(−255.1M/−316.6M [S1084–S1086]); receivables 61% of revenue vs 688629's 45.13% [S983]; a HEADLINE loss year inside
the window (FY2023 NM −4.34% [S1082]) vs 688629's core-loss year; PLUS two regulator actions 688629 never had — an
ACTIVE SSE inquiry letter into exactly this dimension (profit/cash divergence, receivables, 存货异常暴涨, related-
party growth, abnormally low 8.11% overseas GM [S983;S982]) and a 2025-09-10 监管警示 on buyback conduct [S989].
FR's hold-at-3 reasoning counts only the consecutive-FY-OCF axis and is silent on the inquiry's inventory/related-
party prongs and the 监管警示 entirely. Rising GM (4.16→11.80%) is real but was equally real for 688629 (whose GM
also rose into its 2). Propose **2**.

**W4 — challenge on the basis; expected disposition REBUT per R0.2; aggravator log demanded, conditional 0.**
Under R0.2 the 0/1 boundary keys on the link tier letter (A/B→1), so 1 survives even if W1 falls to 3/B. But the
FR_002916/FR_002156 practice reads the tier of the PRICED NARRATIVE, and here the priced narrative — "AI materials
hypergrowth with margin re-rating" — has no tier-≤B carrier for its majority component: 75.8% of FY2025 growth was
ordinary-grade CCL riding an industry price wave the company itself joined ([S1267]; B2 decomposition), the
AI-plausible bucket is a relay-carried 22.1% of growth bundling four non-Huawei demand sources [V_688519], and no
source splits price from volume. If the orchestrator holds 1, the answer key must log the aggravator (as done for
688629 R1.4, 002261 C5, 301236 C4): **a 215.30x/330.76x/15.21x structure [VAL_688519] where three-quarters of the
underlying growth is commodity-cycle is PFP squared — peak-ish cyclical earnings times a perfection multiple.**
If the orchestrator instead finds the priced narrative's carrier sub-B on the majority component, R0.2's own logic
yields 0. Formal proposal: hold 1 + mandatory log; conditional 0.

**W5 3→2 (documented interpolation).** The cell's "defensible but competitive" reading prices the 17.7% sliver and
ignores that 82% of product revenue (普通及无卤 42.02亿 of 51.27亿 [S990;S991]) sits in anchor-1 economics:
demonstrated trough GM 4.16% (FY2023), blended GM still 11.80%, overseas GM 8.11% that the SSE itself called
异常偏低 [S982;S983]. The layer is squeezed from both sides — supplier top-5 concentration 55.34% and rising
(copper foil/glass/resin, the cost-push driver of the current hikes [S1090;S1267]) against a 34.96% PCB-fab
customer block [S1090]. Inside the defensible sliver, the within-layer position discount (the adjudicated 002281/
300308-W5 method) applies: 生益科技 owns the grade ladder's top (M6–M10, sole mainland Nvidia-M9 [V_688519 §G]),
华正新材 discloses a full VLL–ELL series aimed at AI servers [S1268], channel data (tier 4, probe only) puts Nanya
at testing-stage for the 950 generation [S1266], and three simultaneous placements (12亿+13亿+9亿) are building
high-grade capacity into the same sockets [S1267;S1268;S993]. A company one down-cycle removed from a 4% gross
margin, whose premium-grade uniqueness claim is contradicted in-channel, is not "defensible" at 3 — it is
commodity-with-an-option. Propose **2**.

**W6 3→2 (documented interpolation).** The current 3 reads "one material concentration" and stops. Three
compounding facts argue both-adjacent: (i) the concentration is single-ECOSYSTEM, not merely single-list — all
top-5 (34.96%, max 14.17% [S1090]) plus the broader 8–9 named relationships [S985;S992] are PCB fabs pressing the
same domestic AI/server boards, so one end-demand decision moves the entire customer set at once; (ii) the
receivables amplifier — 61% of revenue in receivables, top-5 debtors 51.93% of sales-inclusive receivables
[S983;S985] — converts any demand shock into a simultaneous collection/impairment shock (the demand whipsaw
already fired once in the record: FY2023 revenue −21.05%, GM 4.16% [S1082]); (iii) substitution-at-the-AVL is the
materials-layer functional equivalent of verticalization: Huawei runs material qualification directly with CCL
makers even though invoices flow through the fabs (V_688519 §D gloss), so the end-brand can re-tier suppliers at
zero switching cost — and 生益/华正/台耀-class alternatives at or above Nanya's grade exist now
[S992;S1266;S1268]. The 超聚变 re-tiering precedent (002261's C4) shows Huawei-ecosystem re-tiering is a
demonstrated behavior, not a hypothesis. Concentration + live substitution exposure lands between "one" (3) and
"both" (1). Propose **2**.

**Citation defect (challenge 6, R0.4 class).** SCORES_v2.csv W1 cell_sources reads "own-filing 昇腾/超节点+华为
认证 language tier-1-verified via direct cninfo parse S1166 -> 4". Two defects: (a) **the 华为认证 language was
NOT tier-1-verified** — FR_688519 §1 states the opposite ("the 华为-word itself...is NOT in the 13pp abstract's
rendered text and remains relay-carried B-grade"; frag S1167: "未见NOUYA8U/华为字样于渲染文本"); (b) the parse
artifact is **S1167**, not S1166 (S1166 is the cninfo search-index page). The load-bearing cell of the row's
highest-weighted upgraded score misstates both what was verified and where. Correct the string regardless of the
W1 disposition.

---

## 3. Verticalization test

Huawei internalizing CCL manufacture is implausible on its face — laminate is fine-chemistry batch production over
copper-foil/glass-fabric/resin supply chains with thin unit economics, nothing like the silicon-adjacent HBM
packaging Huawei chose to internalize — but that observation, which is what the current W6=3 rests on, answers the
wrong question. The in-house-HBM precedent's adjudicated meaning (R0.3) is demonstrated APPETITE to control choke
points, and Huawei's revealed method at the materials layer is cheaper than ownership: it runs qualification
directly with laminate makers while buying through PCB fabs [V_688519 §D], which means it owns the approved-vendor
list without owning a single reactor. Every additional supplier qualified at M6/M7 converts Nanya's "barrier" into
a bid list one line longer: 生益科技 already spans M6–M10 with the mainland's only Nvidia-M9 certification
[V_688519 §G; S992]; 华正新材 discloses a full VLL–ELL portfolio aimed at AI servers and is raising 12亿 for
1,200万张/yr of high-grade capacity [S1268;S1267]; channel data — tier 4, probe not proof — already describes 华正
in batch production for 昇腾910C/950 with "南亚...处于测试阶段" at 950 and 2026 share split between 华正 and 生益
[S1266]. If that picture is even half right, the displacement scenario is not a future risk but a running process:
Nanya's verified position (M6/M7 mass delivery in FY2025 [S1167]) describes the LAST generation's sockets, while
the NEXT generation's AVL is being contested by two larger-portfolio rivals — and Nanya's own top-grade M10 is off
chasing 海外认证 [S1267]. The thesis then degrades without Huawei lifting a finger: the fabs (Nanya's actual
customers, themselves squeezed on Huawei board pricing) dual-source at Huawei's direction, high-grade capacity
from three concurrent placements lands into the same sockets, and the 17.70%-ceiling segment reprices toward the
commodity 82% — at which point the 215–331x multiple has no defensible sliver left to capitalize.

---

## 4. Common-mode test

**Huawei/domestic-AI demand shock (shared with the whole Ascend universe).** A cut in Ascend server/board volume
transmits to 688519 through ALL top-5 customers simultaneously — they are the PCB fabs pressing those boards
[S985;S1090] — and then a second time through the balance sheet, because 61% of revenue sits in receivables owed
substantially by those same fabs (top-5 debtors 51.93% [S983;S985]). Note the intra-portfolio wire: 深南电路
(002916), a universe name, is simultaneously one of Nanya's top-5 customers for both products [S985] — a Huawei
board-order shock to 002916 mechanically hits 688519's revenue AND its collection risk in the same quarter. The
FY2023 record (−21.05% revenue, 4.16% GM, headline loss [S1082]) is the observed impulse response.
**Policy reversal (US export relaxation / Nvidia return).** If H20/B-class supply to China hyperscalers resumes at
scale, domestic-chain urgency drops across every name in this universe; 688519's variant is asymmetric — its
disclosed compute exposure is domestic-chain (昇腾/海光/国产GPU [S1167;S987]) while the Nvidia-chain CCL slots are
held by 生益 (sole mainland M9 cert [V_688519 §G]) — i.e., in a reversal the layer's demand doesn't just shrink,
it migrates to the competitor.
**Commodity-CCL cycle reversal (688519-specific within the portfolio, shared with its own customer 002916 in
inverse).** The 2025-12→2026 hike wave (Nanya's own 调价函; cost-push copper/resin/glass [S1267]) mean-reverts
when the announced capacity lands (12亿/13亿/9亿 placements, 建滔 expansion [S1267;S1268;S993]); 75.8% of FY2025
growth rode that wave (B2). Note the sign flip: CCL price cuts would RELIEVE 002916's COGS while gutting 688519's
P&L — the two names are cycle-adversaries inside the same layer group.
**Valuation common-mode.** At 215.30x ttm the name sits in the same PFP cohort as the rest of the board [VAL_688519];
one bad Ascend datapoint de-rates the cohort together, and the highest multiples on the thinnest cash conversion
(OCF negative two consecutive periods) have the furthest to fall.

---

## 5. Five falsifiable checks

1. **H1-2026 interim report (due by 2026-08-31): OCF and receivables ratio.** OCF still negative (third
   consecutive reported period) or receivables ≥55% of ttm revenue → BEAR (cash-conversion structural, W3
   challenge vindicated); OCF positive with receivables ratio falling → BULL (growth-financing artifact, FR's
   hold-at-3 vindicated).
2. **昇腾950-generation CCL sourcing, any tier-≤B artifact by 2026-12-31** (华正新材 placement-review replies or
   AR/interim; Nanya IR or filing; named-analyst note): 华正/生益 confirmed in 950-class mass production while
   Nanya remains unnamed or testing-stage → BEAR (S1266's tier-C picture verified, W1/W5/W6 challenges
   vindicated); Nanya's OWN filing confirms 950-class mass delivery → BULL (uniqueness narrative survives a
   generation change).
3. **CCL price-letter cadence through 2027-03-31** (建滔/南亚 调价函 flow via 财联社/中国覆铜板信息网): first
   DOWNWARD adjustment or a two-quarter halt in hikes while the placement capacity ramps → BEAR (cycle peaked;
   the 75.8%-commodity growth engine reverses under a 215x multiple); hikes hold through capacity landing →
   BULL (structural shortage, not a wave).
4. **SSE follow-through by 2026-12-31**: a second inquiry letter, 监管措施, or FY2026 audit qualification touching
   receivables/inventory/related-party items → BEAR (W3=2 was still generous); clean FY2026 opinion, no further
   letters, and disclosed collection ratios at or above the ~86% level the company claimed in its reply (claim
   known only from search snippet — itself a verification target) → BULL.
5. **The 9亿 定增 resolution by 2027-06-30** [S993]: approval + full subscription at-or-near market price → BULL
   (institutions underwrite the story with new money); withdrawal, lapse, undersubscription, or deep-discount
   pricing → BEAR (the marginal informed buyer refuses 215x). Secondary marker on the same date: M9 confirmed in
   mass production in a Nanya filing (BULL) vs still at NPI while 生益 ships M9 (BEAR — roadmap slipping one full
   grade behind).

---

## Search trail (zh-language, per rule 7)

Queries: 「生益科技 华为 昇腾 覆铜板 供应 认证 M6 M7 高速材料」, 「覆铜板 涨价 价格 2026 建滔 生益 产能 周期」,
「华正新材 华为 覆铜板 核心供应商 昇腾 AI业务 2025年 收入占比」, 「南亚新材 股价 跌停 2026年5月 问询函 应收账款
现金流」. Fetched (4/4 budget): [S1266] fxbaogao 华正调研纪要 (parsed); [S1267] cls.cn 覆铜板涨价潮 (parsed);
10jqka 金安国纪 Q1-2026 piece (FAILED — headline only: "利润率追平生益科技：覆铜板涨价推动利润增超7倍，M9突围决定
价值分野," snippet-grade, not ledgered, not load-bearing); [S1268] stcn 华正新材 FY2025/定增 (parsed). Snippet-only
items used as color and so marked: 华正新材 FY2025 NP +384.01% (weeklyonstock title); 建滔 "年内第四次涨价"
(sina title, 2026-05-27). Not found at tier ≤B: any Nanya-specific Huawei revenue figure (consistent with
V_688519 §G's debunk); any independent confirmation OR refutation of the "唯一通过华为认证" superlative — the
claim remains company-voice-only, now with a tier-C counterclaim [S1266], i.e., unusable in either direction.

## Sources this session

[S1266] 发现报告(fxbaogao.com) relay of 未知机构 华正新材调研纪要 (昇腾950 PCB调研) — 2026-01-20, tier 4
  (unnamed-institution channel check — NEVER load-bearing; used solely as a contradiction probe against [S987]
  and as falsifiable-check material), fetched.
[S1267] 财联社(cls.cn): 需求攀升叠加成本上涨 PCB上游覆铜板再现涨价潮 产业链抢滩高端CCL — 2026-04-12, tier 3,
  fetched.
[S1268] 证券时报网(stcn.com): 华正新材2025年实现扭亏为盈 拟定增募资不超12亿元扩大高端覆铜板产能 — 2026-03-23,
  tier 3, fetched.
Full entries: 90_BIBLIOGRAPHY/frags/rt2_688519.json (S1269–S1273 unused). All other [S###] cites reference
entries already ledgered by V_/F_/VAL_/FR_688519.
