Timzhao0205/PhD_Career_Portfolio/03_Investments_and_Finance/02_Ascend_Benchmark_Mission_2026-07/30_PHASE3_VALUATION_SCORING/VAL_002436.md

Educational benchmark for a paper-trading learning exercise. Simulated allocations, not investment advice or recommendations.

# VAL_002436 — 兴森科技 Fastprint, SZSE 002436 — Valuation & Implied Expectations

Valuation only, computed from this session's freshly-fetched quote plus Phase-2/Phase-1 figures
already ledgered under their own [S###]. No ranking, score, or allocation decision appears in this
file (ANSWER-KEY SPOILER BOUNDARY, CLAUDE.md rule 4). All CNY unless stated; "CNY M" = CNY million,
"bn" = CNY billion (1,000 CNY M). **P/E** = market cap / net profit attributable to parent (a proxy
for price ÷ earnings-per-share). **P/S** = market cap / revenue. **TTM** = trailing twelve months,
built here as (most recent full fiscal year) − (same-quarter-prior-year) + (most recent quarter).
**EV/EBITDA** = (market cap + net debt) / earnings before interest, tax, depreciation & amortization.

## Quote (as-of, dual-sourced)

Fetched this session, 2026-07-07, after SZSE's 15:00 CST close — recorded as today's closing quote
per task instruction.

| Field | Primary: gtimg/Tencent [S1120] | Secondary: Eastmoney push2delay API [S1121] | Match? |
|---|---|---|---|
| Price (CNY) | 42.23 | 42.23 (f43=4223÷100) | YES |
| Prev. close (CNY) | 45.29 | 45.29 (f60=4529÷100) | YES |
| Change | -3.06 / -6.76% | not in fetched field set | n/a |
| Open (CNY) | 45.32 | 45.32 (f46=4532÷100) | YES |
| High (CNY) | 45.62 | 45.62 (f44=4562÷100) | YES |
| Low (CNY) | 41.86 | 41.86 (f45=4186÷100) | YES |
| Total shares (总股本) | 1,699,673,563 (raw string idx 73) | 1,699,673,563 (f84) | YES |
| Circulating shares (流通股本) | 1,517,930,431 (raw string idx 72/76) | 1,517,930,431 (f85) | YES |
| Total market cap | 717.77亿 (raw string idx 45) = CNY 71,777,000,000 | CNY 71,777,214,565.49 (f116) | YES (to 亿-rounding) |
| Circulating market cap | 641.02亿 (raw string idx 44) = CNY 64,102,000,000 | CNY 64,102,202,101.13 (f117) | YES (to 亿-rounding) |
| Vendor P/E fields (gtimg raw string) | idx39=497.35 (dynamic/rolling-style); idx53=531.90 (static, FY2025-only) | not in fetched field set | both cross-check exactly against this file's own from-scratch P/E calcs — see Multiples |
| Quote-string timestamp | "20260707161500" → 2026-07-07 16:15:00 CST (Beijing) | f86 unix 1783409640 → 2026-07-07 15:34:00 CST (derived: 1783409640 − 1767225600 [=2026-01-01 00:00:00 UTC] = 16,184,040s = 187d 07:34:00 → day 187 after 2026-01-01 = 2026-07-07; +07:34:00 UTC = 15:34:00 CST) | 41min apart, same trading day, both post-15:00 close — see note |

**Independent recomputation (consistency check — addresses this patch's KNOWN-TRAP instruction,
i.e. the price/open field swap documented in VAL_688629.md):** price × total shares = 42.23 ×
1,699,673,563 = CNY 71,777,214,565.49 — matches eastmoney's f116 to the exact yuan and gtimg's own
717.77亿 field at 亿-level rounding. Price × circulating shares = 42.23 × 1,517,930,431 = CNY
64,102,202,101.13 — matches f117 exactly and gtimg's 641.02亿. **CONSISTENCY CHECK: PASS** — no
price/open swap: both vendors independently agree which field is price (42.23) and which is open
(45.32), and two independently-vendored quote feeds agree on price/prev-close/open/high/low to the
fen, on both market-cap bases to the yuan, and (see Multiples) on two separately-computed P/E
ratios to the basis point. Only the internal "as-of" timestamp field differs, by 41 minutes,
between vendors (gtimg 16:15:00 vs. eastmoney-derived 15:34:00) — both are the same calendar day
and post-close, a known vendor-snapshot-lag artifact per task instruction, disclosed here rather
than treated as a discrepancy. Today's -6.76% move (open 45.32, high 45.62, low 41.86, close
42.23, prev-close 45.29) is an internally coherent single-day range; no cause for the move is
asserted here (would require a source not fetched this session — V_002436.md separately documents
that this ticker triggered a mandatory SZSE abnormal-trading disclosure after a >20% 3-day RALLY
on 2026-06-15/17 [S954;S955], so a sharp pullback is plausible but not confirmed as the cause of
today's specific move).

**Headline figures used below:** Price = **CNY 42.23** (2026-07-07, ~15:34–16:15 CST, post-close).
Total market cap = **CNY 71,777.21 M = CNY 71.78 bn** (total-share-capital basis, i.e., 总股本
1,699,673,563 shares — consistent with this mission's convention elsewhere). Circulating-basis
market cap (CNY 64.10bn) shown for context only, not used in the ratios below.

## Multiples

Denominators are Phase-2 figures from `20_PHASE2_FUNDAMENTALS/F_002436.md`, cited to the exact
[S###] that file itself uses (FY2025 revenue/net profit attributable to parent from [S940;S1040],
both cross-validated to the yuan in F_002436.md's own cross-validation section against a
structurally different source, 10jqka [S1049]). Q1 2025 revenue/net-profit are [S940]'s own
quarterly breakdown (already P1-verified, not re-fetched this session). Q1 2026 revenue/net-profit
are [S1051], with the net-profit figure corroborated by [S950].

**P/E:**
- TTM attributable net profit = FY2025 (CNY 134.95 M [S940;S1040]) − Q1 2025 (CNY 9.37 M [S940]) +
  Q1 2026 (CNY 18.74 M [S1051;S950]) = 134.95 − 9.37 + 18.74 = **CNY 144.32 M**.
- **P/E (ttm) = 71,777.21 ÷ 144.32 = 497.35x.** Cross-check: the same gtimg raw quote string
  [S1120] carries a field (raw-string index 39) of **497.35** — matches to the basis point.
- Secondary/static basis (FY2025 full-year only, no Q1-roll): 71,777.21 ÷ 134.95 = **531.90x.**
  Cross-check: the same gtimg raw quote string [S1120] carries a field (index 53) of **531.90** —
  an exact match.
- Both a TTM P/E of ~497x and a static FY2025 P/E of ~532x are extreme in absolute terms — far
  richer than either 002916 (~77x ttm) or 688629 (~216x ttm), this mission's other two
  freshly-valued PCB/substrate/connector names — on a company whose FY2025 归母 (attributable)
  net margin was just 1.88% and whose FY2025 consolidated (pre-minority) net margin was actually
  NEGATIVE at -1.45% [F_002436.md, derived from S1040] — see Implied expectations below.

**P/S:**
- TTM revenue = FY2025 (CNY 7,194.62 M [S940;S1040]) − Q1 2025 (CNY 1,579.60 M [S940]) + Q1 2026
  (CNY 1,818.17 M [S1051]) = 7,194.62 − 1,579.60 + 1,818.17 = **CNY 7,433.19 M**.
- **P/S (ttm) = 71,777.21 ÷ 7,433.19 = 9.66x.** No vendor P/S field was identified in the gtimg raw
  string with a confirmed arithmetic match (unlike P/E above) — this figure has no independent
  vendor cross-check, the same limitation V_002916/V_688629 both documented for this ticker-class.
- Secondary/static basis (FY2025 full-year only): 71,777.21 ÷ 7,194.62 = **9.98x.**

**EV/EBITDA:** **n/a (inputs absent in P2 extraction).** F_002436.md's 3-fiscal-year table and
arithmetic notes carry revenue, gross margin, net margin, operating cash flow, capex, net
cash/(net debt), top-5 customer concentration, and R&D intensity — but no EBIT/operating-profit
line item and no depreciation-and-amortization figure, so EBITDA cannot be built from this
session's Phase-2 extraction (same gap V_002916/V_688629 both documented for their own tickers).
For partial context only (not a ratio input): EV ≈ market cap + FY2025 net debt = 71,777.21 +
4,354.62 (net debt [S1043]) = **CNY 76,131.83 M ≈ CNY 76.13 bn** — not carried through to a ratio
absent an EBITDA denominator.

## Implied expectations

At CNY42.23/share and CNY71.78bn total market cap (2026-07-07 post-close [S1120;S1121]), 兴森科技
trades at ~497.35x TTM P/E (TTM attributable net profit CNY144.32M, built as FY2025 CNY134.95M
[S940;S1040] − Q1-2025 CNY9.37M [S940] + Q1-2026 CNY18.74M [S1051;S950]) and ~9.66x TTM P/S (TTM
revenue CNY7,433.19M, same build from FY2025 CNY7,194.62M [S940;S1040], Q1-2025 CNY1,579.60M
[S940], Q1-2026 CNY1,818.17M [S1051]) — multiples that assume a materially stronger, more mature
company than the one Phase 1/2 verified. FY2025's actual print was a fragile, partial recovery,
not a breakout: gross margin rebuilt to only 19.57% [S1040] after collapsing from 23.32% (FY2023)
[S1042] to 15.87% (FY2024) [S1041]; 归母 net margin was just 1.88% [S940;S1040], and net margin on
a consolidated, pre-minority-interest basis was still NEGATIVE at -1.45% [S1040, derived] —
minority shareholders in loss-making subsidiaries are absorbing losses large enough that the
headline parent-attributable profit flatters the underlying business; operating cash flow swung
NEGATIVE for the first time in the 3-year window (-CNY62.75M, -116.70% YoY) [S940;S1046]; and net
debt widened every year (CNY2,182.70M→3,447.12M→4,354.62M, FY2023→FY2025) [S1045;S1044;S1043]
even as capex decelerated (CNY1,881.20M→1,127.87M→852.68M, same window) [S1048;S1047;S1046]. The
one growth vector that could justify a ~500x earnings multiple — FCBGA/ABF advanced-packaging
optionality into an AI-substrate, Huawei/Ascend-adjacent narrative — is the company's own admitted
laggard, not its current profit engine: its most recent, most comprehensive IR record (2026-05-08)
states plainly that "2023-2025年期间，公司FCBGA封装基板项目的整体经营不及预期，对公司净利润形成
较大拖累" (the FCBGA project has underperformed for three straight years, materially dragging down
profit), with FCBGA still in "小批量生产阶段" (small-batch production) and no mass/batch orders as
of that date [S941]; the Guangzhou FCBGA-scale-up subsidiary generated just 0.37% of FY2025
consolidated revenue while posting a large loss [S954;S955]. This is not a case of zero Huawei
relationship — the company separately confirmed, tier-A, that it cooperates with Huawei across
both its PCB and semiconductor/IC-substrate segments, dated 2023-09-08 [S942] — but that
confirmation is now three years stale, unquantified, and explicitly does not establish Ascend/
AI-chip specificity, the load-bearing element for a multiple this size. Directly asked, by name,
whether it supplies Huawei's Ascend 910C (2024-05-28) or Ascend 920 (2025-07-11) chips, the
company declined to confirm both times, offering only generic capability reassurances [S943;S944];
customer concentration has risen (top-5: 15.85%→25.62%→27.29%, FY2023→FY2025; #1 customer 13.06%
in FY2025) but no source names that customer, so the trend cannot be read as Huawei/Ascend-specific
either way [S948;S949]; and the specific, precise-sounding "70% of ABF capacity to Huawei Ascend,
CNY1.5bn+ of 2025 Huawei orders" narrative that circulates around this name traces, on direct
inspection, to an uncited tier-4 forum/self-media post, not to any filing, 互动易 reply, or named
analyst report [S945]. For today's price to be justified, the market must be underwriting a
FCBGA/ABF mass-production ramp — Huawei/Ascend-specific and large enough to turn a currently
sub-1%-of-revenue, loss-making line into the company's dominant profit driver within a few years —
a future the company's own most recent disclosures neither confirm nor project, and one that sits
uneasily against a business currently burning operating cash and adding net debt. Flag:
**PRICED-FOR-PERFECTION** — a ~497x trailing-earnings, ~10x trailing-sales multiple on 1.88% net
margins (negative on a consolidated basis), negative operating cash flow, and a
company-acknowledged three-year FCBGA underperformance prices in a Huawei/Ascend-scale
AI-substrate breakout that remains, per this mission's own Phase-1 audit, Tier-C/forum-sourced and
contradicted in several particulars by the company's own numbers.

## Sources

- [S940] SZSE disclosure server: 兴森科技 2025年年度报告摘要 (own filing, 公告编号 2026-04-012),
  signed 2026-04-23, tier 1, fetched — FY2025/FY2024 revenue, 归母净利润, OCF and their stated
  YoY%; FY2025 quarterly breakdown incl. Q1 2025 revenue/net-profit (already ledgered, see
  V_002436.md / F_002436.md).
- [S941] 兴森科技投资者关系活动记录表编号：2026-05-001 (2025年度业绩说明会), 2026-05-08, tier 1,
  fetched — company's own admission FCBGA project "整体经营不及预期，对公司净利润形成较大拖累"
  2023-2025, no mass/batch orders yet as of 2026-05-08 (already ledgered, see V_002436.md).
- [S942] 腾讯新闻(news.qq.com): 兴森科技与华为在PCB业务和半导体业务领域均有合作 (互动易回复relay,
  tier A relationship, not Ascend-specific), 2023-09-08, tier 3, fetched (already ledgered, see
  V_002436.md).
- [S943] 财联社(cls.cn): 兴森科技 declines to confirm HBM/Ascend910C supply when asked by name,
  2024-05-28, tier 3, fetched (already ledgered, see V_002436.md).
- [S944] 新浪财经头条(cj.sina.com.cn): 兴森科技 declines to confirm when asked about Ascend 920 by
  name, generic capability reply only, 2025-07-11, tier 3, fetched (already ledgered, see
  V_002436.md).
- [S945] 东方财富财富号 self-media/guba post, 署名"跟增量买回调的憨哥", 2025-11-12, tier 4, FLAGGED
  uncited — source of the widely-repeated "70%产能/15亿元订单" Huawei/Ascend narrative, traced on
  direct inspection to have no filing/analyst support (already ledgered, see V_002436.md; cited
  here only to explain why it is NOT used as support).
- [S948] 同花顺(10jqka) F10 经营分析, tier 3, fetched — top-5 customer concentration, all 3 years
  (already ledgered, see V_002436.md / F_002436.md).
- [S949] 东方财富(Eastmoney) F10 BusinessAnalysis, tier 3, fetched — cross-check of same
  customer-concentration figures (already ledgered, see V_002436.md / F_002436.md).
- [S950] 搜狐(m.sohu.com): Q1 2026 headline revenue/net-profit/YoY%, 2026-04-25, tier 3, fetched
  (already ledgered, see F_002436.md).
- [S954] 同花顺(10jqka): Guangzhou FCBGA subsidiary FY2025 revenue = 0.37% of consolidated revenue,
  large net loss (引述股票交易异常波动公告), 2026-06-17, tier 3, fetched (already ledgered, see
  V_002436.md).
- [S955] 搜狐(sohu.com): corroborates same 0.37%/large-loss figure, 2026-06-17, tier 3, fetched
  (already ledgered, see V_002436.md).
- [S1040] Sina 利润表, ctrl=2025 — FY2025 revenue CNY7,194.62M, net profit attrib. CNY134.95M,
  consolidated (pre-minority) net profit CNY-103.99M (already ledgered, see F_002436.md).
- [S1041] Sina 利润表, ctrl=2024 — FY2024 gross margin input (15.87%) (already ledgered, see
  F_002436.md).
- [S1042] Sina 利润表, ctrl=2023 — FY2023 gross margin input (23.32%) (already ledgered, see
  F_002436.md).
- [S1043] Sina 资产负债表, ctrl=2025 — FY2025 year-end net debt CNY(4,354.62)M (already ledgered,
  see F_002436.md).
- [S1044] Sina 资产负债表, ctrl=2024 — FY2024 year-end net debt CNY(3,447.12)M (already ledgered,
  see F_002436.md).
- [S1045] Sina 资产负债表, ctrl=2023 — FY2023 year-end net debt CNY(2,182.70)M (already ledgered,
  see F_002436.md).
- [S1046] Sina 现金流量表, ctrl=2025 — FY2025 OCF CNY(62.75)M, capex CNY852.68M (already ledgered,
  see F_002436.md).
- [S1047] Sina 现金流量表, ctrl=2024 — FY2024 capex CNY1,127.87M (already ledgered, see
  F_002436.md).
- [S1048] Sina 现金流量表, ctrl=2023 — FY2023 capex CNY1,881.20M (already ledgered, see
  F_002436.md).
- [S1049] 同花顺(10jqka) finance.html — structurally-different 3-year summary table, used by
  F_002436.md as its principal second-source cross-validation (already ledgered, see F_002436.md).
- [S1051] Sina 利润表, ctrl=2026 — Q1 2026 revenue CNY1,818.17M, net profit attrib. CNY18.74M
  (already ledgered, see F_002436.md).
- [S1120] 腾讯证券 qt.gtimg.cn real-time quote, accessed 2026-07-07, tier 2, fetched — NEW, this
  file's primary price/mktcap/vendor-PE source (raw tilde-delimited string).
- [S1121] 东方财富 push2delay.eastmoney.com quote API, accessed 2026-07-07, tier 2, fetched — NEW,
  secondary/consistency-check quote source, share-count basis for mktcap.

Full ledger entries for S1120–S1121: `90_BIBLIOGRAPHY/frags/pp3_002436.json`.
