Timzhao0205/PhD_Career_Portfolio/03_Investments_and_Finance/02_Ascend_Benchmark_Mission_2026-07/10_PHASE1_VERIFICATION/V_002916.md

Educational benchmark for a paper-trading learning exercise. Simulated allocations, not investment advice or recommendations.

# V_002916 — 深南电路 Shennan Circuits, SZSE 002916

Watchlist entry under test: "2026-07-05,002916,SZSE,深南电路,PCB / substrate,B,AI-server PCB
exposure per research notes,S010,Huawei link generic not Ascend-specific"

## Claim under test
"Shennan Circuits supplies PCBs into Huawei AI/Ascend systems." Shennan is historically
described as a core Huawei PCB supplier (IPO-era prospectus disclosed Huawei as largest
customer). This audit asks what CURRENT (FY2025 / Q1 2026) disclosure actually says about
(i) customer concentration, (ii) AI-server/HPC PCB business, (iii) any Huawei/Ascend-specific
language — treating the historic prospectus facts as context, not current evidence, per the
assignment brief.

## Filings fetched
Direct WebFetch of the official cninfo/SZSE/aggregator-hosted PDF filings consistently FAILED
this session (tool returned raw FlateDecode/binary-stream errors, not text) across SIX distinct
PDF hosts and documents, despite repeated attempts:
1. FY2025 annual report summary (2025年年度报告摘要), cninfo, filed 2026-03-13 —
   http://static.cninfo.com.cn/finalpage/2026-03-13/1225006759.PDF — FAILED (binary/FlateDecode).
2. FY2025 full annual report, mirrored on 10jqka —
   http://notice.10jqka.com.cn/api/pdf/18d6ac5484a0cf8c.pdf — FAILED (4.3MB binary).
3. Investor-relations activity record, cninfo, 2025-09-26 —
   http://static.cninfo.com.cn/finalpage/2025-09-26/1224685368.PDF — FAILED.
4. Q1 2026 quarterly report, SZSE disclosure server —
   https://disc.static.szse.cn/disc/disk03/finalpage/2026-04-24/6d05f2f0-4155-4ed6-a68b-b0231141cba6.PDF
   — FAILED.
5. H1 2025 annual-report summary, company's own official website —
   https://www.scc.com.cn/yskjcmsresource/document/20240827/1013213937555996672.PDF — FAILED.
6. 2017 IPO prospectus (申报稿) — http://pdf.dfcfw.com/pdf/H2_AN201710170958153919_1.pdf —
   FAILED (5.9MB binary).
This deviates from the environment note that summaries/IR-records/short announcements
"usually parse" — in THIS ticker's case they did not either. **What DID parse successfully**
and is used as this audit's evidence base:
- Sina Finance's HTML bulletin-viewer mirror of the FY2025 annual report summary (same filing
  as #1 above, re-rendered as HTML by Sina rather than served as PDF) — [S190], fetched.
- Sina Finance's AIGC-generated interpretation articles of the FY2025 annual report and the
  Q1 2026 report (HTML news, not PDF) — [S197], [S198], fetched.
- 同花顺 (10jqka) F10 "经营分析" page (customer/supplier concentration table, computed by
  10jqka from disclosed data) — [S191], fetched.
- 同花顺 (10jqka) F10 "投资者互动" page, which mirrors SZSE 互动易/上证e互动 company replies
  verbatim — [S192], fetched (dated entries 2026-01-09 through 2026-06-03).
- Sina Finance's "董秘问答" (board-secretary Q&A) mirror of an 互动易-style reply — [S193],
  fetched (2025-03-16).
- The company's own official website news page (scc.com.cn) — [S199], fetched (2011, historic).
- Six tier-3 news articles (cls.cn, stcn.com, nbd.com.cn, 10100.com) quoting IR events/replies —
  [S194]–[S196], [S200], fetched.
- One named sell-side company-initiation report (西部证券) and one named sell-side weekly
  industry note (西部证券, different analysts), both via aggregator mirrors — [S202], [S204],
  fetched.
- One self-media/财富号 column, fetched and evaluated, then explicitly FLAGGED as uncited —
  [S201].
**Primary tier-1 fetched count: 3** (S192, S193, S199 — see gate discussion in Tier section).
Gate satisfied via ≥2 fetched tier-1 primary sources (2 official-reply mirrors + 1 own-website
historic notice), combined with the fully documented PDF-failure trail above.

## Evidence

### A. Current (FY2025/2026) financials and business description — own filing, via mirror

**[S190] FY2025 annual report summary content, Sina Finance HTML mirror of the cninfo filing
(filed 2026-03-13; tier 3 — see mirror-tier note below), fetched:**
> "2025年营业收入23,646,977,088.98元，同比增长32.05%" — FY2025 revenue = CNY 23,646,977,088.98
> (≈CNY 23.65bn / 236.47亿元), +32.05% YoY.
> "2025年归属于上市公司股东的净利润3,275,738,151.27元，同比增长74.47%" — net profit
> attributable to parent = CNY 3,275,738,151.27 (≈32.76亿元), +74.47% YoY.
> "印制电路板业务实现营业收入143.59亿元，同比增长36.84%，占公司营业收入的60.73%" — PCB segment
> = CNY 14.359bn, +36.84% YoY, 60.73% of revenue.
> "封装基板业务实现营业收入41.48亿元，同比增长30.80%，占公司营业收入的17.54%" — packaging
> substrate = CNY 4.148bn, +30.80% YoY, 17.54% of revenue.
> "电子装联业务实现营业收入30.75亿元，同比增长8.93%，占公司营业收入的13.00%" — electronic
> assembly/PCBA = CNY 3.075bn, +8.93% YoY, 13.00% of revenue.
> "公司储存产品应用于AI服务器、数据中心等应用领域的PCB产品" — storage-related PCB products
> are applied in AI-server / data-center application domains. GENERIC — no customer named.
> Note: the three named segments sum to 91.27% of total revenue (215.82亿/236.47亿); the
> remaining ~8.73% is not itemized in this summary format — flagged, not fabricated.
> (as-of FY2025, filed 2026-03-13)

**[S197] Sina Finance AIGC interpretation of the same FY2025 annual report (2026-03-12,
fetched), cross-check + additional detail:**
> "国际销售85.13亿元，同比增长49.93%，占公司营业收入的36.00%" — international sales =
> CNY 8.513bn, +49.93% YoY, 36.00% of revenue.
> "研发投入15.91亿元，占营收比重为6.73%，同比增长25.09%" — R&D = CNY 1.591bn, 6.73% of
> revenue, +25.09% YoY.
> "经营活动产生的现金流量净额38.38亿元，同比增长28.71%"；"投资活动产生的现金流量净额
> -37.56亿元，同比下降95.09%" — OCF +28.71% YoY to CNY 3.838bn; investing cash flow
> -CNY 3.756bn, -95.09% YoY (factory capex, consistent with Guangzhou/Thailand build-out
> noted in S196). No customer names; no Huawei/Ascend text found in this article.

**[S198] Sina Finance AIGC interpretation of Q1 2026 report (2026-04-23, fetched):**
> "营业收入65.96亿元...同比增长37.90%"；"归属于上市公司股东的净利润为8.50亿元...同比增长
> 73.01%"；"扣除非经常性损益的净利润为8.49亿元...同比增长75.04%"；"经营活动产生的现金流量
> 净额为2.47亿元...同比下降59.62%". No AI-server/data-center/Huawei/Ascend text found.

**[S194] 财联社 (cls.cn), 2023-12-03, fetched — company statement at an institutional
investor meeting:**
> "公司AI服务器相关PCB产品目前占比较低，对营收贡献相对有限。" — "AI-server-related PCB
> products currently represent a low proportion [of revenue], with relatively limited revenue
> contribution." (as-of Q3 2023 data — this is the most recent QUANTIFIED-direction statement
> found on this specific sub-segment; no updated percentage located through Q1 2026.)

**[S195] 证券时报网 STCN, 2025-03-12, fetched — reporting on the FY2024 annual report:**
> "在数据中心领域受益于AI服务器相关需求增长及行业周期性回暖，业务规模明显增长" — benefiting
> from AI-server-related demand growth and cyclical recovery in the data-center segment,
> business scale showed clear growth.
> "数据中心领域订单同比取得显著增长，成为PCB业务继通信领域后第二个达20亿元级订单规模的下游
> 市场" — data-center-segment ORDERS grew significantly YoY, becoming the second downstream
> market (after communications) for the PCB business to reach a CNY-2bn+ order scale. (Orders,
> not same-period revenue; ALL data-center customers combined, not Huawei-specific.)
> (as-of FY2024 annual report, published 2025-03-12)

**[S196] 每日经济新闻 NBD, 2025-09-05, fetched — investor-relations activity record:**
> "目前，公司综合产能利用率仍处于相对高位" — overall capacity utilization remains relatively
> high. H1 2025: PCB utilization high on "算力升级及汽车电子市场的增长需求" (compute-upgrade +
> auto-electronics demand); substrate utilization improved q/q on recovering storage demand.
> Guangzhou packaging-substrate base: Phase 1 connected Q4 2023, now ramping (BT + some
> FC-BGA orders). Thailand factory: CNY 1.274bn total investment, in trial production. No
> Huawei/Ascend text.

### B. Customer/supplier concentration — 10jqka F10 compiled table (tier 3, fetched)

**[S191] 同花顺(10jqka) F10 经营分析 page, fetched — self-consistent arithmetic verified
(component percentages sum correctly to the stated totals):**
> FY2025 (as of 2025-12-31): top-5 customers combined = CNY 4.356bn = **18.42%** of revenue;
> #1 = 7.46% (CNY 1.765bn), #2 = 3.08%, #3 = 2.93%, #4 = 2.52%, #5 = 2.43%.
> FY2024 (as of 2024-12-31): top-5 combined = 16.49%; #1 = 8.84%.
> FY2023 (as of 2023-12-31): top-5 combined = 19.87%; #1 = 9.79%.
> Top-5 suppliers FY2025 = 30.08% of procurement (CNY 4.240bn); #1 supplier = 8.69%
> (CNY 1.225bn).
> **No customer or supplier is named anywhere in this table** — all rows are numbered
> ("第一名" etc.), consistent with [S193] below.

**[S193] 董秘 (board secretary) reply, 2025-03-16, mirrored on Sina Finance "董秘问答"
channel (tier 1 — verbatim official-reply mirror), fetched — investor asked directly why
names aren't disclosed:**
> Investor's question: "董秘，您好！ 我是证券市场解读自媒体博主，我查阅了贵公司2024年年报，
> 未找到前五大供应商和客户的具体名称，请问是否可以公布？"
> Company's reply, verbatim: "尊敬的投资者，您好。公司严格按照年报监管规则披露相关信息。根据
> 《公开发行证券的公司信息披露内容与格式准则第2号——年度报告的内容与格式（2021年修订）》相关
> 规定，在未触发向单个客户销售/供应商采购的比例超过总额的50%等相关标准的情形下，不强制要求
> 上市公司分别披露前5名客户及前5名供应商的名称。公司基于商业保密原则，对客户及供应商名称以
> 第一名、第二名等予以替代，敬请谅解，谢谢您的关注。"
> Gloss: the company confirms, in its own words, that it substitutes customer/supplier NAMES
> with "first/second/etc." rankings, citing (a) a regulatory disclosure threshold that is only
> mandatory above 50% single-customer concentration (not met here — max is 7.46-9.79% across
> 2023-2025) and (b) its own commercial-confidentiality policy. This is the direct, dated,
> first-person explanation for why NO current filing names Huawei (or anyone else).

### C. Own 互动易 replies naming/declining AI-chain customers — tier 1 via 10jqka mirror

**[S192] 同花顺(10jqka) F10 "投资者互动" page, mirroring SZSE 互动易/上证e互动 company replies
verbatim (tier 1 content, fetched via aggregator):**
> 2026-06-03 — Q: "请问贵公司的产品是否进入了英伟达Rubin机架的供应链?" A: "基于商业保密原则，
> 凡涉及与具体企业合作的问题公司均不便于回复，敬请谅解。" (Declines to confirm/deny a specific
> named-customer relationship — Nvidia Rubin — citing commercial confidentiality.)
> 2026-01-09 — Q: "请问贵公司目前是否与AMD（超威半导体）存在直接业务合作?" A: same
> confidentiality-based decline.
> 2026-02-02 — Q: "公司PCB应用于AI服务器的营收占PCB整块营收的比例大约是多少?" A: "2025年第三
> 季度，受益于AI服务器及相关配套产品的需求增长，公司数据中心领域订单同比增长。" (Asked directly
> for an AI-server revenue-SHARE percentage; answer gives only qualitative growth language, no
> number, and does not name any customer.)
> 2026-01-13 — capacity-utilization reply: "受益于AI算力及存储市场需求的增长，近期公司综合
> 产能利用率处于高位。"
> **None of these dated 2026 replies contain the characters 华为 or 昇腾.** The company's
> demonstrated pattern, as recently as three weeks before this mission's as-of date, is to
> decline ANY specific-counterparty confirmation for AI/HPC customers (Nvidia, AMD tested;
> Huawei not directly tested in any reply located this session — see Risks/notes).

### D. Huawei-GENERIC evidence — historic, own disclosures (distinct from Ascend-specific)

**[S199] Shennan's own official website news page (scc.com.cn), published 2011-12-01
(tier 1 — own corporate communication, historic), fetched:**
> "11月3日，华为召开2011年度全球核心供应商大会，深南电路与其他33家著名企业一起荣获华为'金牌
> 核心供应商'大奖，成为唯一一家获此殊荣的PCB企业。" — On Nov 3 [2011], Huawei held its 2011
> annual global core-supplier conference; Shennan Circuits, together with 33 other companies,
> won Huawei's "Gold Medal Core Supplier" award — the ONLY PCB company to receive this honor.
> **This is a 15-year-old fact, offered as historic context only, per the assignment brief.**

**[S200] 10100.com (大数跨境), 2020-09-27, fetched — reporting on an investor-platform
(互动平台) reply:**
> "公司为其[华为]供应无线通信基站用PCB等产品" — the company supplies wireless-communication
> base-station PCB and other products to Huawei. Product = TELECOM INFRASTRUCTURE PCB, not
> AI-server/Ascend. Huawei is named directly (via a company reply, reported by a tier-3
> outlet), but the product category is explicitly non-AI.

**[S203, snippet-only, historic, non-load-bearing] 2017 IPO prospectus (申报稿) —** could
NOT be independently fetched/read this session (binary failure, see Filings-fetched section);
figures below are from WebSearch aggregation of the prospectus's own disclosed customer-
concentration table, not independently verified by direct read this session:
> Huawei's share of sales: 16.50% (2014), 20.18% (2015), 29.09% (2016), 24.55% (2017 H1).
> Top-5 customer combined share: 44.48%, 40.46%, 47.35%, 40.82% over the same four periods.
> Other named 2017-H1 top-5 members: ZTE (5.67%), Samsung (3.76%), Nokia (3.58%), Flextronics
> (3.25%).
> **Treated strictly as historic context, per the assignment brief — NOT used as a current
> (FY2025) evidentiary basis, and downgraded to "snippet" (not "fetched") because the primary
> document itself could not be independently read this session** despite three separate
> mirror-fetch attempts (dfcfw.com PDF, zhihu recap — HTTP 403 — and a smtjs.com trade-press
> mirror — connection refused).

### E. Ascend/AI-SPECIFIC attribution found — all tier-4 self-media/forum, explicitly uncited

**[S201] 东方财富财富号 (caifuhao.eastmoney.com) self-media column, byline "目标收购茅台"
(a personal pseudonym, not a named analyst or institution), 2026-03-05, fetched and directly
evaluated for sourcing:**
> Claims: "2025年，PCB业务营收占比已提升至62%，AI相关业务占比更是飙升至近30%" (2025 AI-related
> business share surged to ~30%) and "深南不仅是华为昇腾、中兴等国产算力龙头的核心供应商"
> (Shennan is a core supplier to Huawei Ascend, ZTE, and other domestic compute leaders).
> **On direct inspection: NEITHER claim cites a company disclosure, an 互动易 reply, nor a named
> sell-side report — both figures are, in the fetch's own words, "the author's own estimates or
> interpretations," fully unsourced.** This is the clearest concrete example located this
> session of the pattern the SOURCE_STANDARDS Tier-4 category describes (uncited "产业链梳理"
> post) — flagged, not used as support for anything.
Other same-tier hits located via search but not independently fetched/quoted (zhihu columns
"华为昇腾384超节点供应商梳理" and "聊一聊昇腾384"; 韭研公社 forum posts; a Douyin search page
titled "深南电路和华为合作") repeat similar unsourced "Ascend-384 PCB market share >30%" /
"Huawei ≈35%+ of revenue" figures. These were traced back to the Tier-4 forum/self-media
ecosystem consistently, not to any company filing or reputable outlet — consistent with the
watchlist's own starting note ("Huawei link generic not Ascend-specific").

### F. Named sell-side coverage checked — does NOT confirm the Ascend-specific link

**[S202] 西部证券 (Western Securities) company-initiation report on Shennan Circuits
specifically, analysts 葛立凯 (Ge Likai) / 李宁宇 (Li Ningyu), 2025-08-30, Buy rating, fetched
via an aggregator mirror:**
> Discusses INDUSTRY-level context — "预计25年华为等本土供应商在中国大陆AI芯片份额将提升至
> 40%" (domestic suppliers incl. Huawei projected to reach 40% of mainland China AI-chip share
> by 2025) — and uses "昇腾910C单卡PCB价值量或将高于H100的407美元水平" (Ascend 910C per-card
> PCB value may exceed Nvidia H100's ~$407) purely as an ANALYTICAL PRICING EXAMPLE for
> industry PCB-value upside. **The report does not state that Shennan itself supplies Huawei
> or Ascend as a confirmed customer** — these references sit in general market-trend
> discussion, not in a company-specific customer-disclosure section. This is a dedicated,
> named, company-specific sell-side report and it STILL stops short of the Ascend-specific
> customer claim.

**[Not separately ledgered, cross-checked via 东北证券 report reported by NBD, 2024-01-20]:**
lists Shennan generically among five PCB makers ("沪电股份、生益科技、兴森科技、深南电路、
景旺电子") "positioned to benefit" from Huawei's broader phone/AI-server/auto recovery — a
sector-theme mention, not a company-specific confirmed relationship.

## Tier assigned + reasoning

**This claim splits into two distinct sub-claims, and they resolve to DIFFERENT tiers — this
split is the central finding of this audit:**

1. **"Shennan has (had) a Huawei relationship, generically" — Tier A.** Substantiated by the
   company's own historic disclosures: the 2017 IPO prospectus (Huawei named as largest
   customer, 16.5-29.1% of sales, 2014-2017H1 — snippet-tier due to a session PDF-read
   failure, but the underlying fact is a well-established, widely-corroborated own-filing
   disclosure type), the company's own 2011 official-website announcement of a Huawei "Gold
   Medal Core Supplier" award, and a 2020 互动平台 reply (tier 3, quoting a company reply)
   naming Huawei as a customer for wireless base-station PCB. This relationship is real and
   company-confirmed, but **it is a TELECOM/wireless-infrastructure relationship, and it is
   4.5-15 years stale** — no CURRENTLY fetched source (annual report, quarterly report, or any
   2023-2026 互动易 reply) names Huawei at all.

2. **"Shennan's CURRENT AI-server PCB business is exposed to Huawei's Ascend systems
   specifically" — Tier C.** This is the operative claim for an Ascend-investment thesis, and
   it is NOT substantiated at Tier A or B by anything located in this session:
   - Own filings/replies (Tier A candidate): FY2025 annual report and all 2026 互动易 replies
     found use only generic "AI服务器"/"数据中心" language; when asked DIRECTLY for an
     AI-server revenue-share percentage (2026-02-02) or for confirmation of a specific AI-chain
     counterparty (Nvidia Rubin 2026-06-03; AMD 2026-01-09), the company declined to give a
     number or name any counterparty, citing confidentiality. This is the opposite of
     substantiation — it is a demonstrated, recent pattern of NON-disclosure on this exact
     question type.
   - Major media/named sell-side (Tier B candidate): three sell-side citations checked
     (a dedicated Shennan-specific initiation report and two chain-level notes) all discuss
     Huawei/Ascend only as INDUSTRY-level context or an illustrative pricing comparison, never
     as a confirmed Shennan-Huawei-Ascend customer relationship. No reputable non-self-media
     outlet (STCN, CLS, NBD, etc. — all checked and fetched) contains the word 华为 or 昇腾 in
     connection with Shennan's 2023-2026 business.
   - Forum/self-media (Tier C): zhihu columns, 韭研公社 posts, 东方财富财富号 self-media
     columns, and Douyin all repeat "Shennan = Huawei Ascend core supplier" with specific
     (30%+, 35%+) percentages — one such column was fetched and directly confirmed to be
     entirely uncited, "the author's own estimate." This is exactly the SOURCE_STANDARDS
     Tier-4/evidence-tier-C pattern: **a claim repeated across many forum posts remains Tier C
     no matter how many times it is repeated.**

**Headline tier for the claim as literally worded ("...into Huawei AI/Ascend systems") = C.**
The AI/Ascend-specific element is the load-bearing part of the claim and it rests on forum
repetition only, despite an honest, extensive Chinese-language search (cninfo, 互动易 mirrors,
official company channels, six sell-side/media checks, one dedicated company-initiation
report). This assessment CONFIRMS, with primary-source detail, the watchlist's own starting
caveat: "Huawei link generic not Ascend-specific."

## Exposure estimate (Huawei/Ascend-linked % of FY2025 revenue)

**NOT-ESTIMABLE as a Huawei/Ascend-specific point figure or defensible range.** Reasoning:
- No fetched Tier ≤3 source identifies WHO Shennan's FY2023-2025 top-5 customers are — the
  company itself anonymizes them by policy [S193], and the concentration table [S191] carries
  only rank numbers, never names.
- The best available ARITHMETIC CEILING (not a Huawei-specific estimate — a bound on ANY single
  unnamed customer) is: FY2025 #1 customer = **7.46%** of revenue (CNY 1.765bn / CNY 23.65bn)
  [S191]; FY2025 top-5 combined = **18.42%** [S191]. If Huawei happens to still be the #1
  customer, its FY2025 share would be AT MOST 7.46% — but no source confirms Huawei occupies
  any of the five ranked positions today.
- Context for that ceiling: top-5 concentration has run 16.49-19.87% across FY2023-2025 [S191]
  — structurally much LOWER than the 40.46-47.35% concentration disclosed for 2014-2017 [S203,
  snippet, historic], when Huawei alone was 16.50-29.09% of sales. This is consistent with
  (but does not prove) a diversifying customer base since IPO; it means even a continued
  Huawei relationship would almost certainly be smaller in relative-revenue terms today than
  15-4.5 years ago, independent of the name-anonymization issue.
- The AI-server PCB sub-segment specifically (the part of the business that would carry any
  Ascend-accelerator exposure) was self-described as "低" (low proportion, limited revenue
  contribution) as of Q3 2023 [S194] — the most recent quantified-direction statement located.
  The 2026-02-02 互动易 reply [S192] declined to update this with a number, giving growth
  language only. Tier-4 sources claim this sub-segment reached "~30%" of revenue by 2025
  [S201] but this figure is explicitly unsourced/self-estimated per direct inspection — it
  cannot be used per the NUMBER TRUTH RULE.
- Data-center-segment ORDER scale reached a "CNY 2bn+" tier for the first time in FY2024 per
  a tier-3 report on the annual report [S195] — this is (a) an order figure, not necessarily
  same-period revenue, (b) for ALL data-center customers combined, not Huawei-specific, and
  (c) roughly 11% of FY2024's CNY 17.907bn total revenue if treated as a revenue proxy (a
  stretch) — offered only as a rough sense of scale for the whole segment, not a Huawei
  estimate.
**Net: exposure_est_pct = NOT-ESTIMABLE.** The defensible arithmetic ceiling for "any single
customer, name unconfirmed" is 7.46% (FY2025); no portion of it, or of the broader AI-server/
data-center segment, can be attributed to Huawei/Ascend specifically without relying on
uncited Tier-4 claims.

## Risks/notes for later phases (facts only, no scores/rankings)
- **Disclosure regime:** Shennan's own reply [S193] confirms Chinese annual-report rules only
  MANDATE naming a customer/supplier if its share exceeds 50% of the relevant total — a
  threshold Shennan has been nowhere near since at least 2023 (max single-customer share
  9.79%, FY2023). This means customer-identity opacity here is a structural/regulatory feature
  of current disclosure, not something specific to Huawei sensitivity — worth remembering when
  comparing tiers across different tickers in this mission that DO name Huawei (e.g., where a
  single customer exceeds the threshold or the company chooses voluntary disclosure).
- **Recency asymmetry in company replies:** the company has, on the record, named Huawei
  directly in a 2020 reply about wireless base-station PCB [S200] but has, as recently as
  2026-06-03 and 2026-01-09, declined to name/confirm ANY specific AI/HPC counterparty
  (Nvidia, AMD) [S192]. No fetched 2023-2026 reply was located in which the company was asked
  about Huawei/昇腾 BY NAME and either confirmed or declined — this is a genuine gap for Phase
  2 to re-search (a direct "是否与华为昇腾合作" 互动易 question/answer, if one exists in
  2024-2026, was not located in this session's searches).
- **Capacity build-out is real and dated, but not customer-attributed:** Guangzhou packaging-
  substrate base (Phase 1 online Q4 2023, ramping BT/FC-BGA) and a CNY 1.274bn Thailand
  factory (trial production) [S196] are company-confirmed capacity investments plausibly
  relevant to AI/HPC-adjacent demand (FC-BGA is an advanced-packaging substrate format used in
  high-end processors), but no fetched source ties this capacity specifically to a Huawei/
  Ascend program.
- **FY2025 headline financials are strong and cash-generative:** revenue +32.05%, net profit
  +74.47%, OCF +28.71% [S190, S197]; Q1 2026 continued the trend (revenue +37.90%, net profit
  +73.01%) but with OCF -59.62% YoY [S198] — not explained in the fetched Q1 material; flagged
  for Phase 2 (working-capital build during a capacity-expansion phase is one plausible,
  unconfirmed explanation, consistent with the capex pattern in S196).
- **Segment disclosure has a ~8.7% unexplained residual:** the three named FY2025 segments
  (PCB 60.73% + substrate 17.54% + PCBA 13.00% = 91.27%) do not sum to 100% of revenue in the
  abbreviated summary format [S190] — flagged as a disclosure-granularity gap, not an error;
  Phase 2 should check whether the full annual report (currently unreadable in this
  environment) itemizes the remainder.
- **Source-quality flag:** at least one widely-styled 财富号 self-media column [S201] asserts
  specific, precise-sounding percentages ("AI相关业务占比~30%", implicitly "Huawei core
  supplier") with ZERO citation, confirmed on direct inspection — concrete, ticker-specific
  evidence for why forum/self-media claims on this name must not be load-bearing, mirroring
  the pattern already documented for 002261 in this mission (S154 there).
- **Environment limitation, documented:** six distinct official/aggregator PDF hosts (cninfo,
  10jqka notice-mirror, SZSE disclosure server, the company's own official website, and a
  research-PDF host for the 2017 prospectus) all failed to parse via WebFetch this session
  with the same FlateDecode/binary-stream symptom — a broader failure than the "usually parses"
  expectation for summaries/IR-records noted in the assignment brief. All quantitative claims
  in this file instead rest on HTML-rendered mirrors (Sina bulletin viewer, Sina AIGC articles,
  10jqka F10 pages) and tier-3 news articles, each cited individually above.

## DISCOVERY
While checking named sell-side coverage of the Huawei/Ascend PCB-and-connector chain for this
audit, one dated, named-analyst report was found that bears on a DIFFERENT existing watchlist
ticker: **[S204] 西部证券 (Western Securities), analysts 郑宏达 (Zheng Hongda) / 李想 (Li
Xiang), "计算机行业周观点第53期：关注华为昇腾产业链的基本面变化," 2026-03-29, fetched via a
research-note aggregator** — explicitly recommends tracking, for the backplane-connector
category within the Huawei/Ascend chain: "背板连接器：华丰科技、意华股份、航天电器" (backplane
connectors: Huafeng Technology [华丰科技, SSE-STAR 688629, already on this mission's
watchlist at evidence tier C, "Forum-claimed dominant share of Ascend backplane connectors"],
Yihua Co., Aerospace Electronics). This is a NAMED sell-side source explicitly discussing
688629 within a Huawei/Ascend-chain analytical context — Tier B evidence per
SOURCE_STANDARDS, an upgrade from 688629's current forum-only (Tier C) sourcing basis. Note:
this report recommends tracking the category/name; it does not itself state a specific
revenue-share figure for 华丰科技, so a full Tier-A/B verification (own filing or a
quantified claim) would still need a dedicated audit of 688629 — flagged here for that
ticker's own Phase-1 file, not scored or ranked in any way.

## Sources used
- [S190] Sina Finance HTML mirror of FY2025 annual report summary, 2026-03-13, tier 3,
  fetched — headline financials, segment revenue, generic AI-server/data-center language.
- [S191] 同花顺(10jqka) F10 经营分析, accessed 2026-07-06 (data as of 2025-12-31/2024-12-31/
  2023-12-31), tier 3, fetched — customer/supplier concentration, gross margins.
- [S192] 同花顺(10jqka) F10 投资者互动 (mirrors SZSE 互动易), accessed 2026-07-06 (entries
  2026-01-09 to 2026-06-03), tier 1, fetched — Nvidia/AMD confidentiality declines, AI-server
  revenue-share non-disclosure, capacity-utilization reply.
- [S193] 董秘 reply via Sina Finance "董秘问答" mirror, 2025-03-16, tier 1, fetched —
  verbatim explanation of customer/supplier name-anonymization policy.
- [S194] 财联社 cls.cn, 2023-12-03, tier 3, fetched — "AI服务器相关PCB产品目前占比较低."
- [S195] 证券时报网 STCN, 2025-03-12, tier 3, fetched — data-center order growth, CNY-2bn+
  order-scale milestone (reporting on FY2024 annual report).
- [S196] 每日经济新闻 NBD, 2025-09-05, tier 3, fetched — capacity utilization, Guangzhou/
  Thailand capacity detail.
- [S197] 新浪财经 AIGC interpretation, 2026-03-12, tier 3, fetched — FY2025 cross-check,
  international sales, R&D, cash flow.
- [S198] 新浪财经 AIGC interpretation, 2026-04-23, tier 3, fetched — Q1 2026 figures.
- [S199] 深南电路官网 scc.com.cn, 2011-12-01, tier 1, fetched — Huawei "Gold Medal Core
  Supplier" award (historic, own website).
- [S200] 10100.com, 2020-09-27, tier 3, fetched — quotes company reply naming Huawei as a
  wireless-base-station-PCB customer.
- [S201] 东方财富财富号 self-media column ("目标收购茅台"), 2026-03-05, tier 4, fetched,
  FLAGGED — uncited "~30% AI revenue share" / "Huawei Ascend core supplier" claims.
- [S202] 西部证券 company-initiation report (analysts 葛立凯/李宁宇), 2025-08-30, tier 3,
  fetched — industry-context Huawei/Ascend discussion; does not confirm a customer link.
- [S203] 2017 IPO prospectus, historic customer-concentration figures, tier 1, SNIPPET only
  (WebSearch aggregation; direct PDF read failed three times this session) — used strictly as
  historic context, not current evidence.
- [S204] 西部证券 weekly industry note (analysts 郑宏达/李想), 2026-03-29, tier 3, fetched —
  DISCOVERY source for watchlist ticker 688629 (华丰科技), not itself about 002916's exposure.
