Timzhao0205/PhD_Career_Portfolio/03_Investments_and_Finance/02_Ascend_Benchmark_Mission_2026-07/10_PHASE1_VERIFICATION/V_688629.md

Educational benchmark for a paper-trading learning exercise. Simulated allocations, not investment advice or recommendations.

# V_688629 — 华丰科技 Sichuan Huafeng Technology, SSE-STAR 688629

Watchlist entry under test: "2026-07-05,688629,SSE-STAR,华丰科技,high-speed connectors,C,Forum-claimed
dominant share of Ascend backplane connectors,S009,Extraordinary claim -> needs filing-grade proof"

Known lead (from a sibling audit this mission, [S204], already ledgered by the 深南电路/002916 audit,
referenced here per task instruction rather than re-fetched): 西部证券 computer-sector weekly #53
(analysts 郑宏达/李想, 2026-03-29) recommends tracking 背板连接器 (backplane-connector) names
华丰科技/意华股份/航天电器 in a Huawei/Ascend-chain fundamentals context — a named-sell-side
(tier B) floor for the SUPPLY claim if the company's own record corroborates it.

## Claim under test (two distinct claims, assessed separately as instructed)

**Claim 1 — SUPPLY LINK:** "华丰科技 supplies high-speed/backplane connectors that go into Huawei's
Ascend-era AI-compute systems (data-center servers)."

**Claim 2 — DOMINANCE:** "华丰科技 holds a dominant share of Ascend backplane-connector supply" — the
watchlist's literal intake framing, sourced only to a forum-aggregation roll [S009, tier 4] at intake.

These need different evidentiary bars. Claim 1 is a binary supply-relationship question. Claim 2 is a
competitive-market-share question — 华丰's share of HUAWEI's/ASCEND's connector-vendor panel versus
rival suppliers — which is analytically the OPPOSITE ratio from customer concentration (HUAWEI's share
of 华丰's own revenue). This audit keeps the two directions of that ratio separate throughout; conflating
them is the single most likely way this claim gets overstated.

## Filings fetched

**Successfully read (content used as evidence):**
- FY2025 年度报告摘要 (annual report summary), filed 2026-04-15, via 上海证券报/cnstock.com reprint
  mirror — [S265], fetched.
- FY2025 年度报告 FULL text (not just the summary), via Sina Finance bulletin-detail HTML mirror of the
  same cninfo filing — [S266], fetched. This is the single richest source in this audit: it rendered the
  actual customer-concentration table and headline financials as filing text, not just summary color.
- 2026年第一季度报告 (Q1 2026 quarterly report), filed 2026-04-28, via Sina Finance bulletin-detail HTML
  mirror — [S270], fetched.
- 同花顺(10jqka) F10 "投资者互动" page, mirroring SSE 上证e互动/互动易 company replies verbatim —
  [S267], fetched (tier-1 content).
- 同花顺(10jqka) F10 "经营分析" page (customer/supplier concentration, gross margin) — [S268], fetched.

**Attempted and FAILED this session (documented, not fabricated around):**
1. H1 2025 半年度报告 full PDF, cninfo — `static.cninfo.com.cn/finalpage/2025-08-26/1224571054.PDF` —
   FAILED (binary/FlateDecode stream, unreadable).
2. 投资者关系活动记录表 (IR activity-record) PDF, dated 2025-10-29, QQ-finance mirror of a cninfo filing
   — `file.finance.qq.com/finance/hs/pdf/2025/10/29/3efaa862b4ab11f0bb5cfa163e39923a.pdf` — FAILED
   (binary/FlateDecode). No alternative HTML-rendered mirror of an IR activity record for this specific
   ticker was located this session — flagged as a genuine gap, not fabricated around.
3. 东吴证券 (Soochow Securities) company deep-dive report PDF — `pdf.dfcfw.com/pdf/H3_AP202505171674241726_1.pdf`
   — FAILED (binary stream). This report's title ("华丰科技（688629）") suggests it might carry a
   quantified backplane-connector market-share figure; could not be independently verified this session.
4. IPO prospectus (申报稿) and the 2025年度向特定对象发行A股股票 regulatory-inquiry-response PDF, both via
   dfcfw.com — FAILED (binary). Content from these documents is used below only via tier-3 media reports
   that quote them (jiemian.com, Sina AIGC), explicitly marked as such.
5. Two additional 10jqka `notice.10jqka.com.cn/api/pdf/...` filing PDFs — one exceeded the fetch tool's
   10MB size limit, one returned a connection error — FAILED.
6. Company's own official website, `www.huafeng796.com` — connection refused (ECONNREFUSED). No own-website
   historic announcement (the kind that gave tier-1 color in a sibling audit) could be obtained this
   session.
7. `sns.sseinfo.com/company.do?stockcode=688629` (the actual 上证e互动 company page) and
   `open.sseinfo.com/ir2/indexkcb?stockCode=688629` (SSE's own IR portal) — both loaded only as
   JavaScript-rendered shells ("努力加载中...", empty Q&A sections); the underlying dynamic content was not
   captured by this session's fetch tool.
8. A Xueqiu (雪球) annual-report-highlights article render returned obfuscated/encoded content; a
   `cfi.net.cn` fetch returned empty content. Neither usable.

**Gate discussion:** by strict ledger-tier convention followed elsewhere in this mission (dedicated
互动易/上证e互动-mirror pages such as [S267] are ledgered tier 1; HTML reprints of the underlying annual/
quarterly report filing itself, and news articles that quote replies or briefings, are ledgered tier 3
matching their publisher, even though their CONTENT is the company's own words) this audit has **one**
clean ledger-tier-1 source ([S267]). It is combined with (a) two successfully-read HTML mirrors of the
actual FY2025 and Q1-2026 filings themselves ([S266], [S270] — content = own filing, tier column follows
the mirror site per task instruction), (b) a dated, quoted official reply captured independently via a
second mirror ([S269]), and (c) the fully-documented eight-way PDF/dynamic-page failure trail above. Per
the standing precedent in this mission (`V_002916`, which satisfied its gate the same way), this is judged
sufficient: the underlying primary CONTENT is present and internally cross-consistent (see Evidence
section), even where the ledger tier of the access path is 3.

## Evidence

### A. Own filings — FY2025 annual report and Q1 2026 quarterly report

**[S266] FY2025 annual report, filed 2026-04-15, Sina Finance HTML mirror of the cninfo original, fetched
— headline financials and customer table:**
> "2025年公司实现营业收入2,527,729,770.66元" — FY2025 revenue = CNY 2,527,729,770.66 (≈CNY 2.528bn /
> 25.28亿元).
> "前五大客户合计销售收入为185,150.88万元，占公司2025年销售收入的73.25%" — top-5 customers combined =
> CNY 1,851,508,800 (185,150.88万元), = **73.25%** of FY2025 revenue. Arithmetic check: 1,851,508,800 /
> 2,527,729,770.66 = 73.25% exactly — self-consistent.
> Largest single customer ("客户一" — **not named** in this filing) = **60.52%** of revenue.
> "BackplaneConnector是信息通信设备的关键互连件" — backplane connectors described as key interconnect
> components of information/communication equipment (own filing, English term embedded in original).
> **No 华为/昇腾/超节点 characters found in this rendering.**
> (as-of FY2025, filed 2026-04-15)

**[S265] FY2025 annual report SUMMARY, 上海证券报/cnstock.com reprint mirror of the same cninfo filing,
fetched:**
> "2025年公司收入25.28亿元，较上年增长14.36亿元，同比增长131.50%；实现归属于上市公司股东的净利润为
> 3.59亿元" — revenue +131.50% YoY to CNY 2.528bn; net profit attributable to parent = CNY 359mm.
> Qualitative segment language (no % table in the summary format): "通讯领域：高速背板连接器、服务器连接
> 产品、数据中心解决方案；防务领域：FMC系列、JVNX系列高速连接器；工业领域：轨道交通、新能源汽车高压连接器"
> — communications: high-speed backplane connectors, server-connection products, data-center solutions;
> defense: FMC/JVNX series; industrial: rail transit, EV high-voltage connectors.
> Customer text (descriptive, no percentages): "华为、中兴、诺基亚的全球供应商"；"上汽通用五菱的主力供应商
> 之一"；"比亚迪高压配电模块的主要供应商之一"；"中国中车集团旗下众多一级、二级子公司" — global supplier to
> Huawei/ZTE/Nokia; primary supplier to SGMW; major supplier to BYD's high-voltage distribution modules;
> supplies numerous CRRC subsidiaries. **No percentage table for customer concentration appears in the
> summary format** — that came only from the full-report mirror [S266] and the F10 compilation [S268].
> (as-of FY2025, filed 2026-04-15)

**[S270] Q1 2026 quarterly report, filed 2026-04-28, Sina Finance HTML mirror, fetched:**
> "营业收入633,223,075.00元" +56.15% YoY (prior-year-quarter CNY 405,525,885.18).
> Profit metric: CNY 115,648,233.63, +311.05% YoY (label ambiguous in this specific extraction — a
> separate, non-fetched search pass suggested this is 利润总额/pre-tax profit total, with 归属于上市公司
>股东的净利润 [net profit attributable] separately at CNY 105,112,635.87 +230.43% YoY; that second figure
> is NOT independently confirmed by direct fetch this session and is offered as color/snippet only, not
> load-bearing).
> **Company's own stated reason for growth, verbatim:** "主要系AI服务器、数据中心等终端产品国产化替代的
> 驱动，同时公司新产品在服务器领域渗透率持续提升，通讯领域新产品新增订单明显增长。" — "mainly due to the
> domestic-substitution drive in AI-server, data-center and other terminal products, alongside the
> company's new products' steadily rising market penetration in the server segment and a marked increase
> in new orders for new communications-segment products." This is the company's OWN filing language,
> explicitly tying growth to AI-server/data-center domestic substitution — **the word 华为/昇腾 does not
> appear in this specific sentence.**
> (as-of Q1 2026, filed 2026-04-28)

### B. Own investor-platform replies (上证e互动/互动易 mirrors) — the supply-relationship statements

**[S267] 同花顺(10jqka) F10 "投资者互动" page, mirroring SSE 上证e互动/互动易 company replies verbatim,
fetched (tier-1 content):**
> "公司是华为高速背板连接器核心供应商之一" — "The company is one of the core suppliers of Huawei's
> high-speed backplane connectors."
> "224G高速连接器已与华为等主要客户开展项目合作、交流" — 224G high-speed connectors already under
> project cooperation/exchange with Huawei and other major customers.
> "高速背板连接器及高速线模组产品广泛适用于数据中心用高端服务器、交换机等" — high-speed backplane
> connectors and high-speed cable modules are broadly applicable to data-center high-end servers,
> switches, etc. (own-reply language explicitly placing the product in data-center/AI-server territory).
> Other named customers/partners in the same reply set: "已与上汽通用五菱、比亚迪等新能源车企合作"; "与
> 阿里、腾讯、字节、超聚变、寒武纪等开展或推动项目合作" (project cooperation/promotion with Alibaba,
> Tencent, ByteDance, XFusion [超聚变, a Huawei-lineage server maker], Cambricon).
> On specifics: the company repeatedly invokes "遵循商业保密原则，具体合作细节不便披露" (commercial
> confidentiality; declines to disclose cooperation specifics) when pressed further.
> As of 2026-03-31, shareholder count = 4.49万户 (unrelated data point, confirms recency of this reply set).
> **No literal 昇腾 or 超节点 characters found in any reply captured on this page**, despite the page
> covering entries into 2026.

**[S269] 华丰科技 official investor-platform reply, dated 2024-03-21, mirrored/reported by QQ news
(tier 3 mirror; content = company reply via mirror), fetched:**
> "公司是华为高速背板连接器核心供应商之一" — verbatim match to [S267]'s current-era language, here
> independently dated to 2024-03-21, confirming this has been the company's standing, repeated position
> for at least two years.
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
