Timzhao0205/PhD_Career_Portfolio/03_Investments_and_Finance/02_Ascend_Benchmark_Mission_2026-07/10_PHASE1_VERIFICATION/V_688981.md

Educational benchmark for a paper-trading learning exercise. Simulated allocations, not investment advice or recommendations.

# V_688981 — 中芯国际 SMIC, SSE-STAR 688981 (dual-listed 0981.HK)

Watchlist entry under test: "2026-07-05,688981,SSE-STAR,中芯国际 SMIC,foundry,B,Widely reported
Ascend foundry (7nm-class DUV); capacity+yield = chain bottleneck,S010;S013;S016,Also listed
0981.HK; verify vs SMIC filings (they never name Huawei)" (original S010/S013/S016 cites are the
prior corpus's, not re-fetched in this session; this file re-derives the claim from fresh
research against SMIC's own disclosures and new tier-3 evidence).

## Claim under test

Two claims, audited separately because they have different evidentiary ceilings:

**(i) Customer/factual claim — "SMIC fabricates Huawei's Ascend AI-accelerator dies."**
Specifically: Ascend 910B/910C on SMIC's 7nm-class (N+1/N+2) DUV-multipatterning process, and
the newer Ascend 950PR on SMIC's N+3 (~5nm-class) process. **Expected ceiling: Tier B at best.**
SMIC is a US Entity-List company (since 2020-12, restricted from EUV and other sub-10nm tools/
tech under a "presumption of denial" license policy — see Risks section); naming a specific
end-customer for its most advanced node would be commercially and geopolitically sensitive, so
the prior expectation (stated in the task and the watchlist note) is that SMIC's own filings and
investor replies will **never** confirm this by name. This file tests that expectation directly
against SMIC's FY2025 annual results, Q1 2026 quarterly results, and the company's own investor-
relations replies — and confirms it holds (see "What SMIC itself says/declines" below).

**(ii) Structural/bottleneck claim — "SMIC's capacity and yield are the binding constraint on
domestic Ascend-class AI-chip output."** This is auditable directly from SMIC's own disclosed
revenue, capex, capacity, and utilization figures (all disclosed; only the *customer* attribution
is withheld), cross-referenced against tier-3 estimates of Ascend-specific capacity/yield.
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
