Timzhao0205/PhD_Career_Portfolio/01_PhD_Research/09_PAP06_Career_Portfolio_Synthesis_2026-07/CHANGELOG.md

# Version 5.0 native rebuild

- Removed every active PowerShell, Bash, Python, JavaScript, hook, and
  code-validator dependency.
- Replaced launcher/orchestration scripts with a project skill and a visible
  Fable 5/xhigh main agent.
- Added foreground, model/effort-locked workers and a fresh Fable 5/xhigh
  verifier for every full stage.
- Preserved all unique old/new Folder 06, PhD, startup, and history content in
  pre-expanded form.
- De-duplicated two byte-identical old Folder 06 copies after a 419/419
  path-and-hash comparison.
- Renamed historical executable/configuration files to inert source names.
- Preserved the 15-stage pilot-first route and added peer-reviewed literature
  search/adjudication, bidirectional PhD/startup analysis, power electronics,
  shared skills, portfolio, roadmap, red team, synthesis, and final audit.
- Added durable, conversation-independent resume rules.
- Removed all package budget/cost/token/turn/time shutdowns.
- Added explicit requested-versus-observed model evidence rules.
