Timzhao0205/PhD_Career_Portfolio/01_PhD_Research/10_HSX_IP_and_arXiv_Screen_2026-08/state/WORKLOG.md

# Durable work log

Package created and statically validated before delivery. Runtime entries are
appended by the parent after each stage. Do not erase prior entries on resume.

## 2026-08-05T07:13:11Z — RUN START — run_id HSXIP-20260805T071311Z

- Parent session: Claude Fable 5 / xhigh (per session config; observed telemetry `not_exposed`).
- Read `START_HERE.md`, `CLAUDE.md`, `IP_SCOPE.md`, `MODEL_PLAN.md`, `SOURCE_POLICY.md`, `schemas/OUTPUT_GATES.md`.
- `session_started` set to true; status RUNNING.
- Artifact inventory and SHA-256 verification (all match `inputs/HASHES.sha256`):
  - `inputs/manuscript/source_original.zip` — a4748e8e962d33931f67db8b82f9c136b7b783ff27aa33babef56a6afec65a6e
  - `inputs/manuscript/submission.pdf` — fa1563a04a7fdc79c80c38d39db8f69d4af50291fe010e5808249cf457d0e48c
  - `inputs/manuscript/source/regular_lsens/regular_lsens.tex` — fc34b033802de487bfdd39e9dc4eeb568fc3d4854b6734d196975ef9701c509e
- Excluded archives (`inputs/context/excluded_archives.csv`) noted as excluded; not present in package; scope boundary enforced.
- Proceeding to stage 00 (`s00-scope`, Sonnet 5 / medium per `MODEL_PLAN.md`).

## 2026-08-05T07:17:39Z — STAGE 00 ACCEPTED

- `outputs/00_SCOPE_AUDIT.md` written by `s00-scope`; parent validated against stage-00 gate: PASS.
- Integrity: all three artifact hashes re-verified by the stage; match manifest. PDF is 9 pages; ZIP has 17 entries; IEEE_lsens.cls is stock.
- Facts recorded: authors span Stanford (Zhao, Cox, Senesky) and UW-Madison NEEP (Goodman, Gallenberger, Geiger); sponsorship DOE DE-AC02-76SF00515, SLAC FWP 101264, TomKat, NSF ECCS-2026822 — routed to stage 50 sponsor/inventor questions.
- Source-hygiene anomalies for stage 50: (1) commented-out alternate abstract in TeX (no new technical content); (2) `.log`/`.synctex.gz` in source ZIP embed local machine paths; `.aux`/`.log`/`.synctex.gz` are unnecessary for arXiv.
- Excluded PhD/startup archives confirmed absent; contents never opened.
- Checkpoint `state/checkpoints/00_done.json` created. Proceeding to stage 10 (`s10-disclosure`, Sonnet 5 / high).

## 2026-08-05T07:28:08Z — STAGE 10 ACCEPTED

- `outputs/10_PUBLICATION_TECH.md` + `outputs/10_DISCLOSURE_MAP.csv` written by `s10-disclosure`; parent validated CSV schema (11 exact columns, 51 rows F01-F51) and gate: PASS.
- Strongest groups: UHV/GDC module (detailed but enablement-thin), Hall device/fab (attributed to prior group refs 10/11), deployment/validation (best-evidenced).
- Graphite shield F16 = thinnest enablement; absences F38-F48 map directly onto IP_SCOPE.md OTL questions.
- Novelty assertions are cover-letter-only (p.9): F49 "first GaN Hall in stellarator", F50 "first deployment/validation of platform", F51 unsupported sensitivity comparison vs ITER/DEMO metal probes. Rendered body has no sensor "first" claim.
- Future work F33-F37 stayed future/no/no; no excluded concept treated as implemented.
- Checkpoint `state/checkpoints/10_done.json` created. Proceeding to stage 20 (`s20-prior-art`, Sonnet 5 / xhigh).

## Stage 20 in progress — intermediate coverage-area-1 report received by parent

- A stage-20 research fork delivered its coverage-area-1 (fusion/plasma Hall diagnostics) verification summary to the parent while the stage agent continues assembling the ledger. Highlights the parent will cross-check against the final CSV/search log:
  - Seeds S015-S021 verified (S016/S017/S021 verified_abstract at tier A via IOPscience; S018/S019/S020 verified_abstract at tier B via Semantic Scholar fallback after publisher 403s; S015 verified_metadata only — AIP+mirror blocked; its "20-element array" content detail is lead_only).
  - S016 = manuscript ref5 (JET InSb 3-axis probes, 2009-2021, >19k pulses); S017 = ref6 (DEMO gold-film metal Hall); S018/S020 are one ITER-OVSS bismuth family (plus 4 lead_only family members); S019 ceramic-chromium packaging contrast; S021 = ref17 (HSX coil-based diagnostics — confirms no pre-existing HSX Hall probe).
  - Structurally useful negatives: W7-X uses coil-only magnetic diagnostics (lead_only); NO reference found combining any III-nitride Hall sensor with in-vessel fusion deployment — documented gap, not a verified universal negative.
  - No post-2026-07-02 material encountered in this area. Saturation declared for coverage area 1; residual weakness is verification depth (4 rows abstract/metadata-level due to publisher blocking), flagged for stage 30 if load-bearing.

## 2026-08-05T08:03:17Z — STAGE 20 ACCEPTED

- `outputs/20_PRIOR_ART.csv` (40 rows, exact 17-column schema) + `outputs/20_SEARCH_LOG.md` written by `s20-prior-art`; parent read both in full and validated the gate: PASS. 22/22 seeds verified; N001-N018 added; all six coverage areas saturated with explicit statements; lead_only rows (N004, N012) firewalled.
- Central finding (concept 3): no source found combining grounded + graphite shield + epoxy-encapsulated sensor + GDC-arcing/epoxy-degradation purpose. Ranked analogs: N017 W7-X Mirnov graphite panels (thermal purpose, grounding unconfirmed), N015 1985 DOE flux-loop graphite armor, N005 1989 DOE RF-antenna graphite-ceramic shield, N006 general grounded-shield-arc-suppression principle, N008 SST-1 GDC (ceramic covers; competing float-not-ground philosophy noted). Epoxy 150C/1h bake = manufacturer standard cure; LCC UHV packaging routine.
- Concept 2: no GaN/AlGaN Hall in any fusion deployment found; nearest N016 = 2014 GaAs Hall array in-vessel at CTH (stellarator-class), narrows the cover-letter "first" claim.
- Concept 1: S009 US11137310B2 closest device patent (adds simultaneous temperature measurement); octagon geometry generic across materials (N013/N014) and is ref10's contribution anyway; no Stanford/group patent found.
- Doctrine/OTL: MPEP 2112.02 + 2141/2143 read directly; arXiv = irrevocable disclosure; OTL will not file post-disclosure; Bayh-Dole reporting applies; arXiv TeX rules confirm stage-00 ZIP hygiene finding.
- Process deviation documented (search log §0): two of six forks compacted mid-task and wrote drafts directly to outputs; stage agent cross-validated, repaired, and re-verified. Parent noted minor S015 verification tension (immaterial to conclusions).
- Checkpoint `state/checkpoints/20_done.json` created. Proceeding to stage 30 (`s30-ip-screen`, Fable 5 / xhigh — first Fable integrity-policy stage; flag count 0).

## 2026-08-05T08:13:38Z — STAGE 30 ACCEPTED (Fable stage, no integrity event)

- `outputs/30_IP_SCREEN.md` + `outputs/30_CLAIM_CHART.csv` (22 rows, exact 12-column schema) written by `s30-ip-screen` on Fable 5/xhigh; parent read both in full; gate PASS. No flag/refusal/substitution; flag count stays 0.
- Dispositions: C1 screen_out (high conf); C2 screen_out standalone (In re May side of MPEP 2112.02; KSR substitution; "first" claims cover-letter-only); C3 conditional_hold — strongest surviving candidate (shield F16 novelty risk medium via documented gap, obviousness risk high, enablement thin); C4 screen_out (medium conf, search-depth limit); C5 screen_out (high conf, ~zero commercial value).
- Record tension flagged for stage 50: intro claim that conventional semiconductors "cannot be deployed near the plasma edge" vs verified InSb/GaAs in-vessel deployments (S015/S016/N016).
- Decisive gaps ranked (shield conception, without-shield comparison, float-vs-ground/W7-X grounding, UHV criterion, UW-Madison contribution).
- Checkpoint `state/checkpoints/30_done.json` created. Proceeding to stage 40 (`s40-uhv`, Fable 5 / xhigh).

## 2026-08-05T08:24:48Z — STAGE 40 ACCEPTED (Fable stage, no integrity event)

- `outputs/40_UHV_PACKAGE_VERDICT.md` + `outputs/40_EVIDENCE_GAPS.md` written by `s40-uhv` on Fable 5/xhigh; parent read both in full; gate PASS. Flag count stays 0.
- Verdict: module NOT established as more than routine packaging on the public record; C3 conditional_hold narrowed to inventor-held-evidence dependency; calibrated expectation of no publication-specific filing case absent the G1+G2+G3 bundle.
- External verification this stage: V40-A (PPPL 1979 PDX GDC report, OSTI 5515925, verified_full) documents the full KSR motivation chain since 1979 and weakens the float-vs-ground teaching-away lead; W7-X Mirnov center-tap grounding confirmed, panel grounding still open (G8, paywalled companion).
- Latent delta G4 (conductivity/thickness/bandwidth trade-off) flagged as the strongest possible inventor-held technical delta; design-around easy; detection extreme.
- Checkpoint `state/checkpoints/40_done.json` created. Proceeding to stage 50 (`s50-arxiv`, Sonnet 5 / high).

## 2026-08-05T08:35:37Z — STAGE 50 ACCEPTED

- `outputs/50_ARXIV_RISK.md` + `outputs/50_SOURCE_SCRUB.md` + `outputs/50_OTL_INTAKE.md` written by `s50-arxiv`; parent read all three in full; gate PASS.
- Label: HOLD_ARXIV_FOR_OTL (C3-scoped only; C1/C2/C4/C5 carry no hold). Release conditions: OTL clearance/filing, documented informed PI decision, or confirmed earlier public disclosure (G10).
- Load-bearing analysis: arXiv adds no new technical content vs the journal submission; the decision is about accelerating/irrevocably starting the public-disclosure clock before the stage-40 evidence bundle exists. MPEP 2153.01(a) authorship-vs-inventorship nuance flagged. IEEE policy verified: arXiv posting permitted, not prior publication — IEEE side is not a hold reason.
- Scrub: ZIP not upload-ready (strip .aux/.log/.synctex.gz/.pdf; path leak resolved by exclusion; eps/pdf duplication new finding; cover letter must never reach arXiv). Timeline anchors: figures June 2026, submission bundle 2026-07-02, cover letter affirms no preprint as of that date; G10 + current review status are the controlling unknowns.
- Checkpoint `state/checkpoints/50_done.json` created. Proceeding to stage 60 (`s60-red-team`, Fable 5 / xhigh; flag count 0).

## 2026-08-05T08:44:22Z — STAGE 60 ACCEPTED (Fable stage, no integrity event)

- `outputs/60_RED_TEAM.md` written by `s60-red-team` on Fable 5/xhigh; parent read in full; gate PASS. Flag count stays 0.
- C3 fails the best adversarial case: KSR scissors (supported=obvious / narrow=unsupported), inherent-result strip of the functional language, facility-conception origin attack, ~3.4 s cumulative plasma exposure with GDC never narrated. No premature kills among C1/C2/C4/C5.
- Bias audit overturned/weakened: bounded-search absence was operationally load-bearing (low probative weight); GDC-exposure benefit of doubt withdrawn; G4 lifeline struck; inheritance momentum named. HOLD_ARXIV_FOR_OTL sustained only as a time-boxed checkpoint (PI decision date, condition (b) default) on irrevocability/ownership/sponsor-duty grounds.
- Steelman needs ~6 contingencies; even then obviousness only medium, enforceability ~zero. Economics: no full prosecution on any evidenced scenario; provisional only if G1+G2+G3 appear in the window.
- Handoff: stage-70 lead NO_PUBLICATION_SPECIFIC_FILING_CASE_IDENTIFIED unless bundle produced; keep time-boxed checkpoint.
- Checkpoint `state/checkpoints/60_done.json` created. Proceeding to stage 70 (`s70-final`, Fable 5 / xhigh; flag count 0).

## 2026-08-05T08:53:55Z — STAGE 70 ACCEPTED — RUN COMPLETE

- `outputs/70_FINAL_OTL_BRIEF.md` + `outputs/70_EXEC_SUMMARY.md` + `outputs/70_MODEL_REPORT.md` written by `s70-final` on Fable 5/xhigh; parent read all three in full; stage-70 and global gates PASS. No Fable integrity event at any stage; cumulative flag count 0.
- Decision: NO_PUBLICATION_SPECIFIC_FILING_CASE_IDENTIFIED, with a time-boxed pre-posting OTL checkpoint (PI-set decision date, release condition (b) default) justified by irrevocability, unresolved ownership, and patentability-independent sponsor duties — the stage-50/60 conflict resolved, not averaged.
- Three answers: device no (high conf); fusion new use no standalone case; UHV/GDC module too routine/thin as filing candidate but included candidly in checkpoint intake for sponsor/ownership reasons.
- All 16 deliverables exist and are nonempty (verified). Every critical conclusion cited to ledger source_ids/URLs and TeX lines. Checkpoint `state/checkpoints/70_done.json` created. STATE.json set to COMPLETED.
- Run totals from task-notification metadata (only exposed telemetry): 8 stages, ~1,148,031 subagent tokens total, ~90.6 minutes cumulative stage duration. Observed model/effort not_exposed throughout; requested configuration per MODEL_PLAN.md honored for all stages.
